MiSTer-devel/Hardware_MiSTer/images/header_2.54mm_Pitch-2x20_Pin-Female-Double_Row-Right_Angle_Pin.jpg

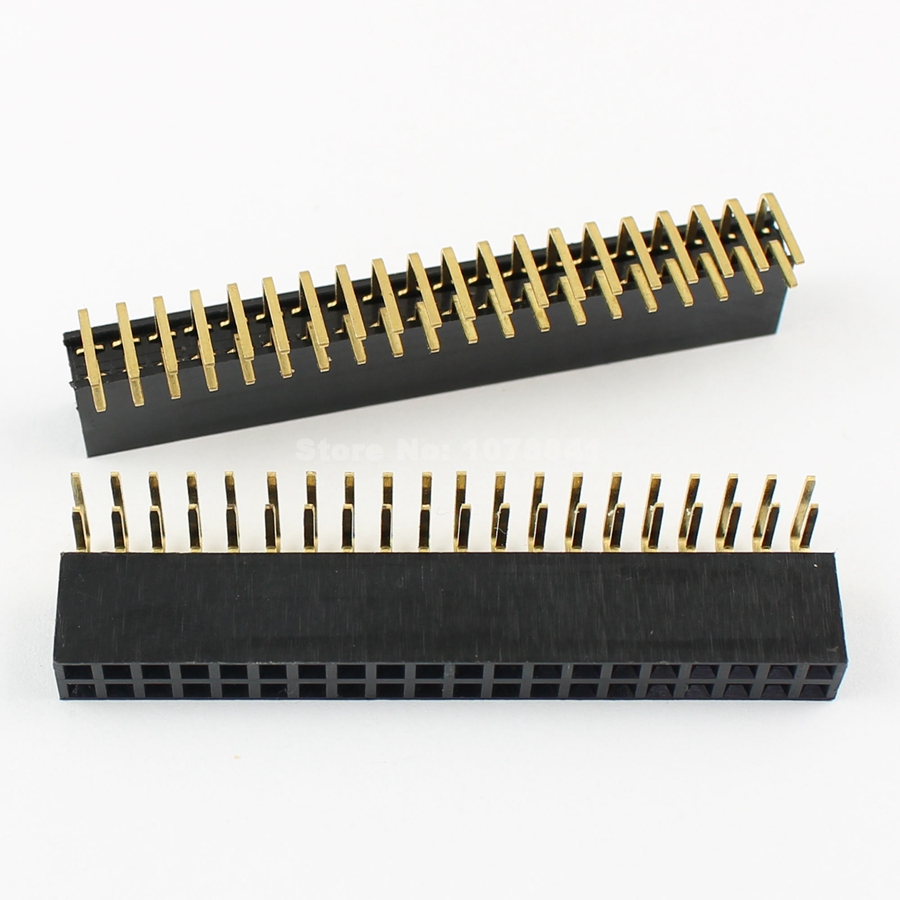
images/header_2.54mm_Pitch-2x20_Pin-Female-Double_Row-Right_Angle_Pin.jpg
