MiSTer-devel/Hardware_MiSTer/images/MiSTer_1.jpg

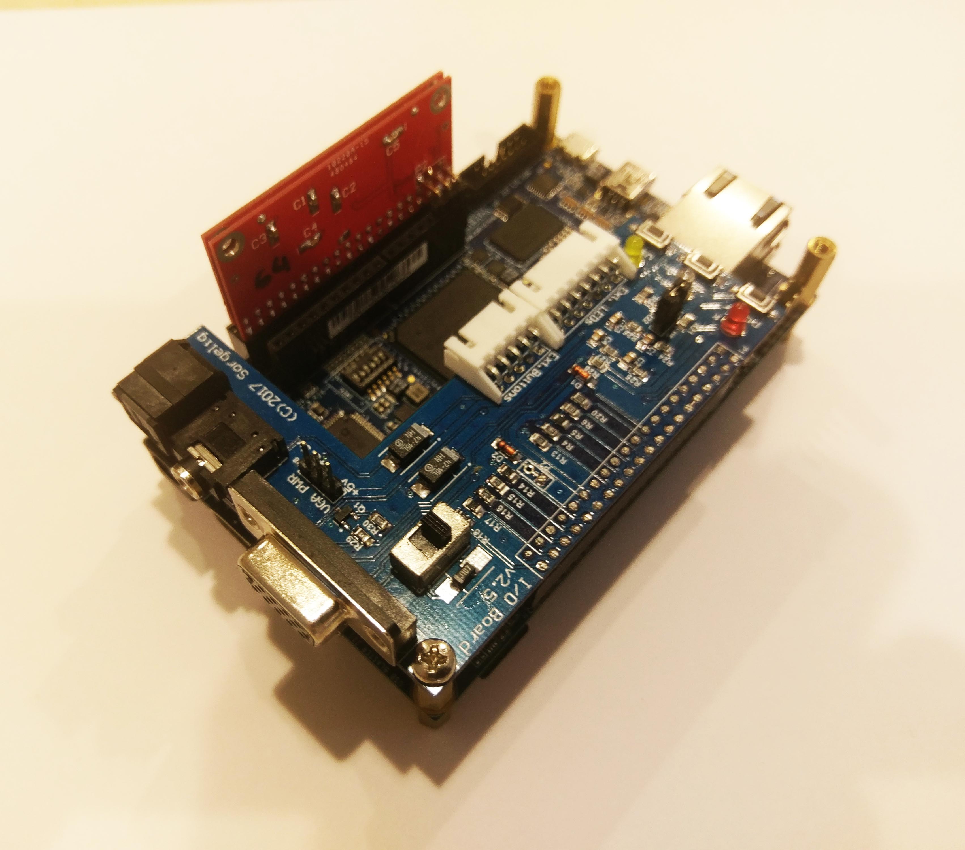
images/MiSTer_1.jpg
