MiSTer-devel/Hardware_MiSTer/images/MiSTer_AIO_SDRAM_rev.jpg

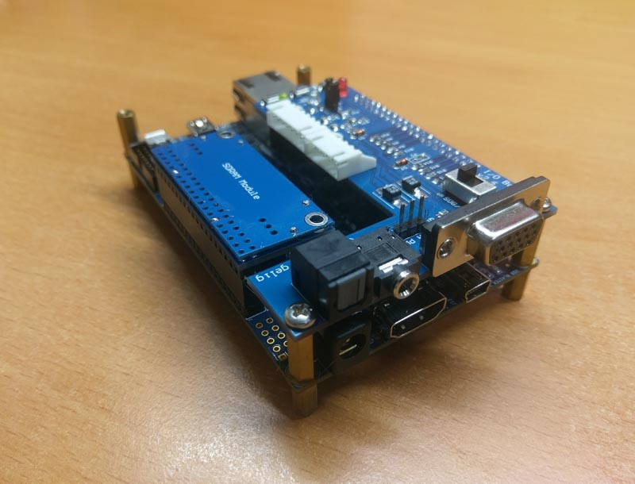
images/MiSTer_AIO_SDRAM_rev.jpg
