MiSTer-devel/Hardware_MiSTer/releases/sdram_xs_2.2.pdf

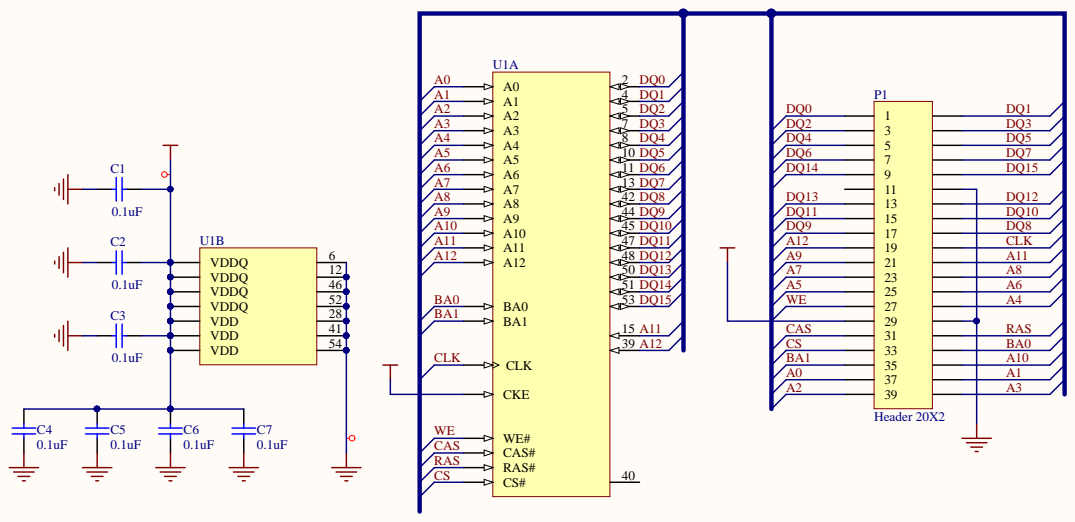
[picture p41: page 1]

SDRAM board for MiSTer (extra slim)

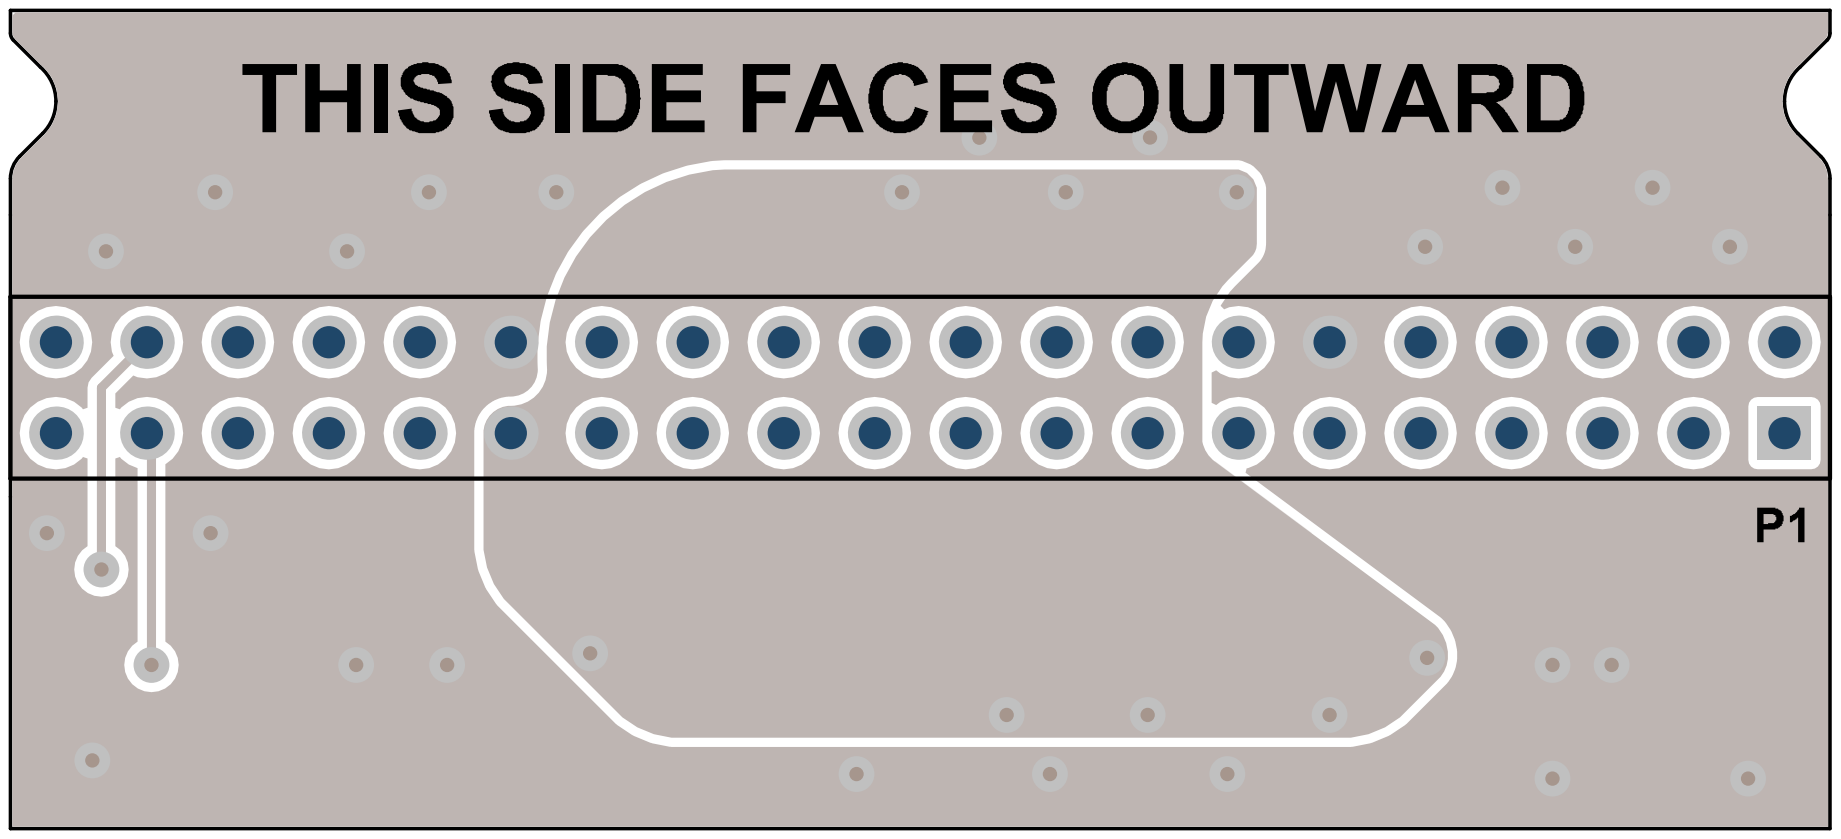
[picture p42: page 2]

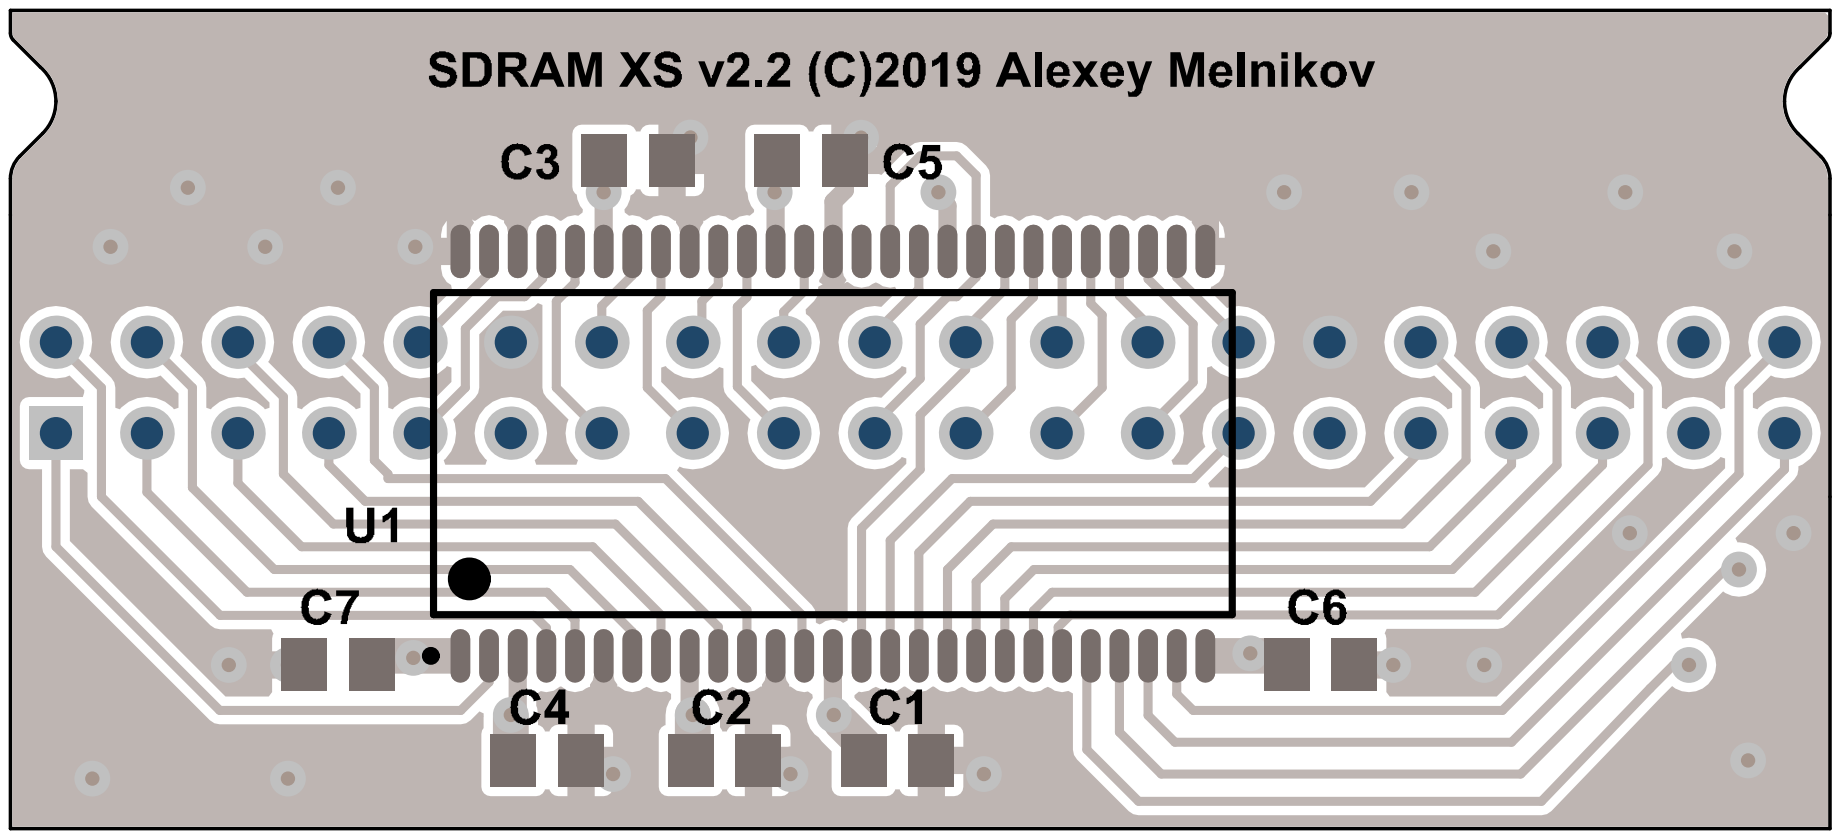
[picture p43: page 3]
