MiSTer-devel/Hardware_MiSTer/releases/iobrd_6.0.pdf

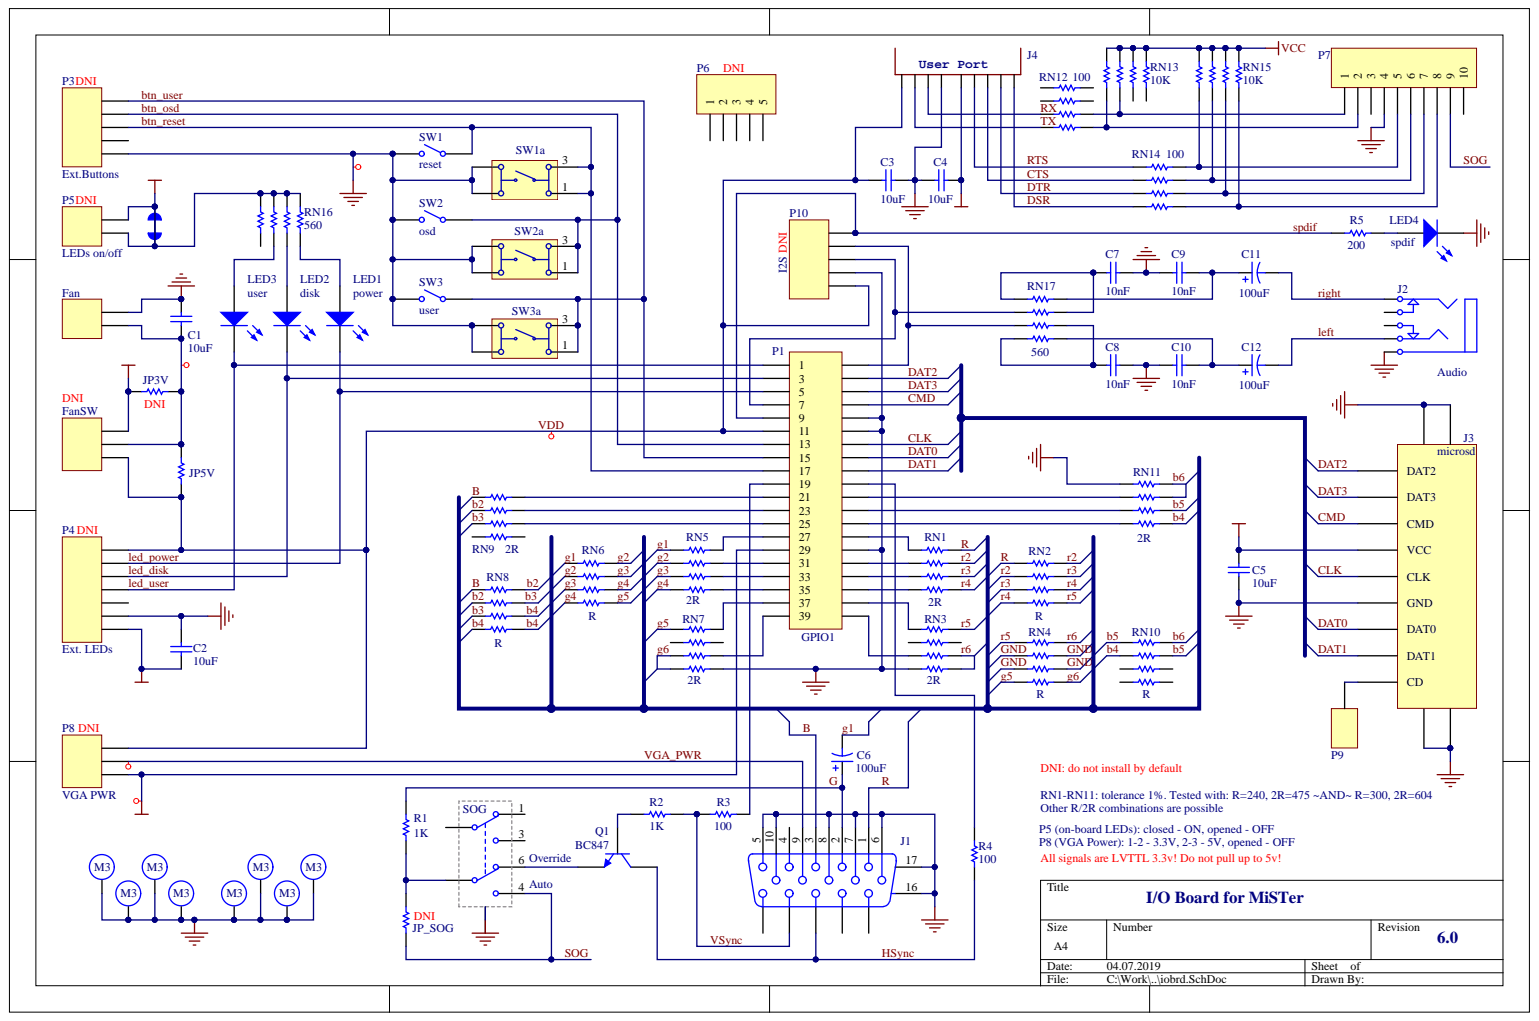
[picture p44: page 1]

C4 | | RTS

CTS
DTR

JP3V | | DAT3

VDD | CMD

CLK

DNI: do not install by default

RN1-RN11: tolerance 1%. Tested with: R=240, 2R=475 ~AND~ R=300, 2R=604
Other R/2R combinations are possible

Override 6 | J1 17

P5 (on-board LEDs): closed - ON, opened - OFF
P8 (VGA Power): 1-2 - 3.3V, 2-3 - 5V, opened - OFF
All signals are LVTTL 3.3v! Do not pull up to 5v!

VSync | 16

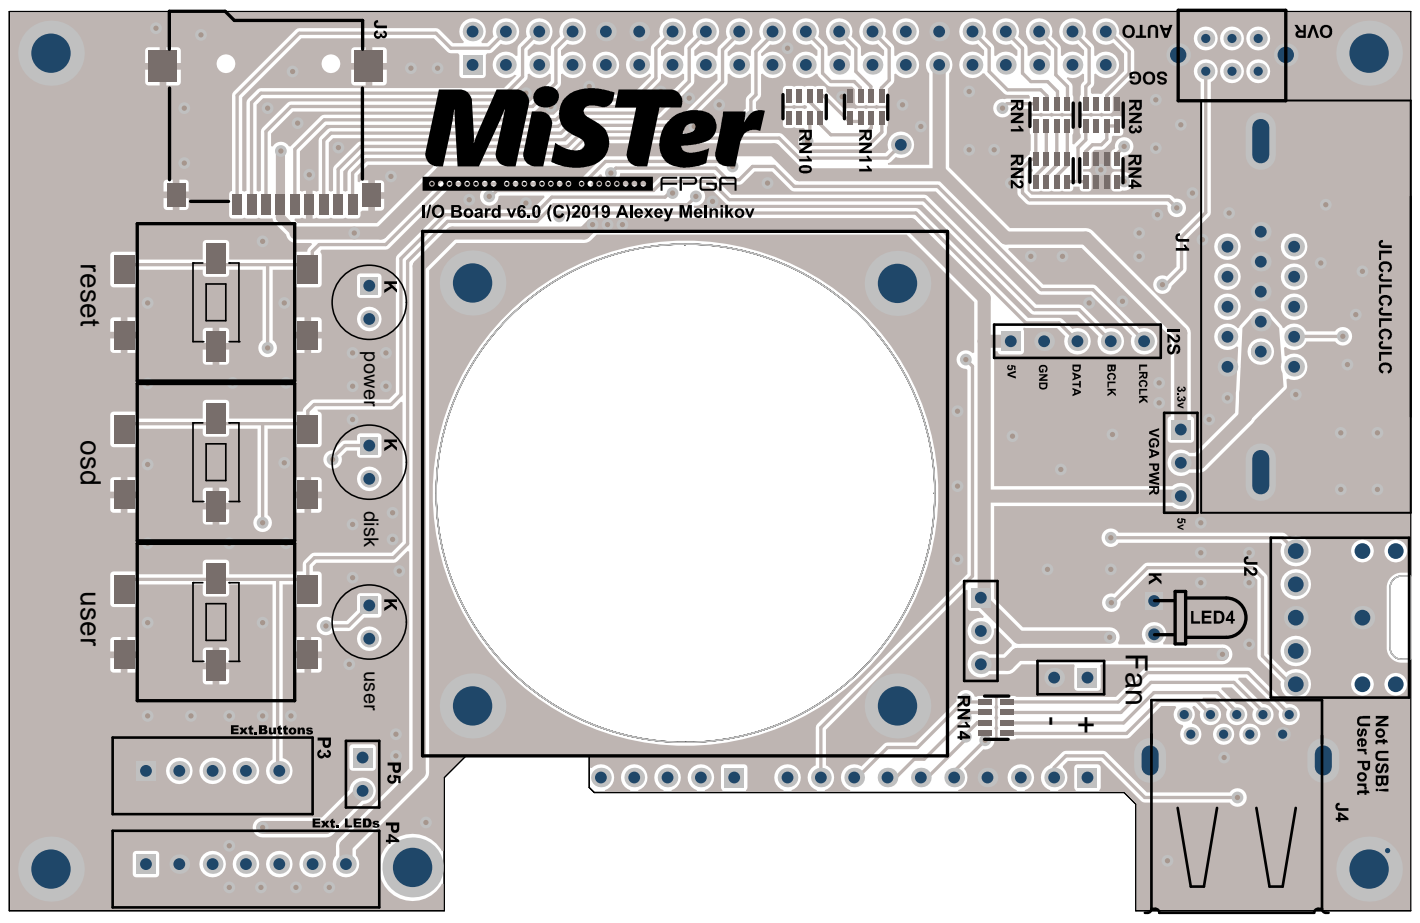
[picture p45: page 2]

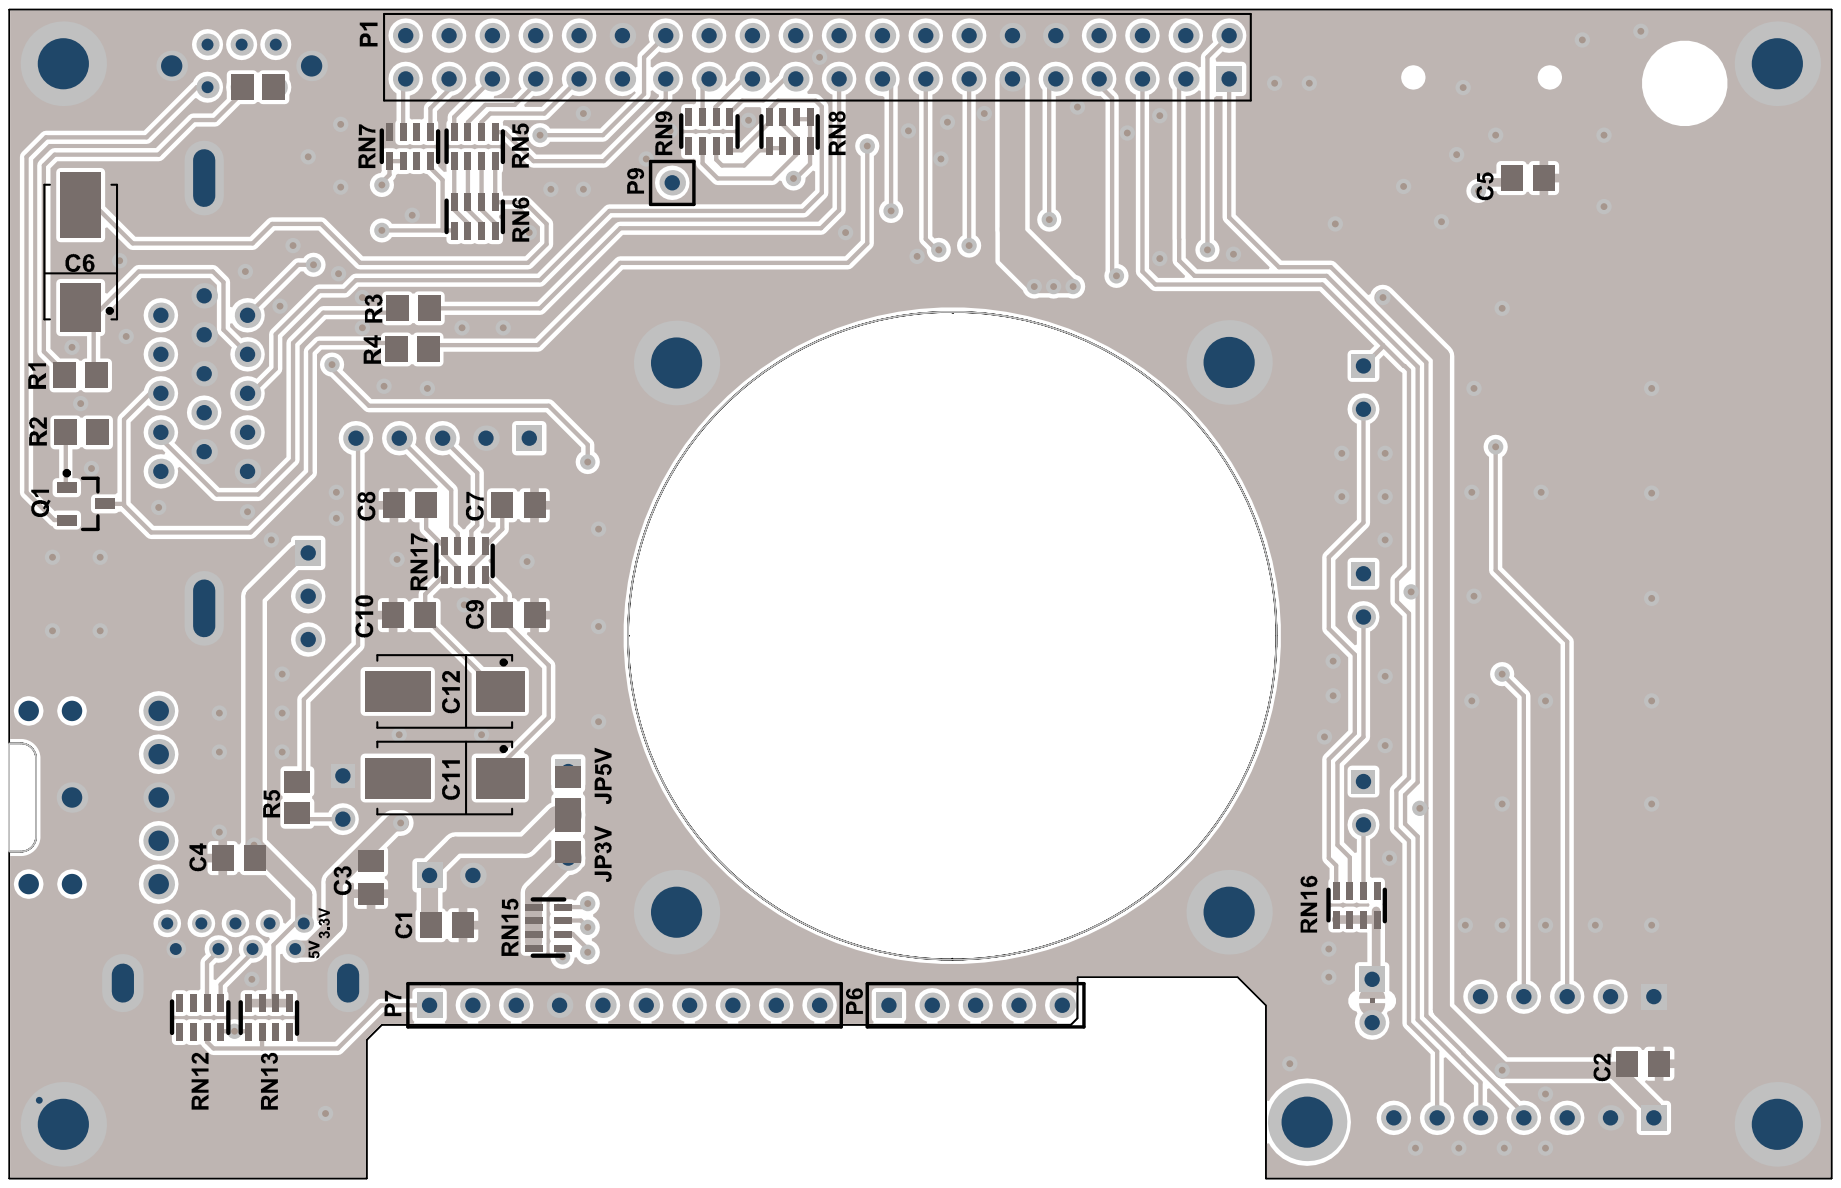
[picture p46: page 3]
