MiSTer-devel/Hardware_MiSTer/releases/USBHub_2.1.pdf

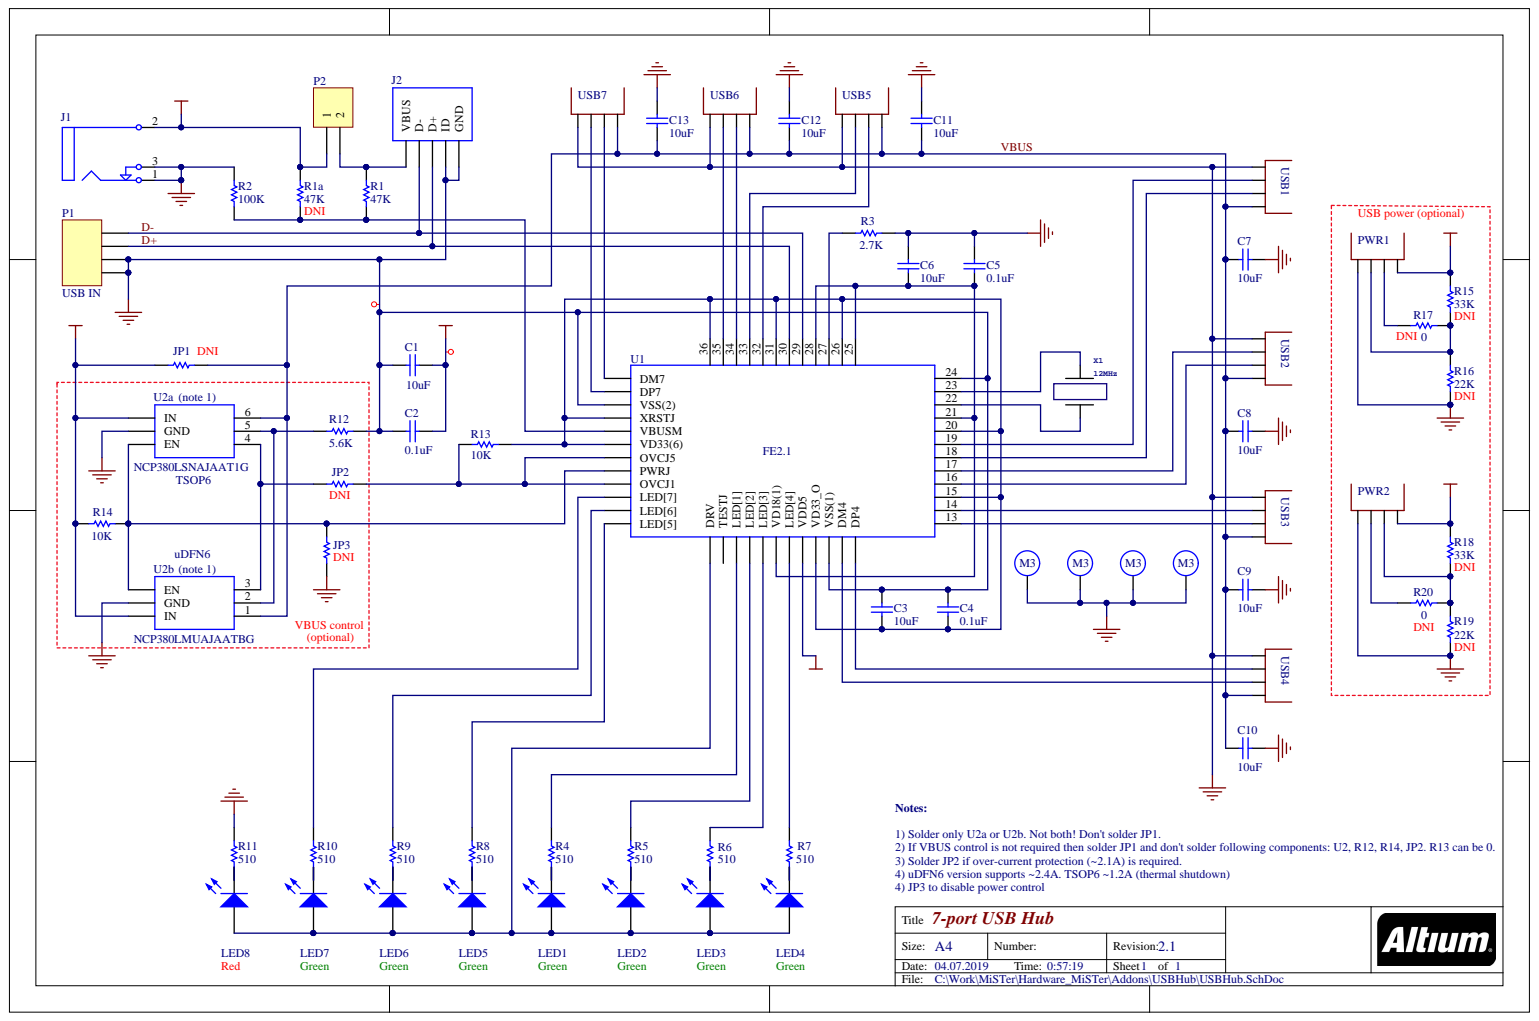
[picture p47: page 1]

DNI 0

1) Solder only U2a or U2b. Not both! Don't solder JP1.
2) If VBUS control is not required then solder JP1 and don't solder following components: U2, R12, R14, JP2. R13 can be 0.
3) Solder JP2 if over-current protection (~2.1A) is required.
4) uDFN6 version supports ~2.4A. TSOP6 ~1.2A (thermal shutdown)
4) JP3 to disable power control

7-port USB Hub Title

Size: A4 | Number: | Revision: 2.1
Date: 04.07.2019 Time: 0:57:19 | | Sheet 1 of 1

C:\Work\MiSTer\Hardware_MiSTer\Addons\USBHub\USBHub.SchDoc

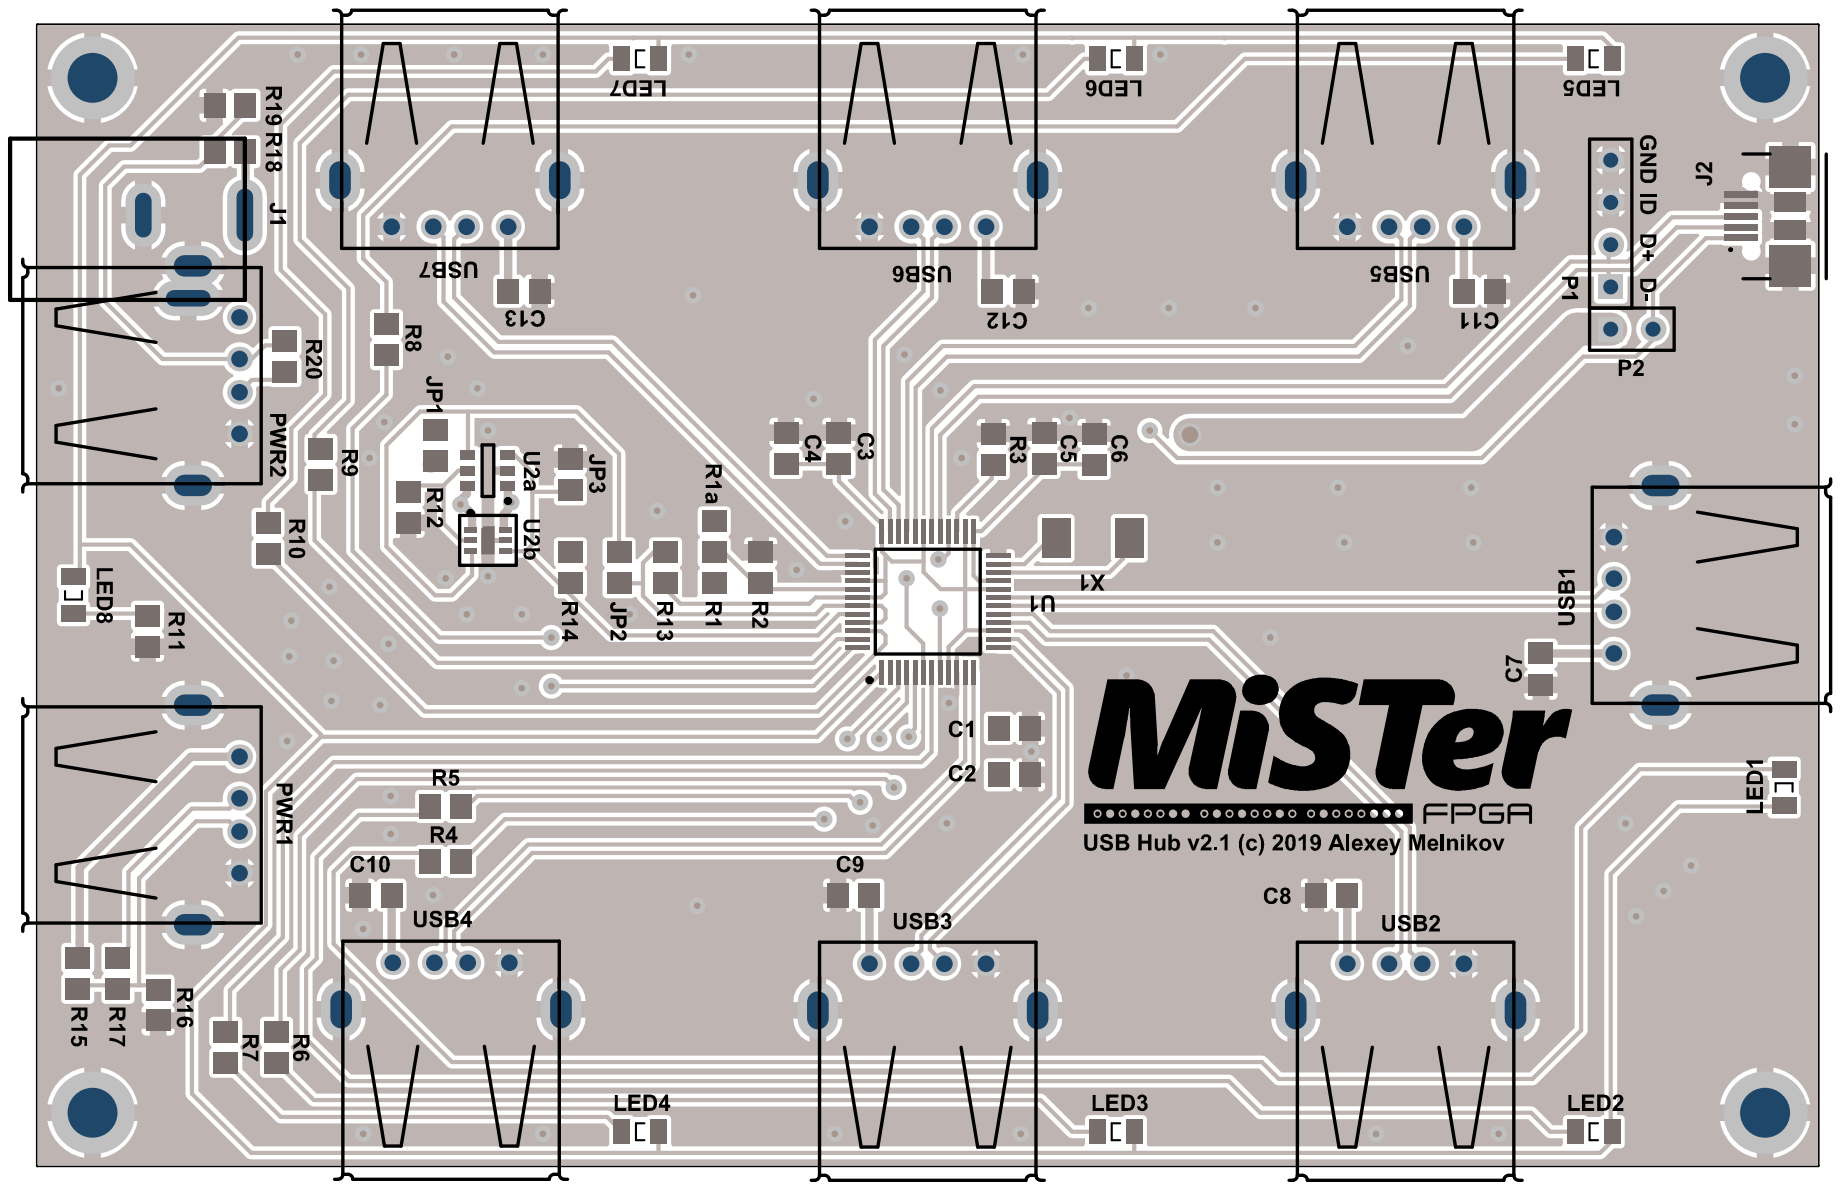
[picture p48: page 2]

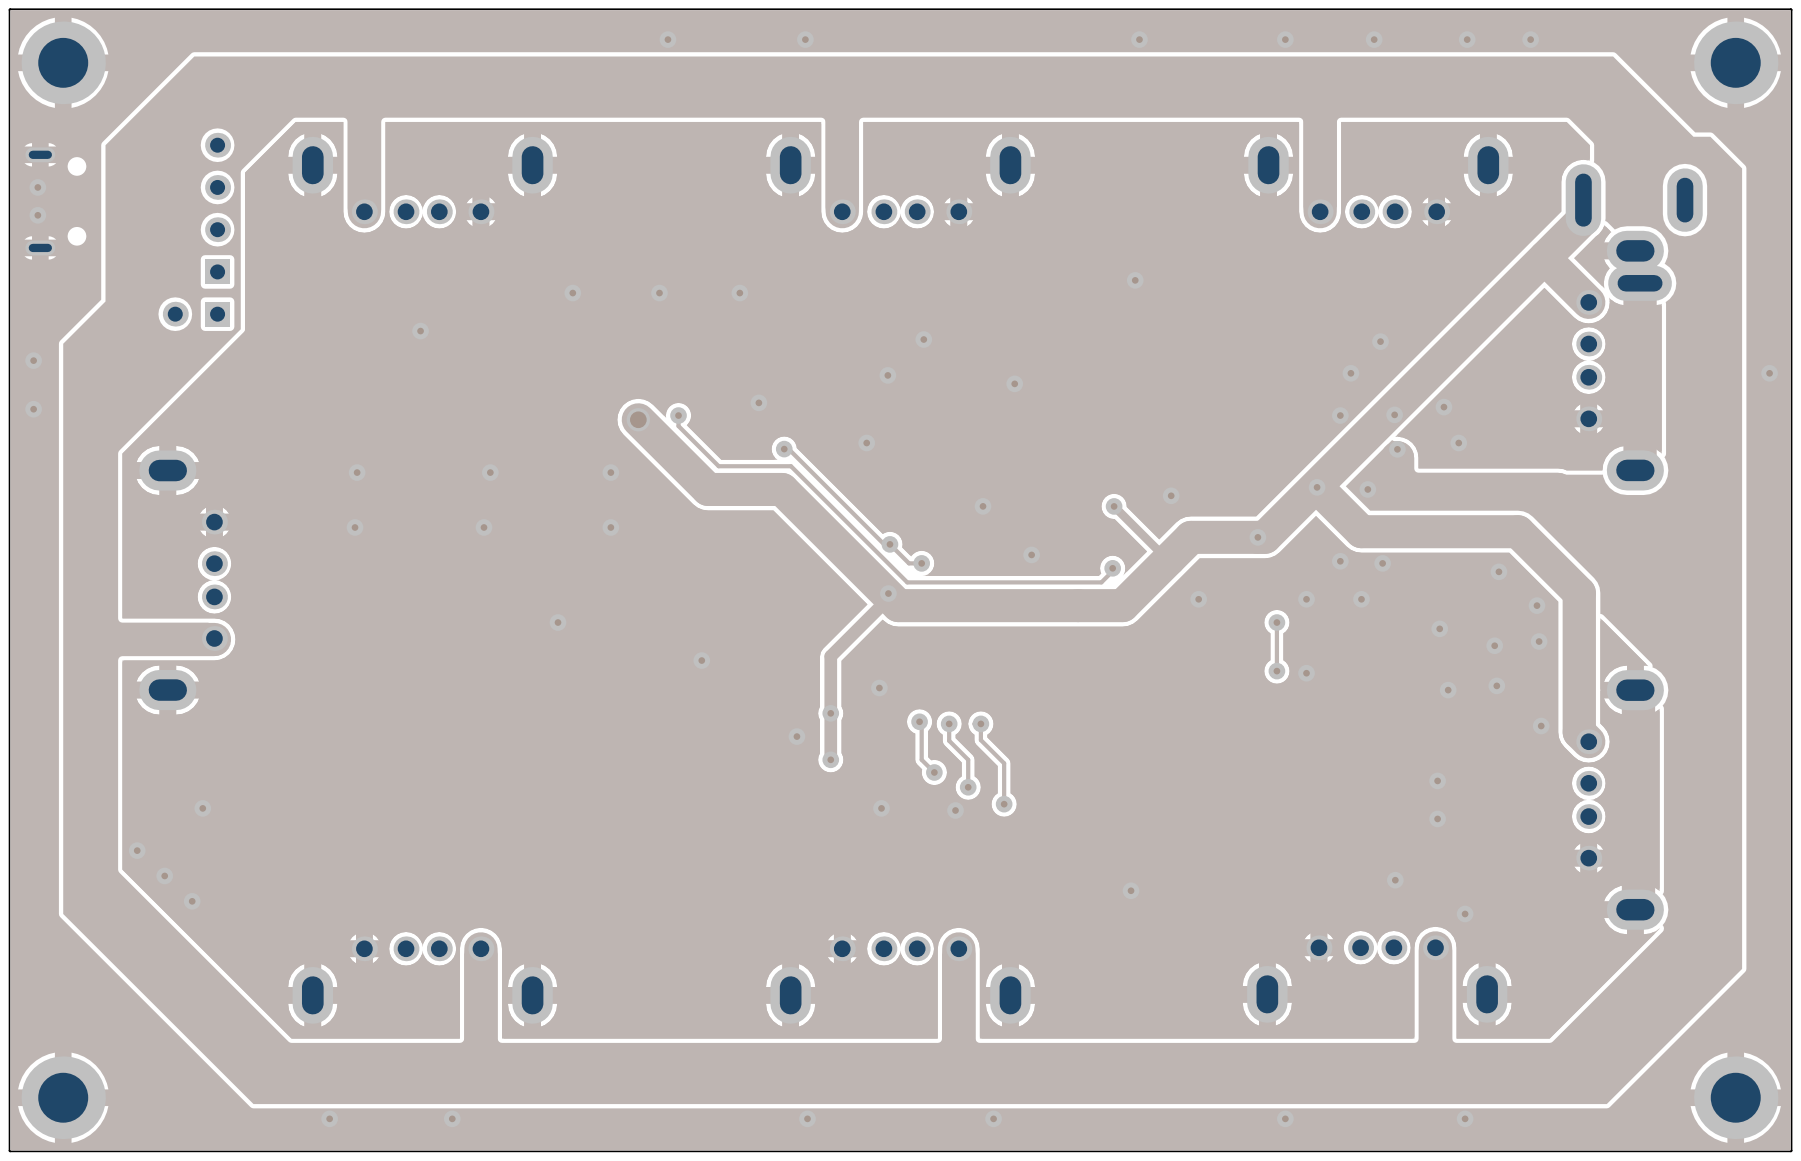
[picture p49: page 3]
