MiSTer-devel/Hardware_MiSTer/releases/ADCin_1.1.pdf

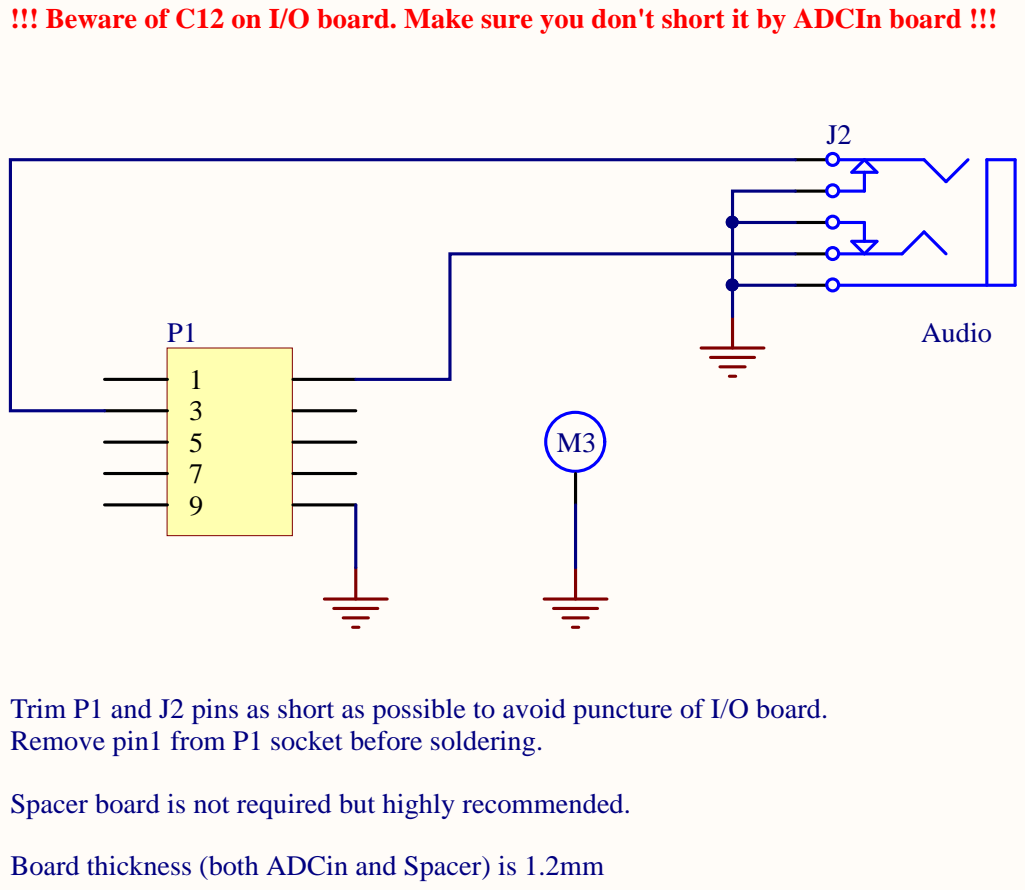
[picture p50: page 1]

!!! Beware of C12 on I/O board. Make sure you don't short it by ADCIn board !!!

Board thickness (both ADCin and Spacer) is 1.2mm Trim P1 and J2 pins as short as possible to avoid puncture of I/O board.
Remove pin1 from P1 socket before soldering.

Spacer board is not required but highly recommended.

ADC input board for MiSTer

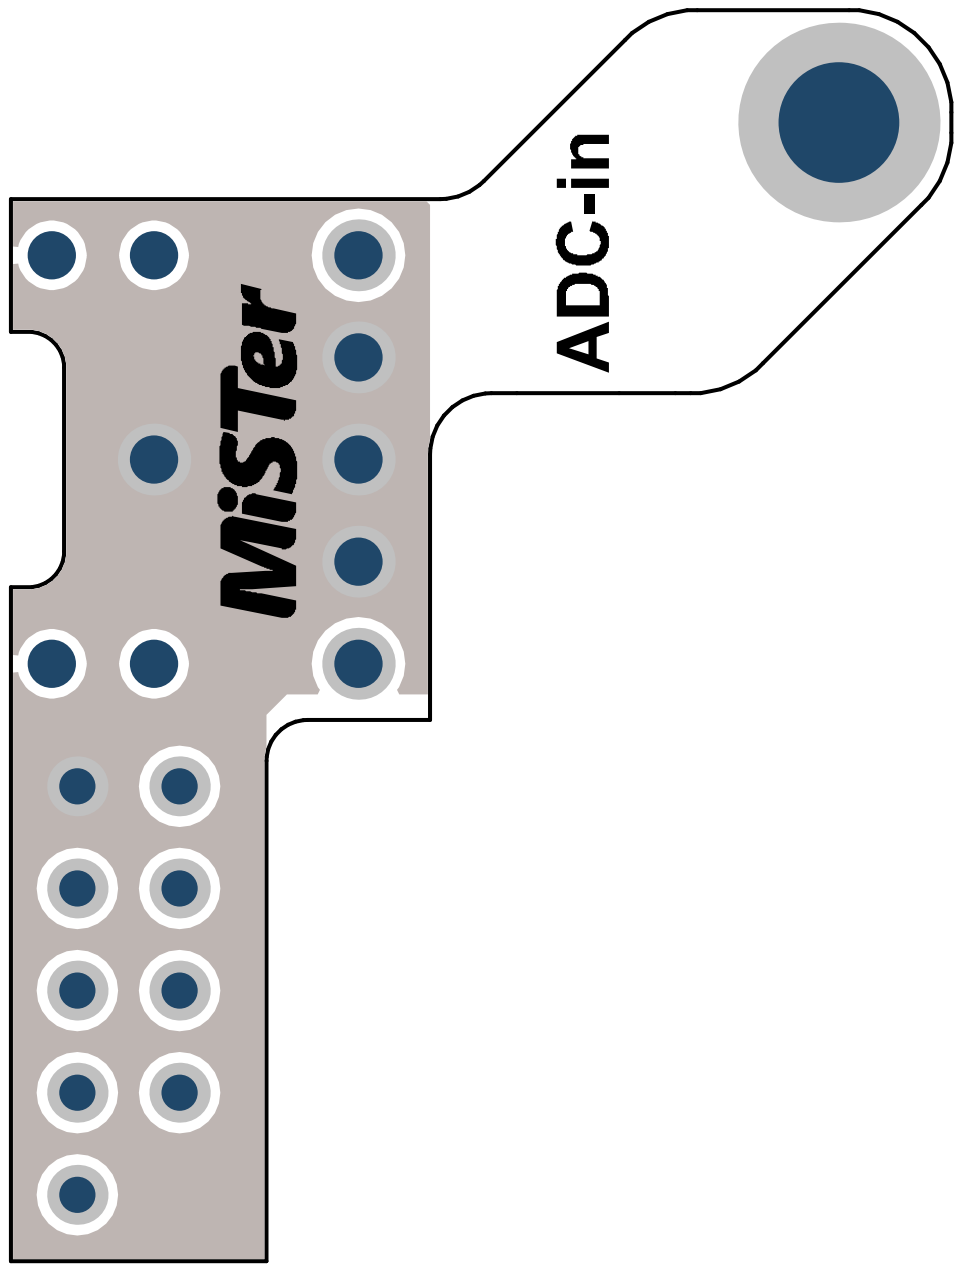
[picture p51: page 2]

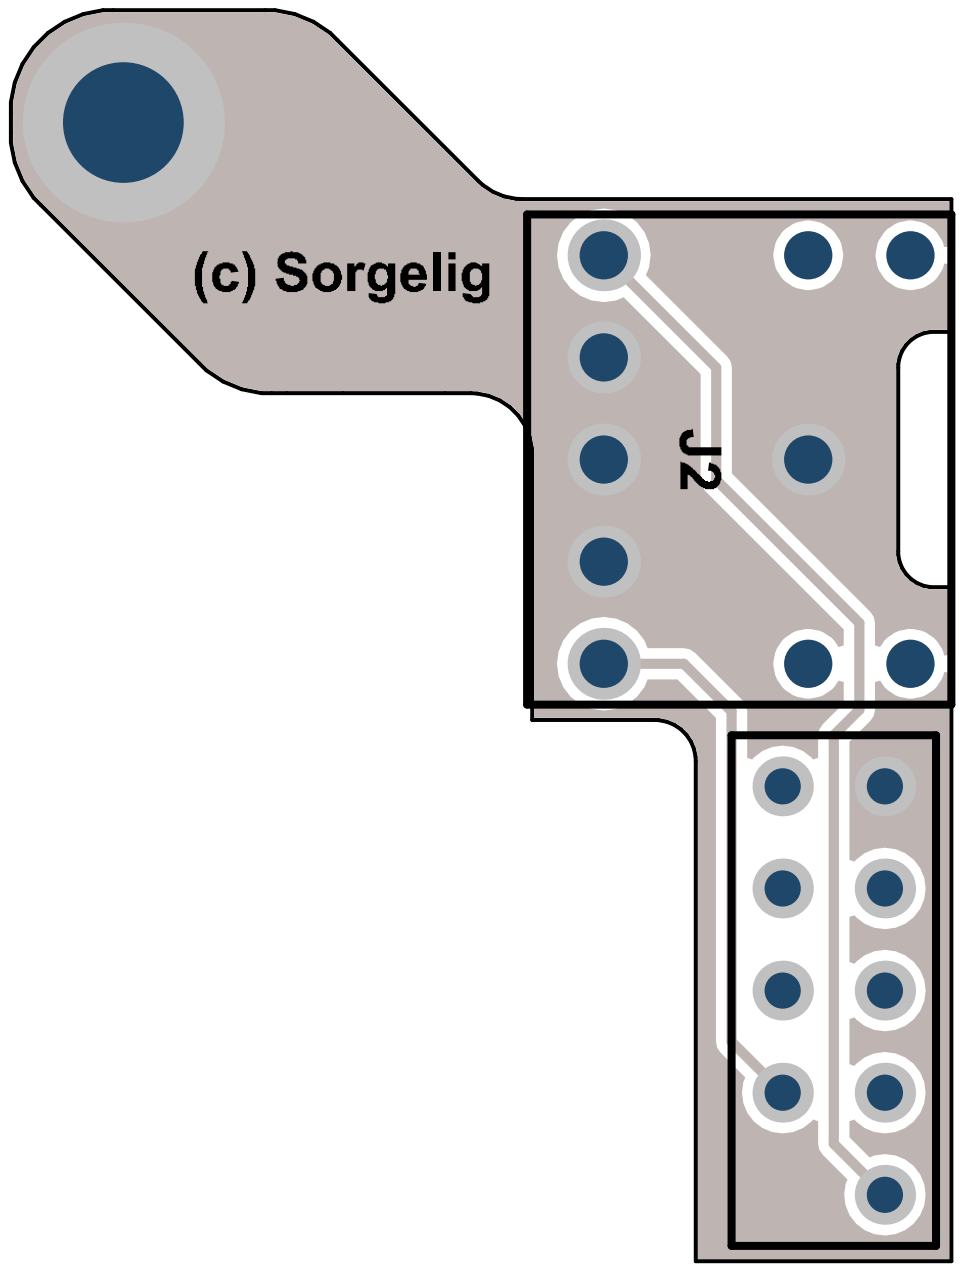
[picture p52: page 3]
