MiSTer-devel/Hardware_MiSTer/releases/iobrd_5.6.pdf

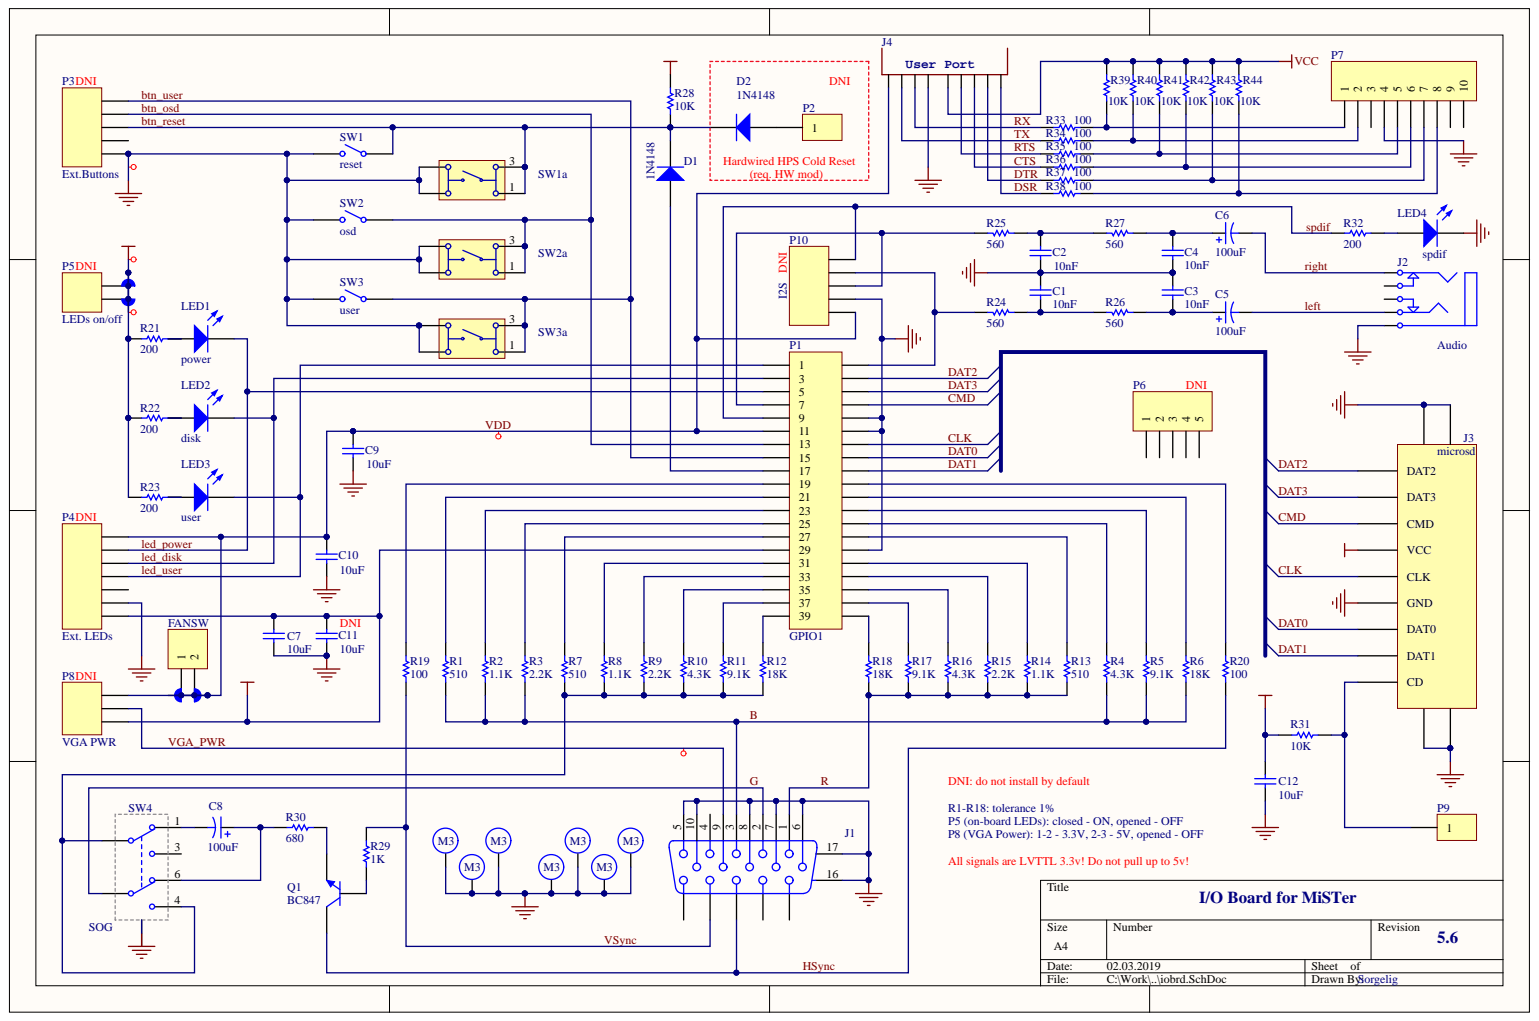
[picture p53: page 1]

btn_osd 10K

Hardwired HPS Cold Reset
(req. HW mod)

DAT2

LED2 | | | | DAT3

VDD | | | CMD

CLK

led_power
led_disk
led_user | 10uF

DNI: do not install by default

R1-R18: tolerance 1%
P5 (on-board LEDs): closed - ON, opened - OFF
P8 (VGA Power): 1-2 - 3.3V, 2-3 - 5V, opened - OFF

All signals are LVTTL 3.3v! Do not pull up to 5v!

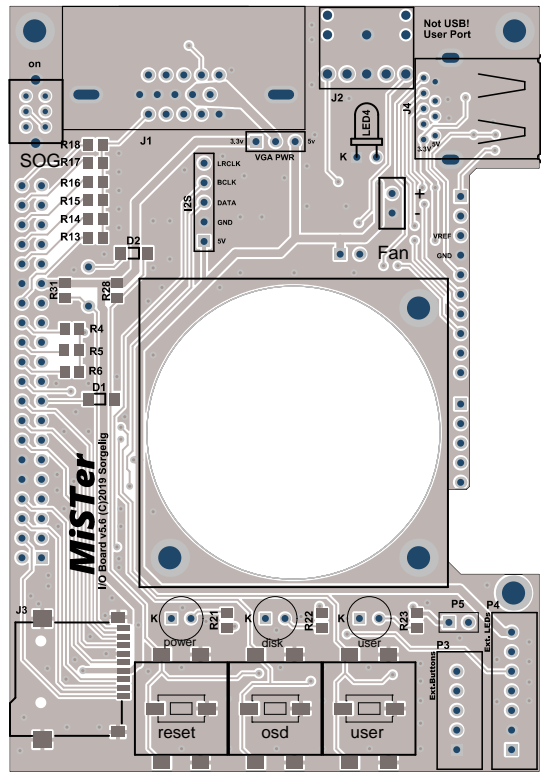
[picture p54: page 2]

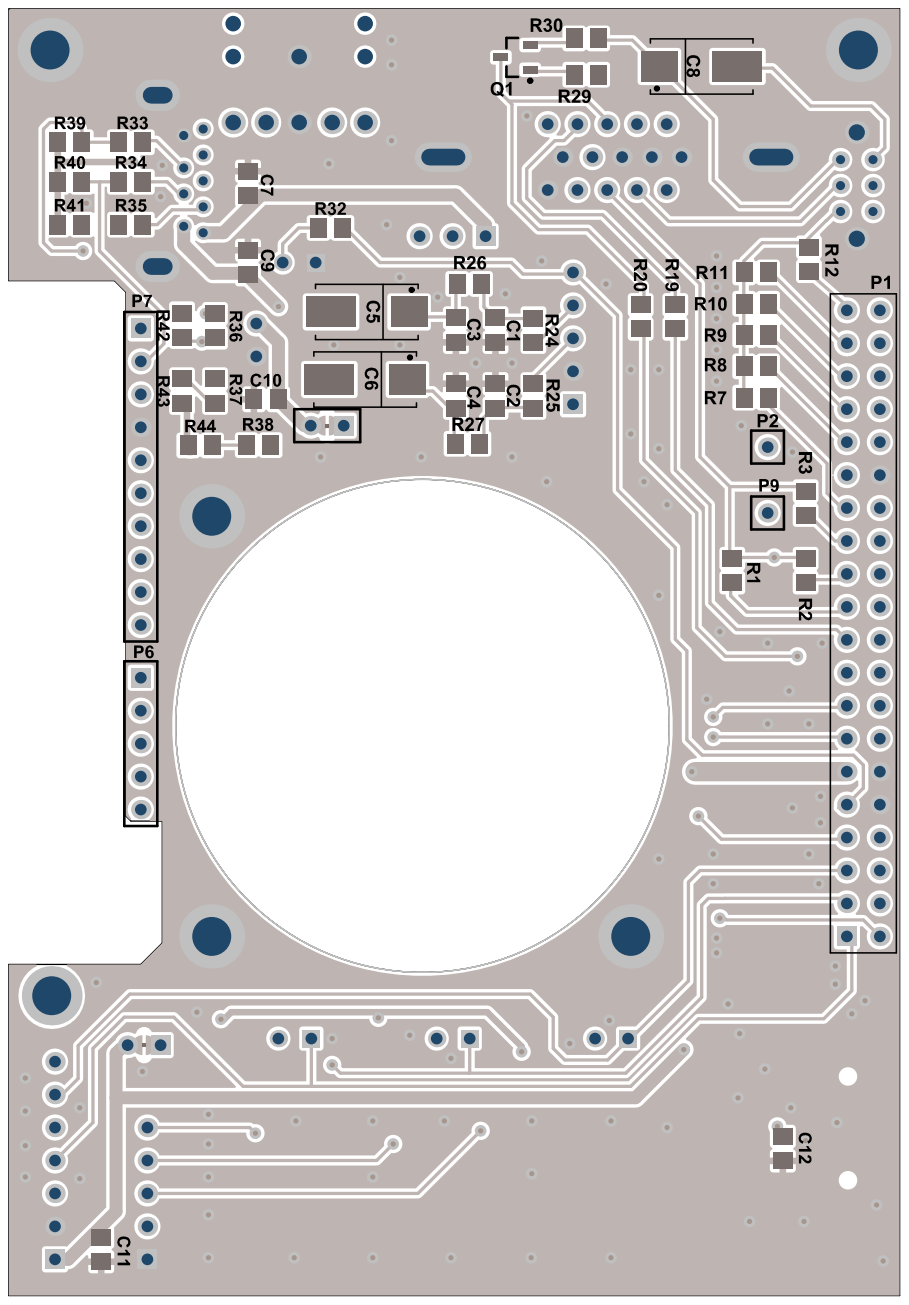
[picture p55: page 3]
