MiSTer-devel/Hardware_MiSTer/releases/iobrd_5.5.pdf

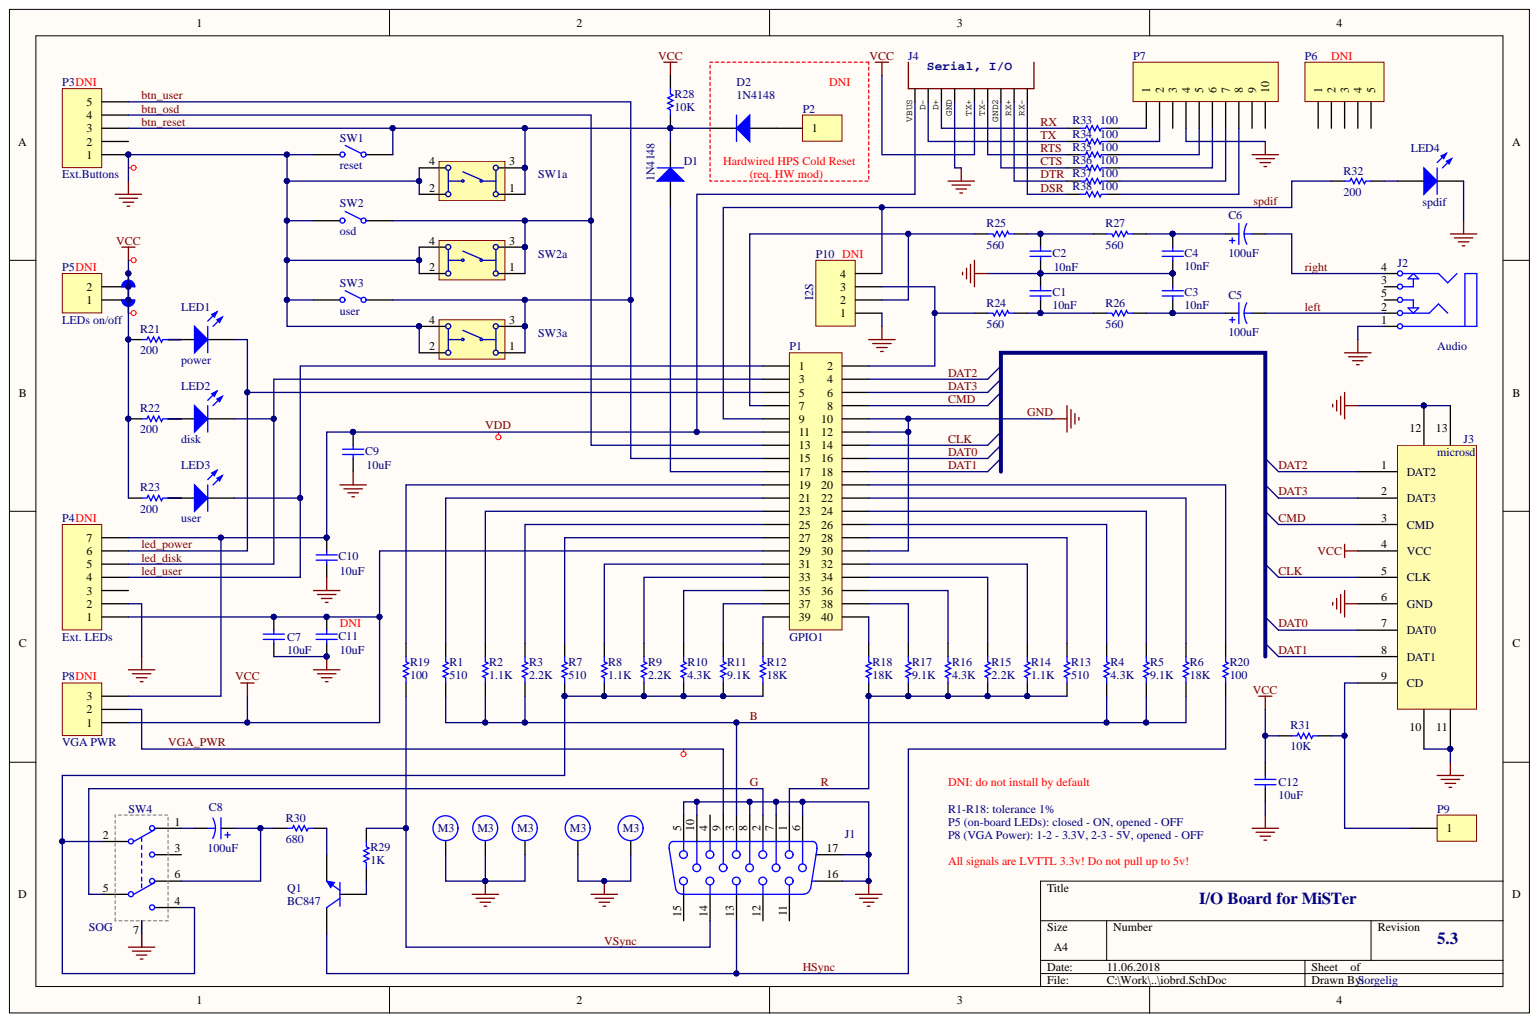
[picture p56: page 1]

Hardwired HPS Cold Reset
(req. HW mod)

DAT2

LED2 | | | DAT3

VDD | | CMD

DNI: do not install by default

R1-R18: tolerance 1%
P5 (on-board LEDs): closed - ON, opened - OFF
P8 (VGA Power): 1-2 - 3.3V, 2-3 - 5V, opened - OFF

All signals are LVTTL 3.3v! Do not pull up to 5v!

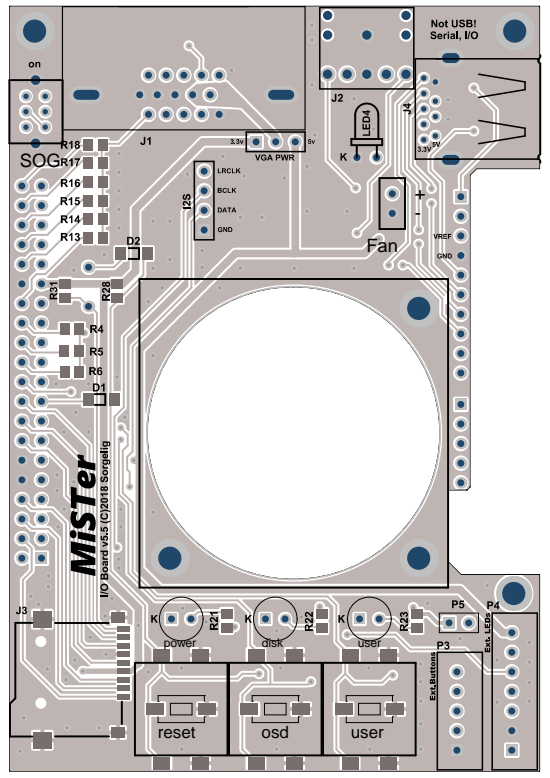
[picture p57: page 2]

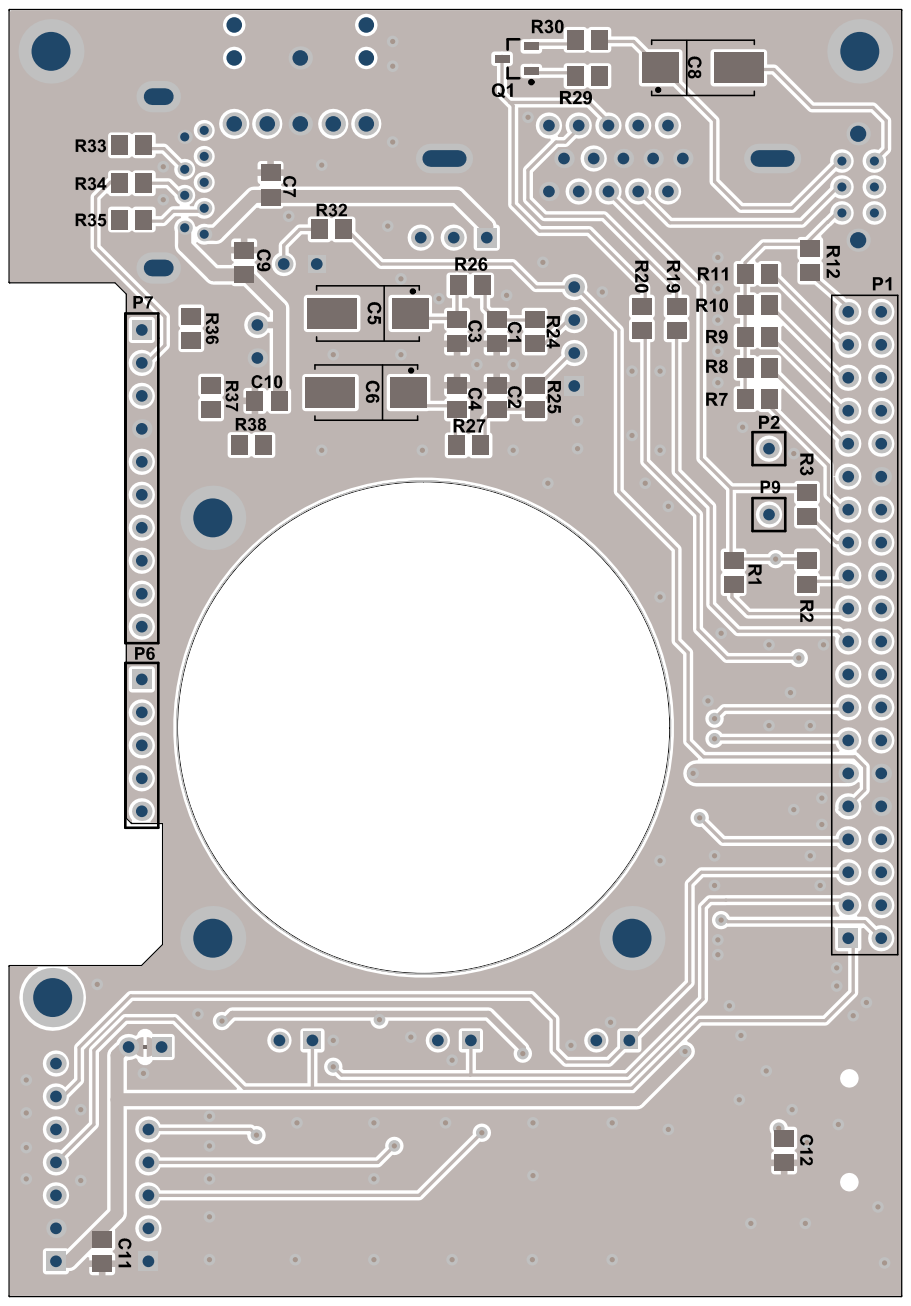
[picture p58: page 3]
