MiSTer-devel/Hardware_MiSTer/releases/USBHub_1.0.pdf

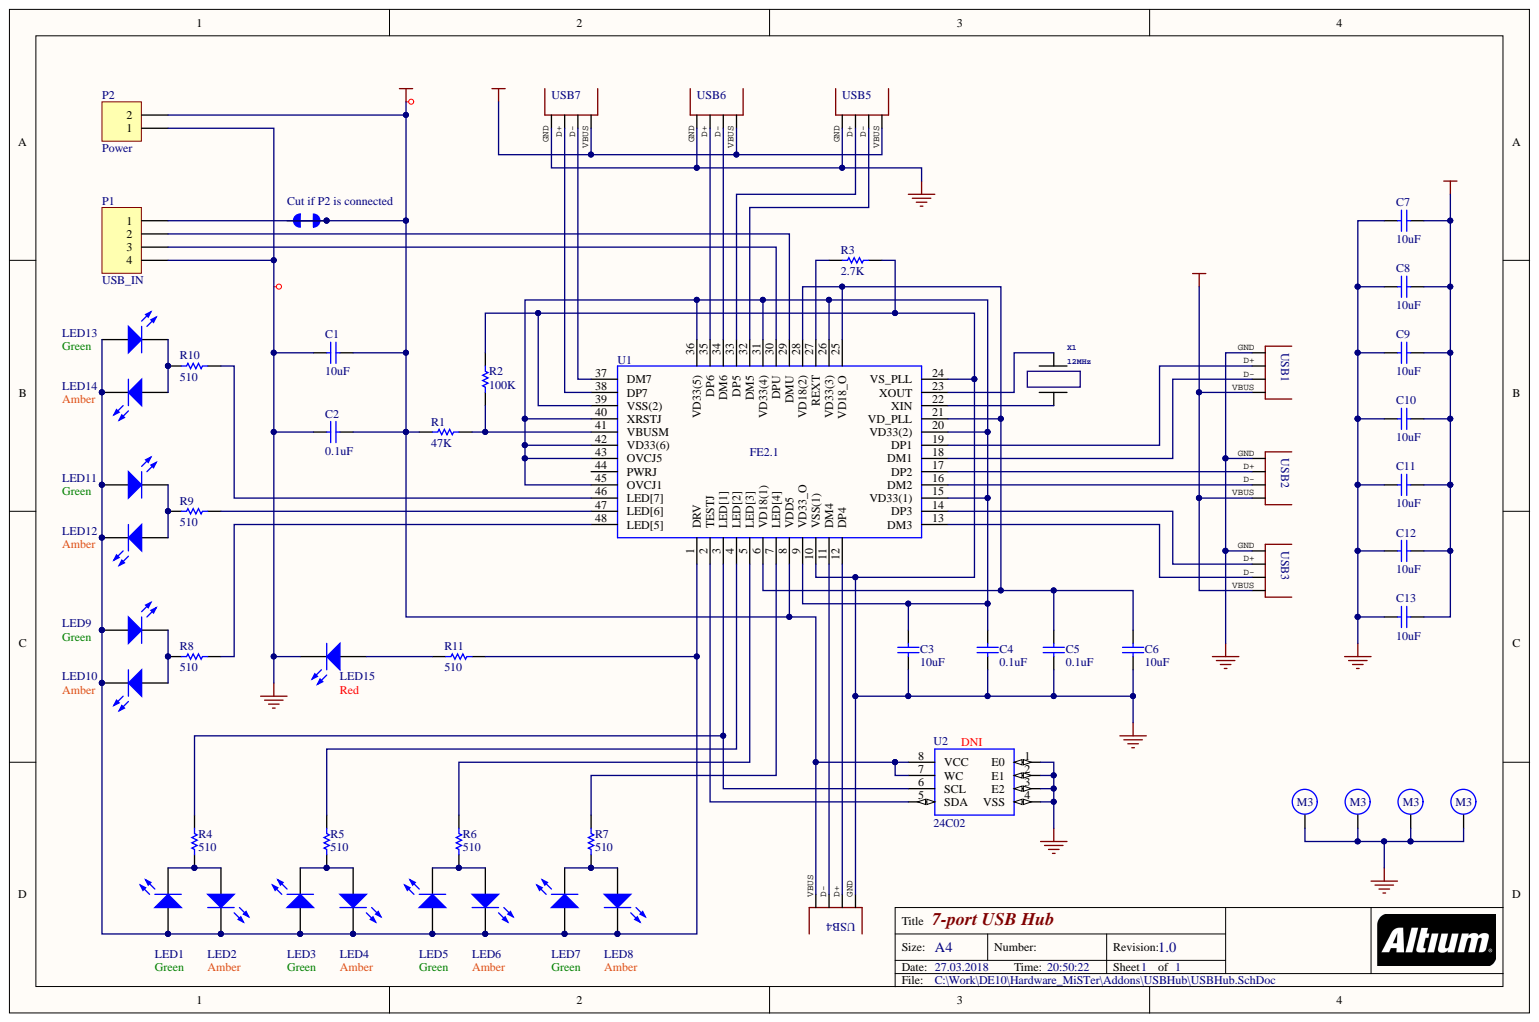
[picture p59: page 1]

Cut if P2 is connected

D-
VBUS

D+

Red | | D-

U2 DNI
VCC 8 | E1 E2
WC 7 | 2
SCL 6 | 3
SDA 5

7-port USB Hub Title

A4 Size: | Number: | 1.0 Revision:
Date: 27.03.2018 Time: 20:50:22 | | Sheet 1 of 1

C:\Work\DE10\Hardware_MiSTer\Addons\USBHub\USBHub.SchDoc

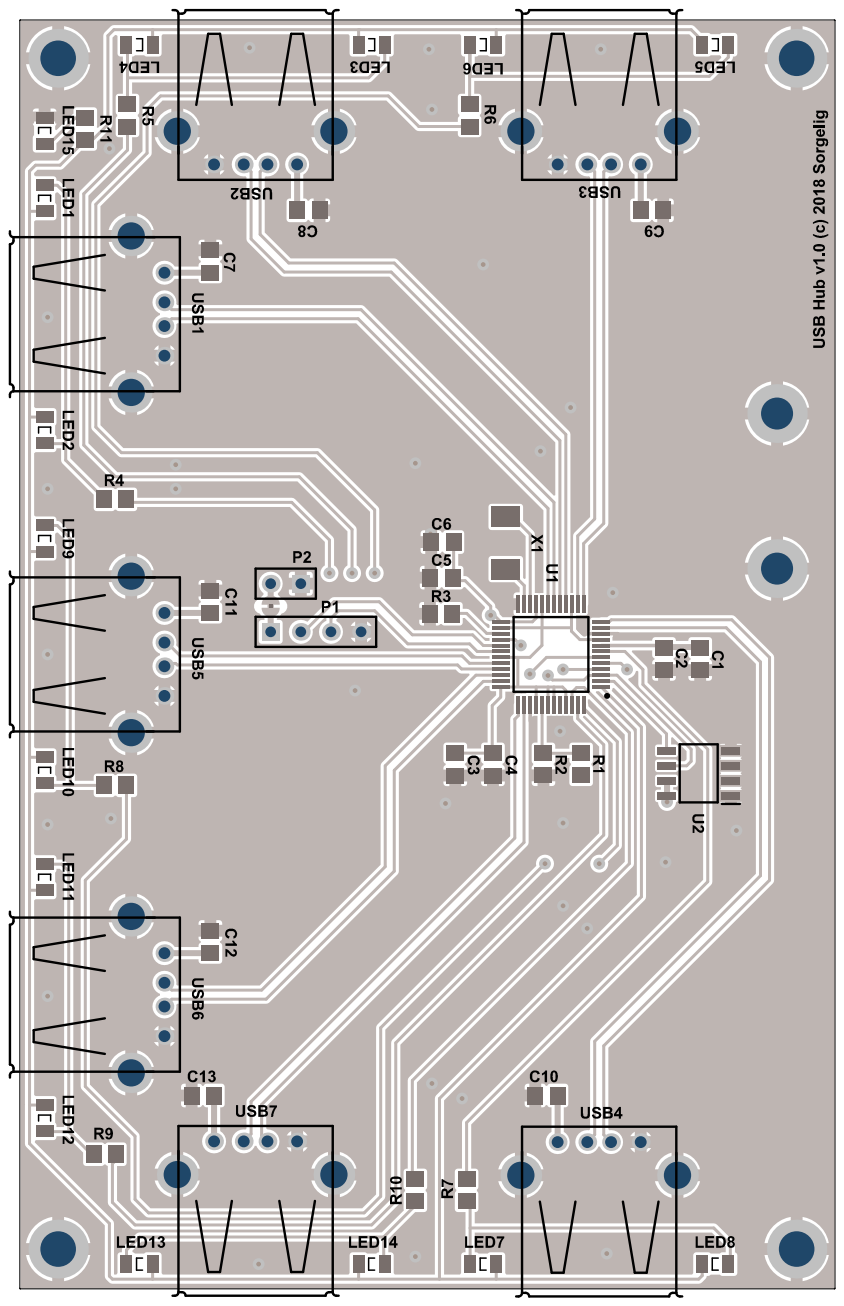
[picture p60: page 2]

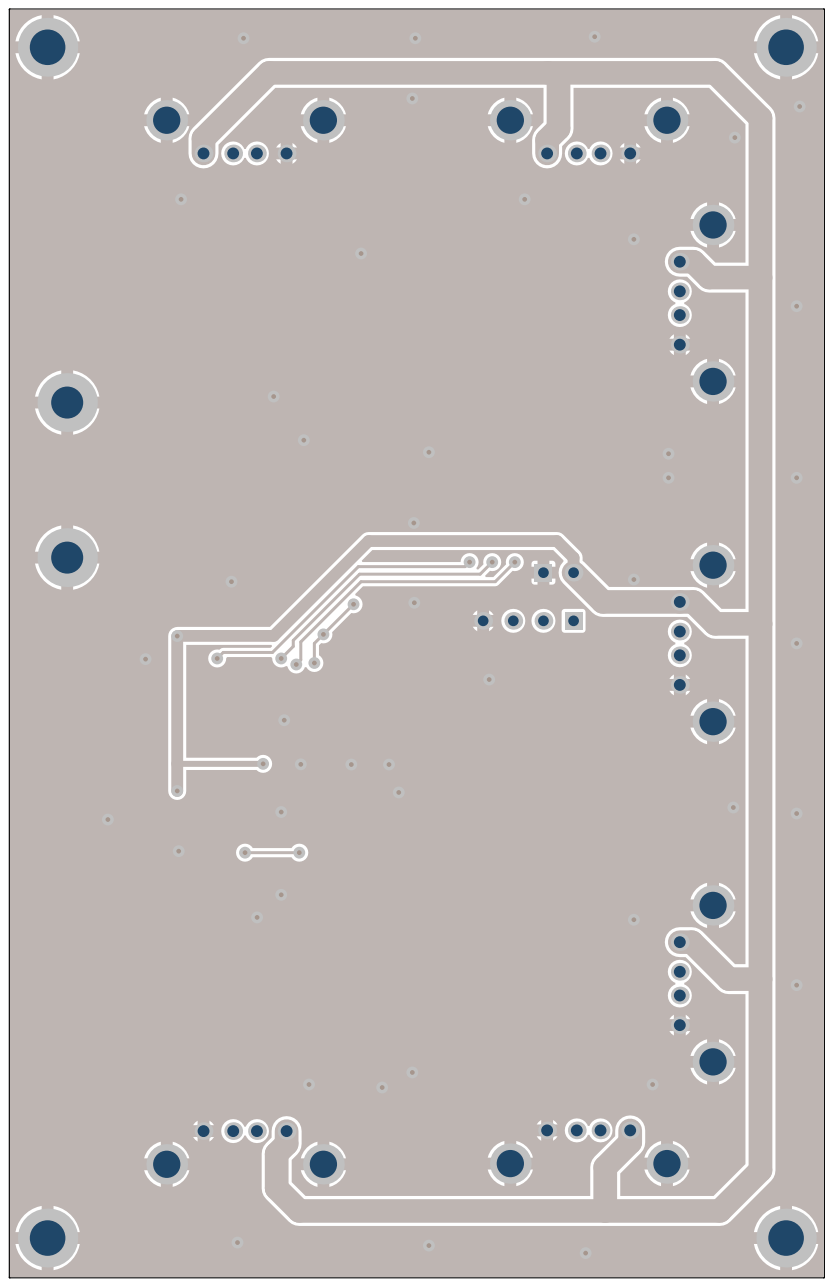
[picture p61: page 3]
