MiSTer-devel/Hardware_MiSTer/releases/rtc_1.3.pdf

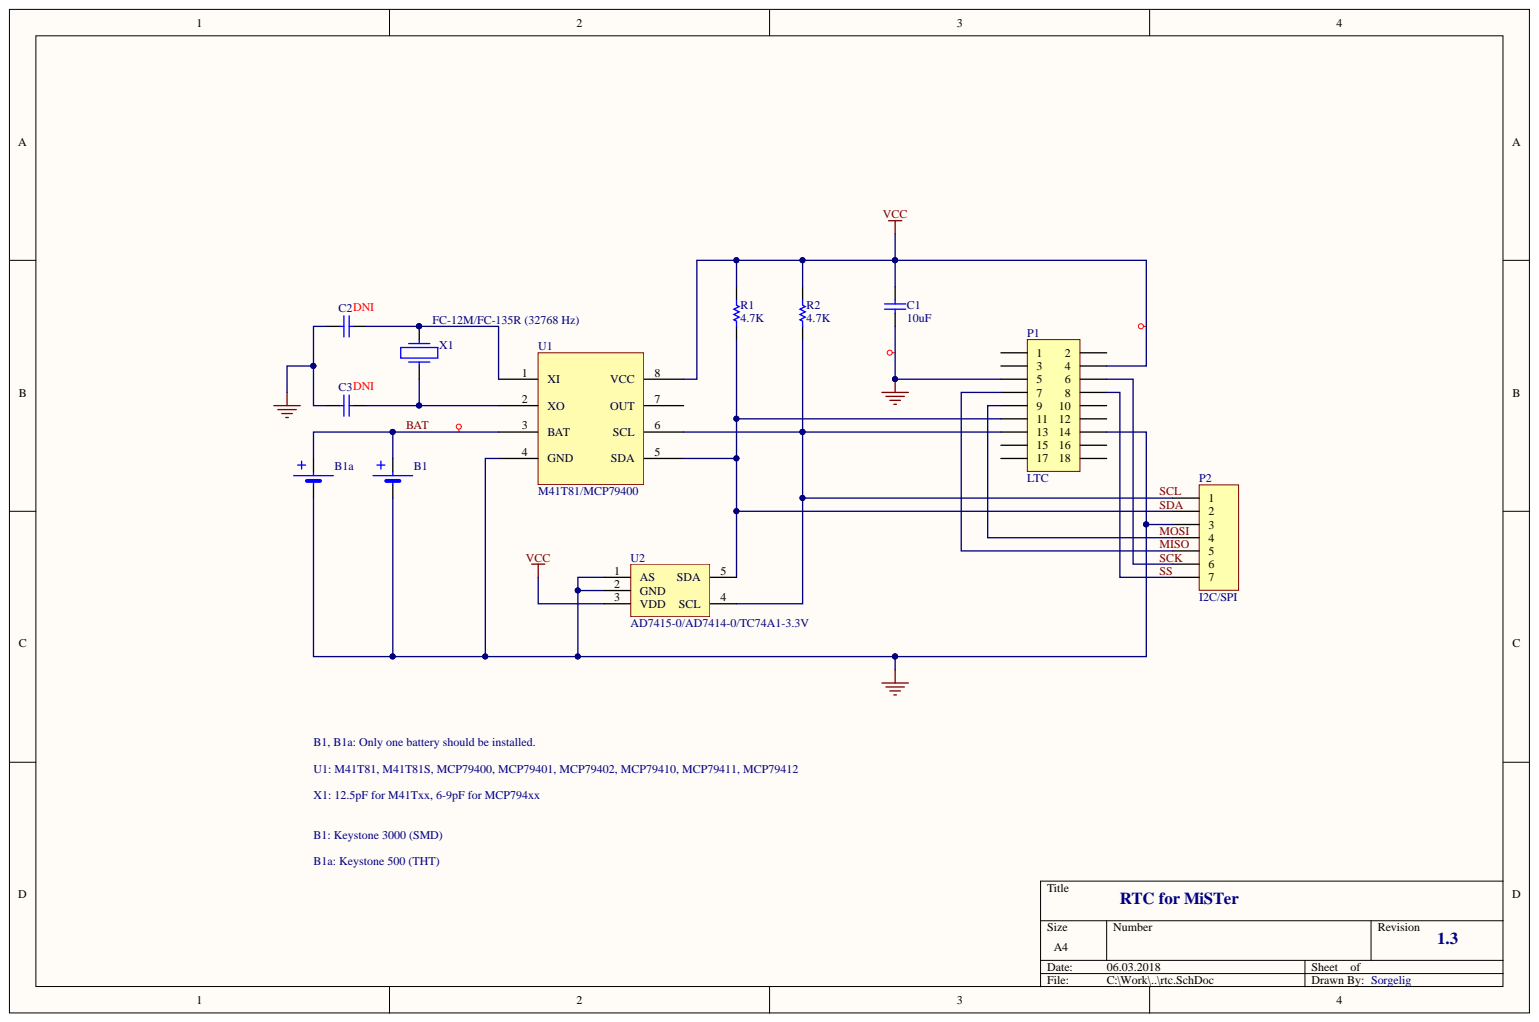
[picture p62: page 1]

MOSI
MISO
SCK

B1, B1a: Only one battery should be installed.

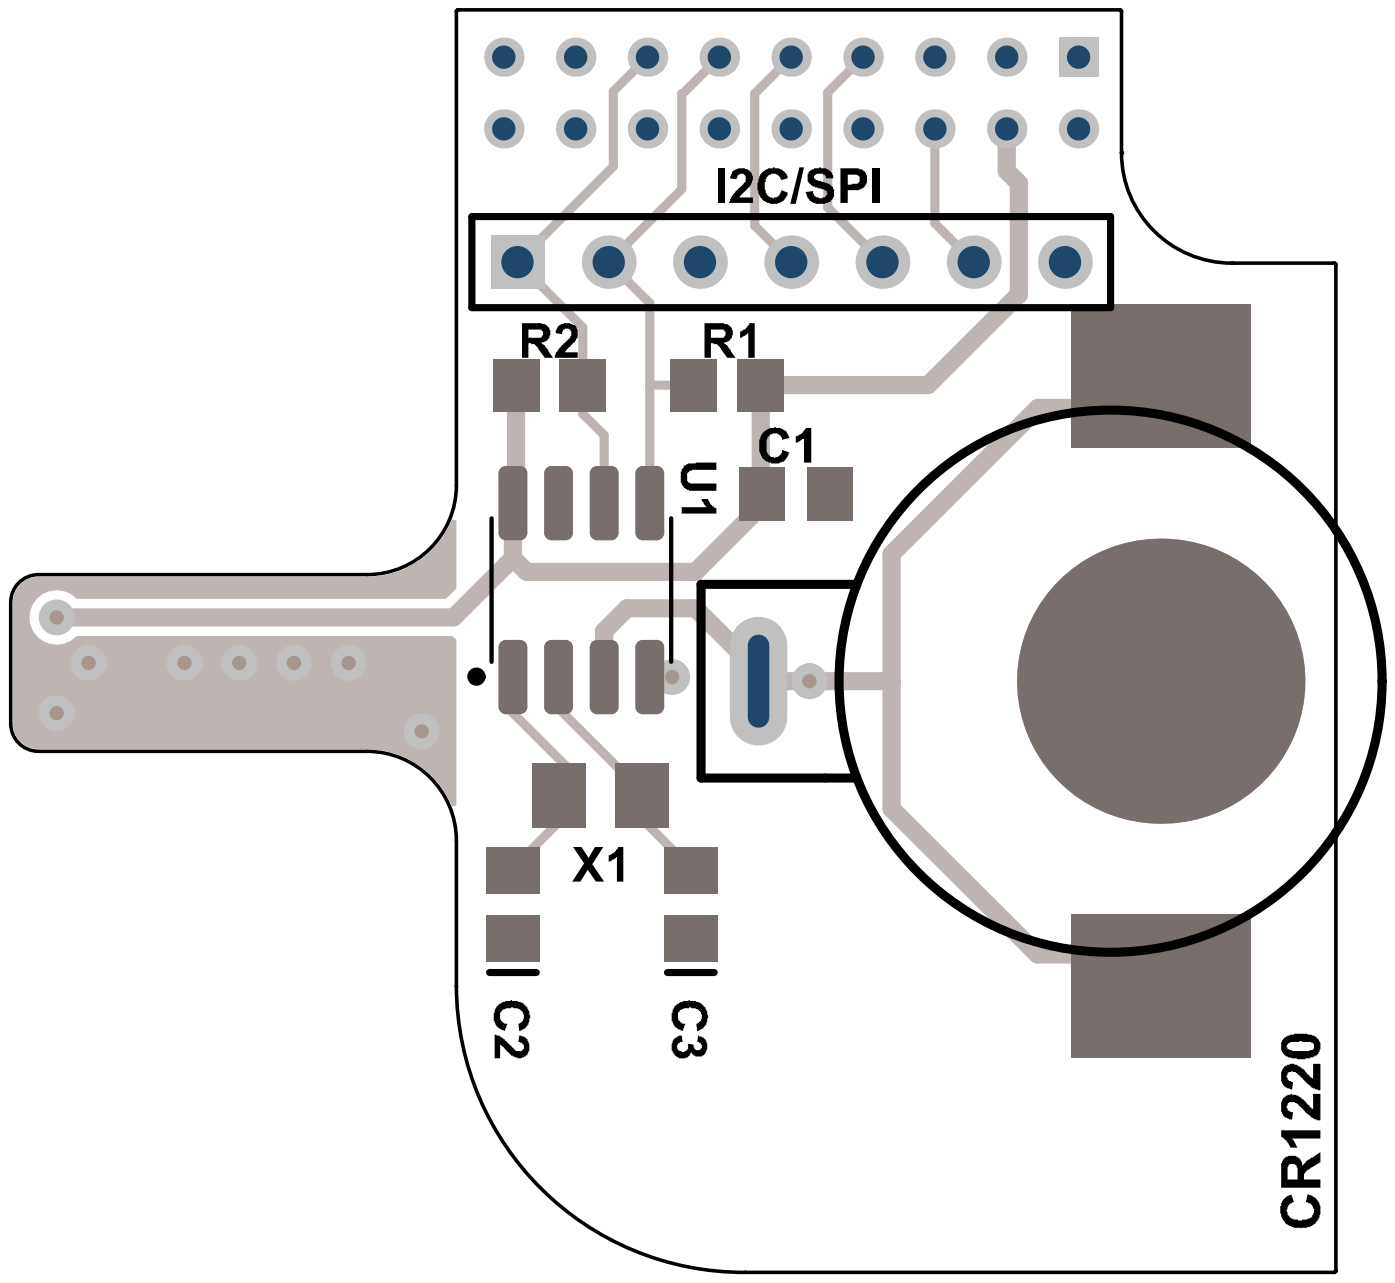
[picture p63: page 2]

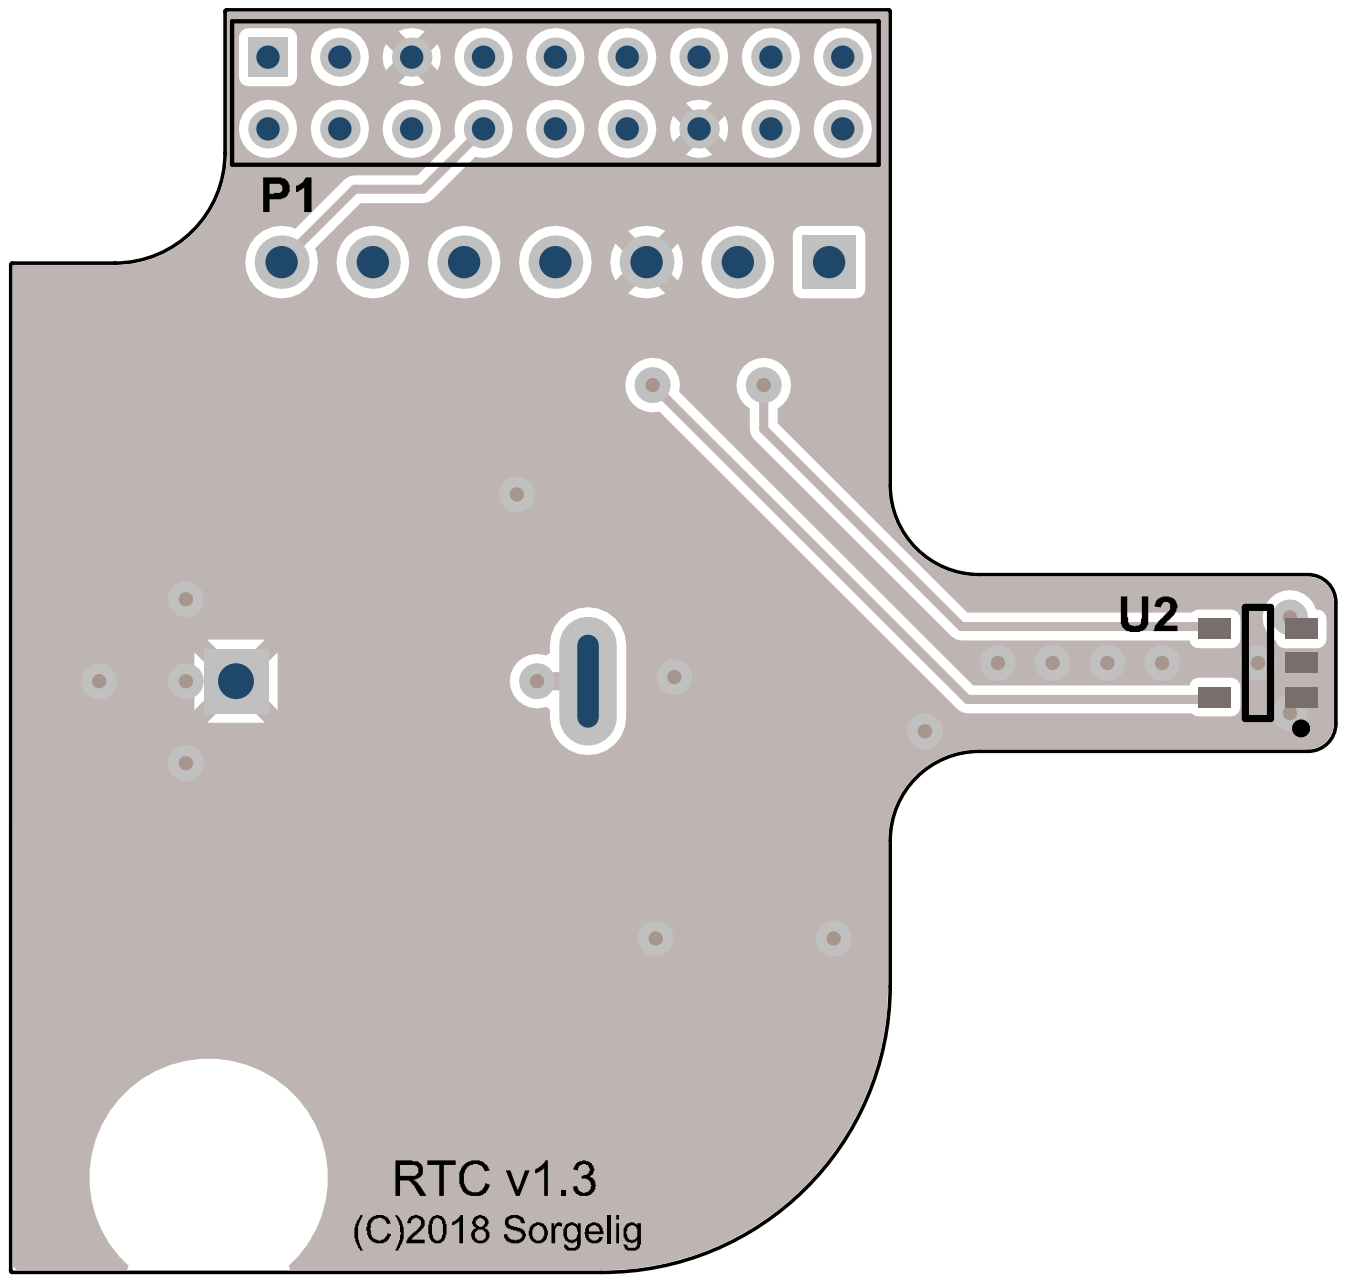
[picture p64: page 3]
