MiSTer-devel/Hardware_MiSTer/releases/PiTopAIO_1.1.pdf

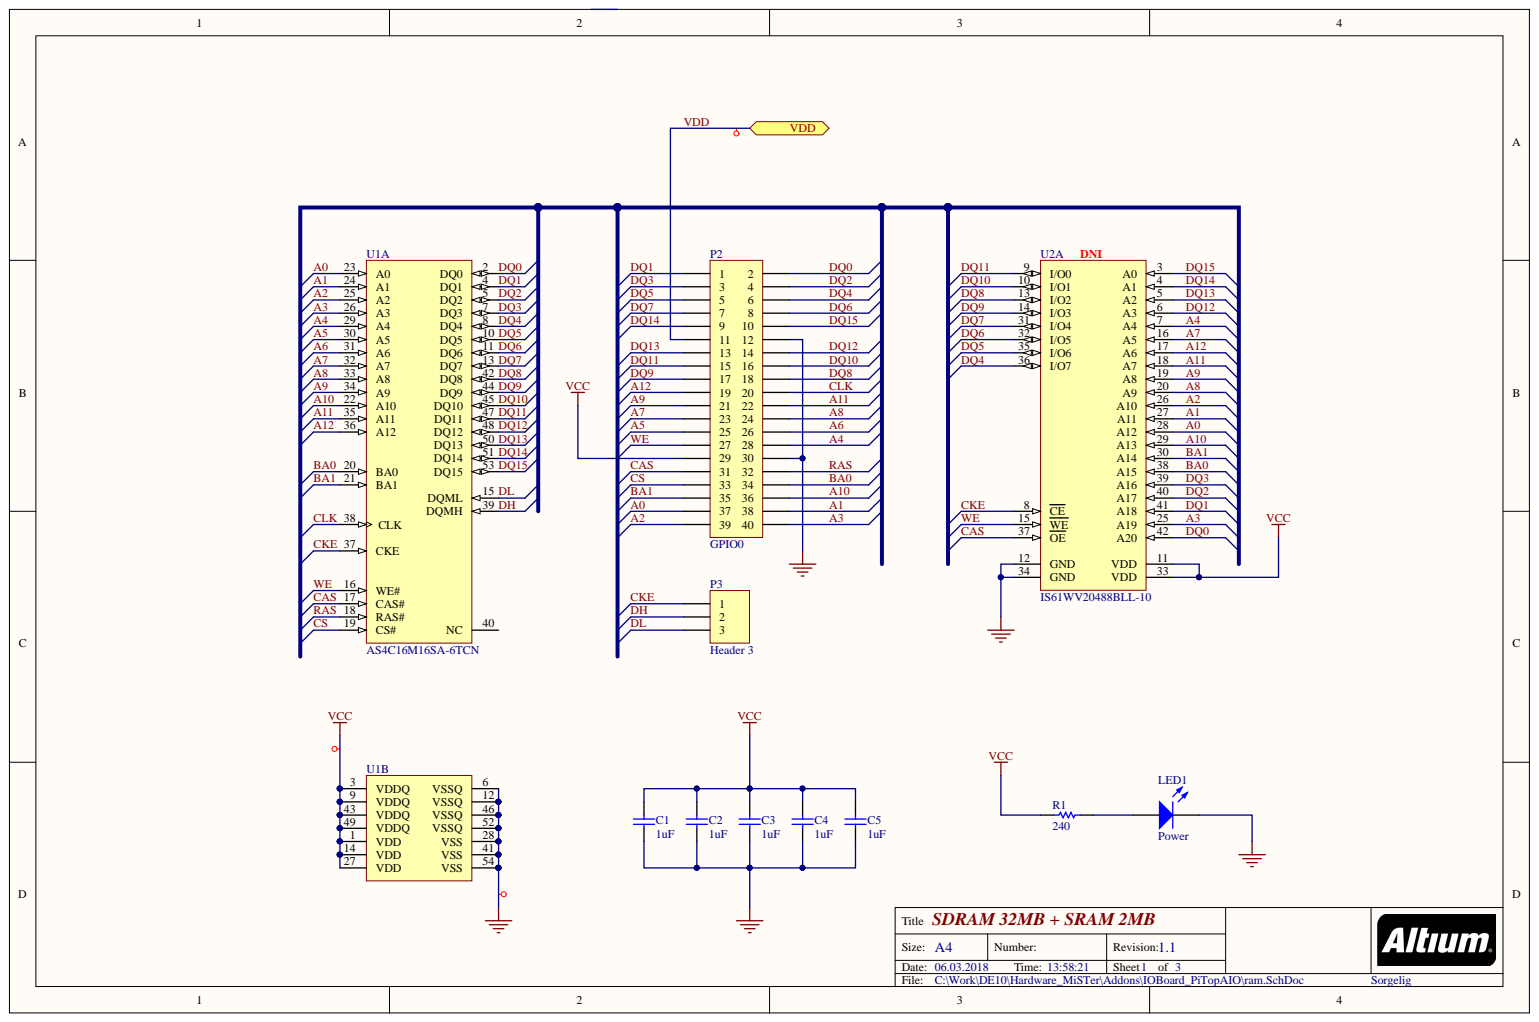
[picture p65: page 1]

SDRAM 32MB + SRAM 2MB Title

A4 Size: | Number: | 1.1 Revision:
Date: 06.03.2018 Time: 13:58:21 | | Sheet 1 of 3

C:\Work\DE10\Hardware_MiSTer\Addons\IOBoard_PiTopAIO\ram.SchDoc

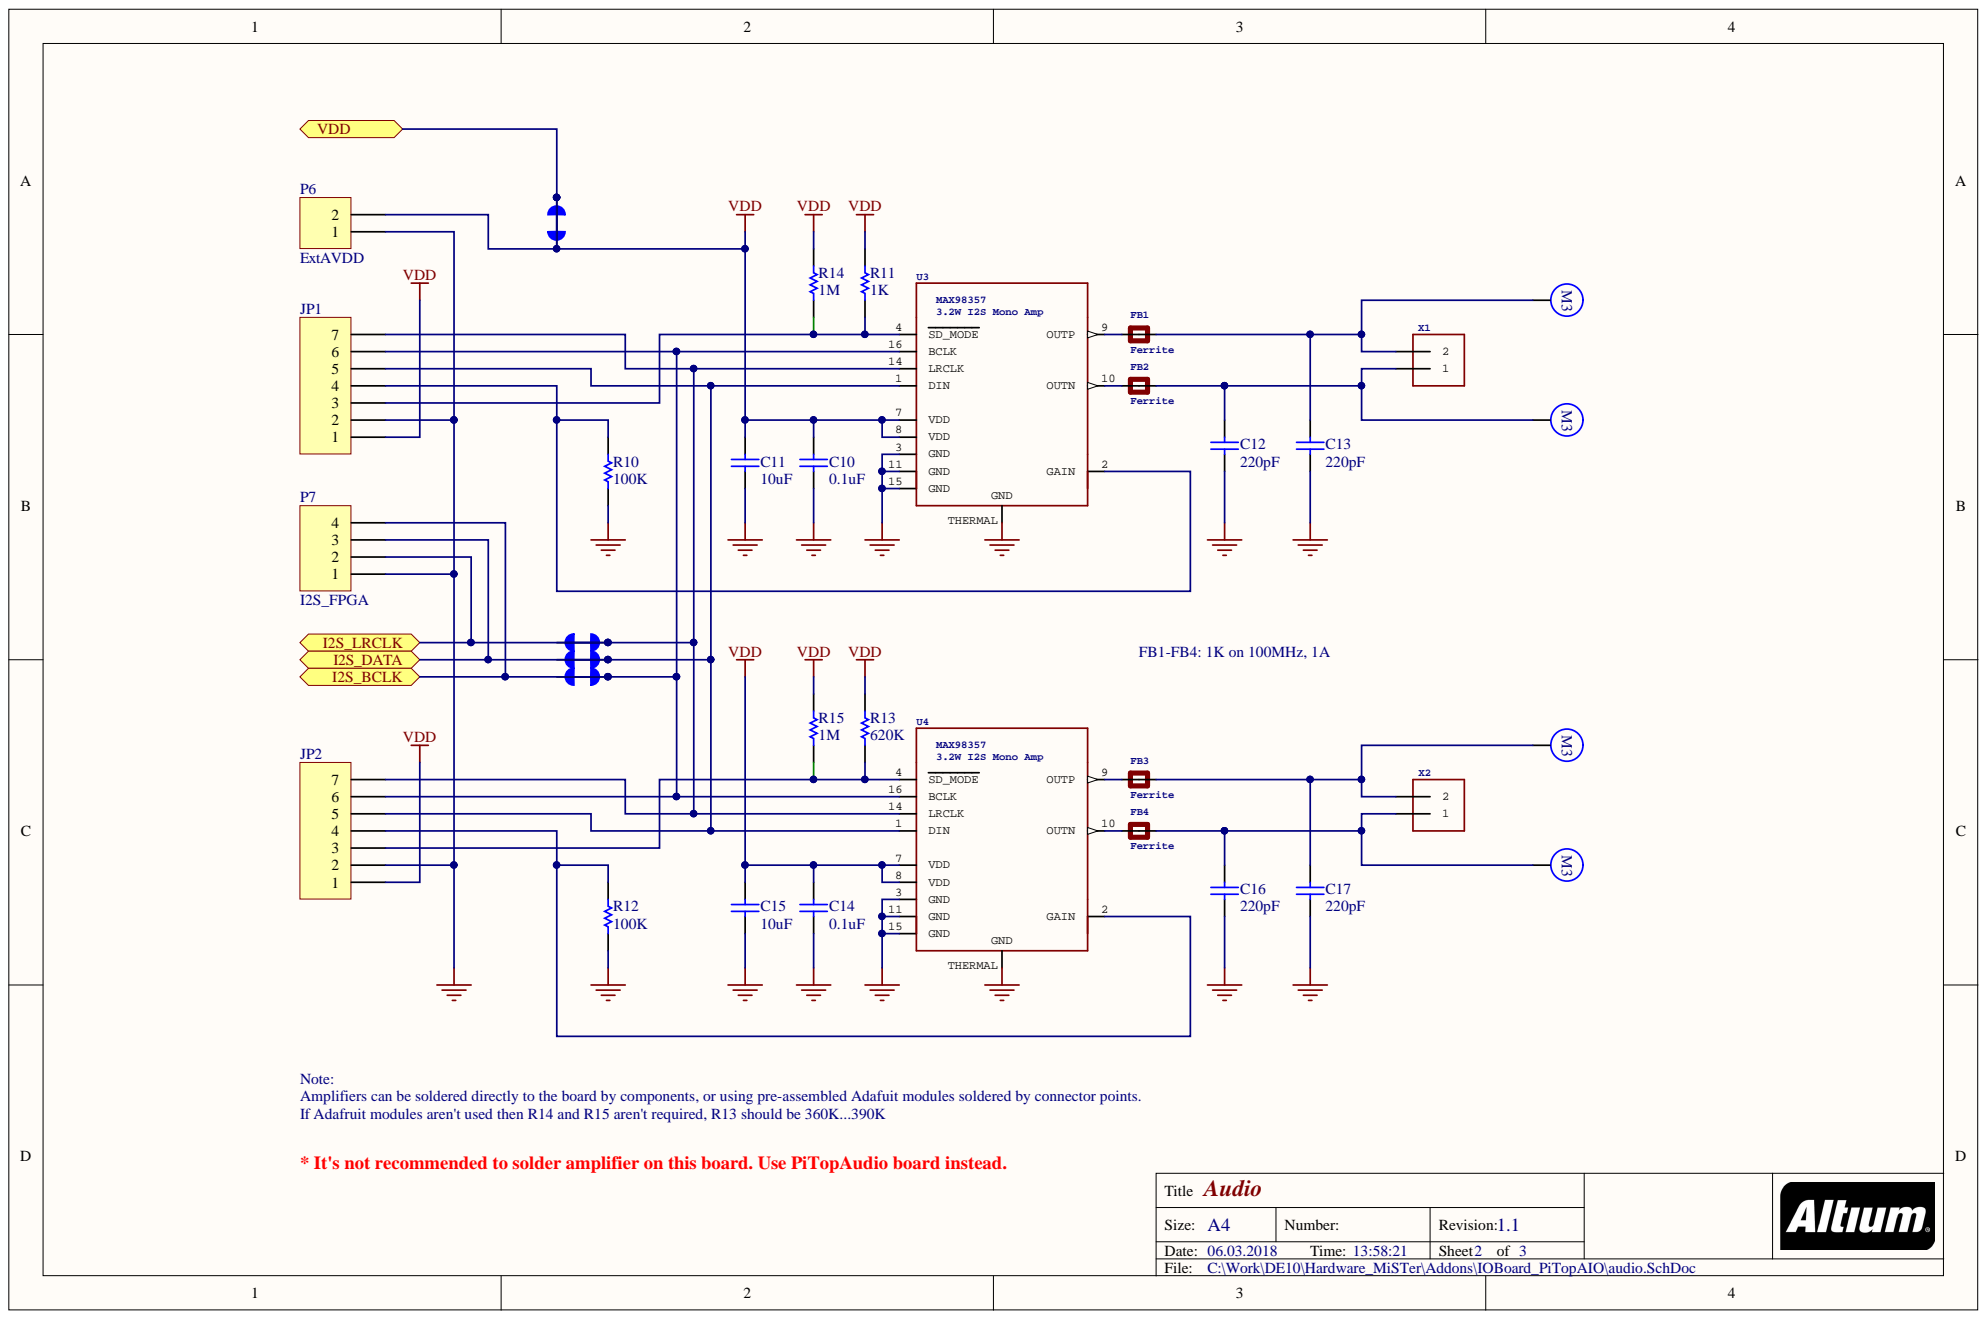
[picture p66: page 2]

BCLK 16 | Ferrite | 12
LRCLK 14

GND 11
GND 15

Note:
Amplifiers can be soldered directly to the board by components, or using pre-assembled Adafuit modules soldered by connector points.
If Adafruit modules aren't used then R14 and R15 aren't required, R13 should be 360K...390K

* It's not recommended to solder amplifier on this board. Use PiTopAudio board instead.

Audio Title

A4 Size: | Number: | 1.1 Revision:

C:\Work\DE10\Hardware_MiSTer\Addons\IOBoard_PiTopAIO\audio.SchDoc

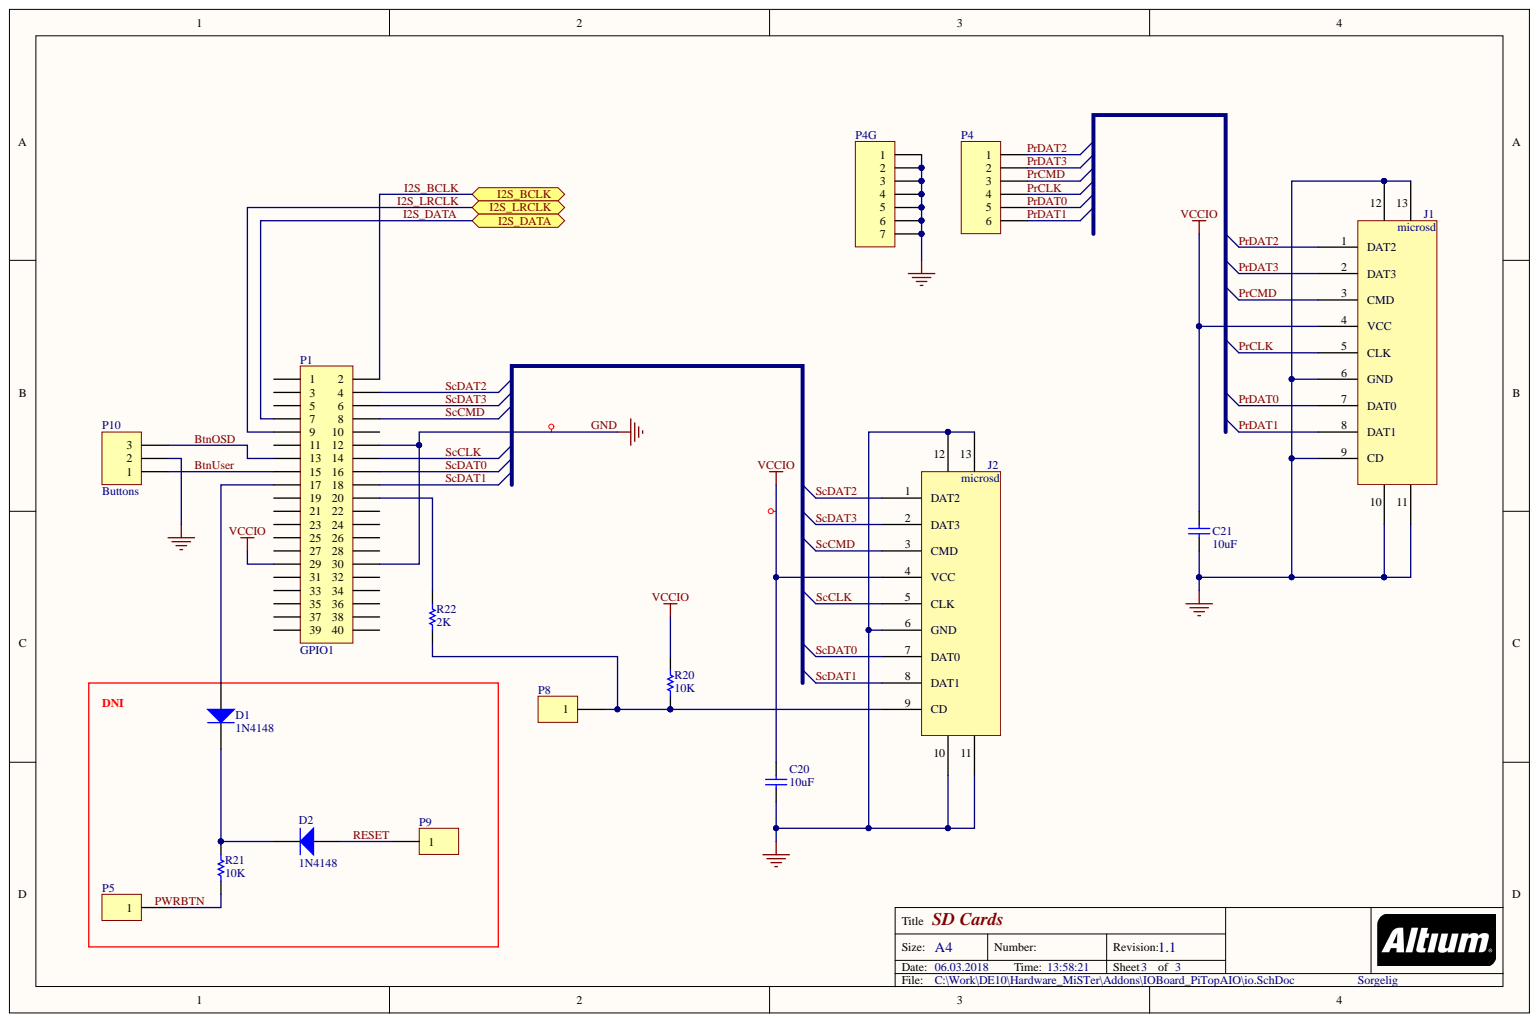
[picture p67: page 3]

VCCIO

7 8 9 | DAT0 DAT1 CD

SD Cards Title

A4 Size: | Number: | 1.1 Revision:

C:\Work\DE10\Hardware_MiSTer\Addons\IOBoard_PiTopAIO\io.SchDoc

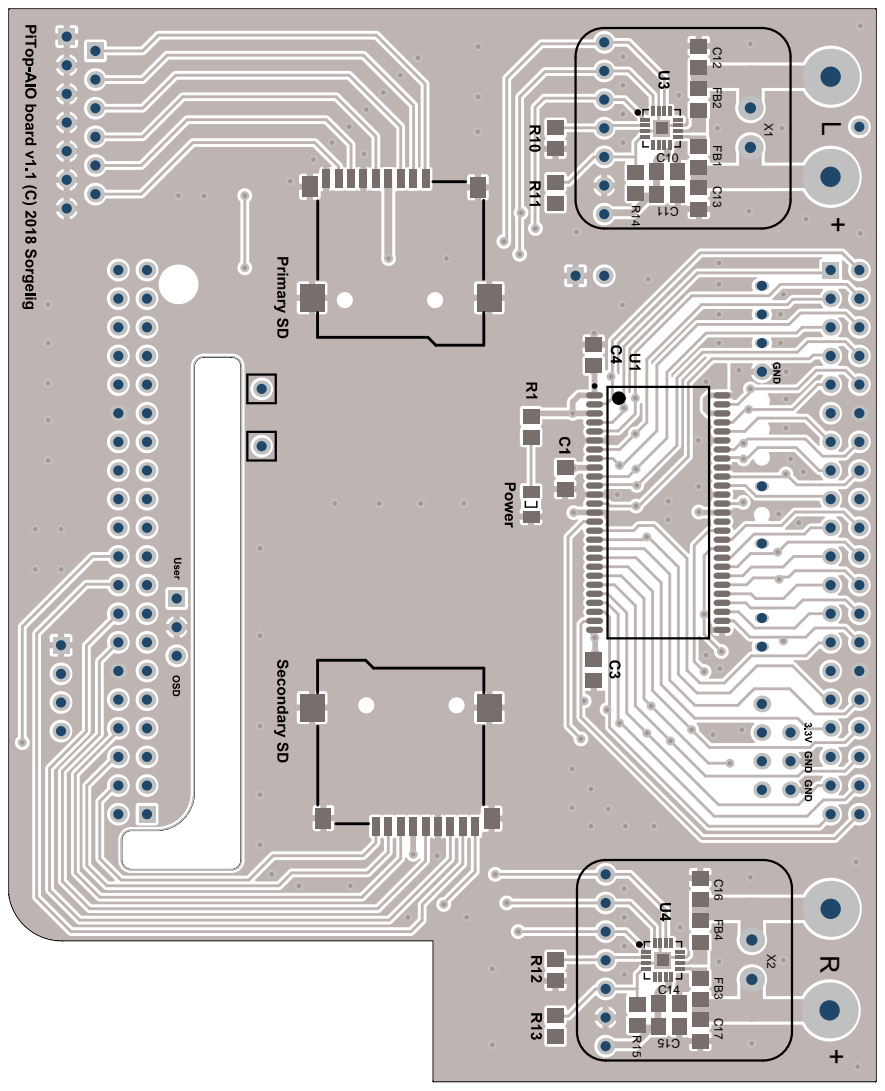
[picture p68: page 4]

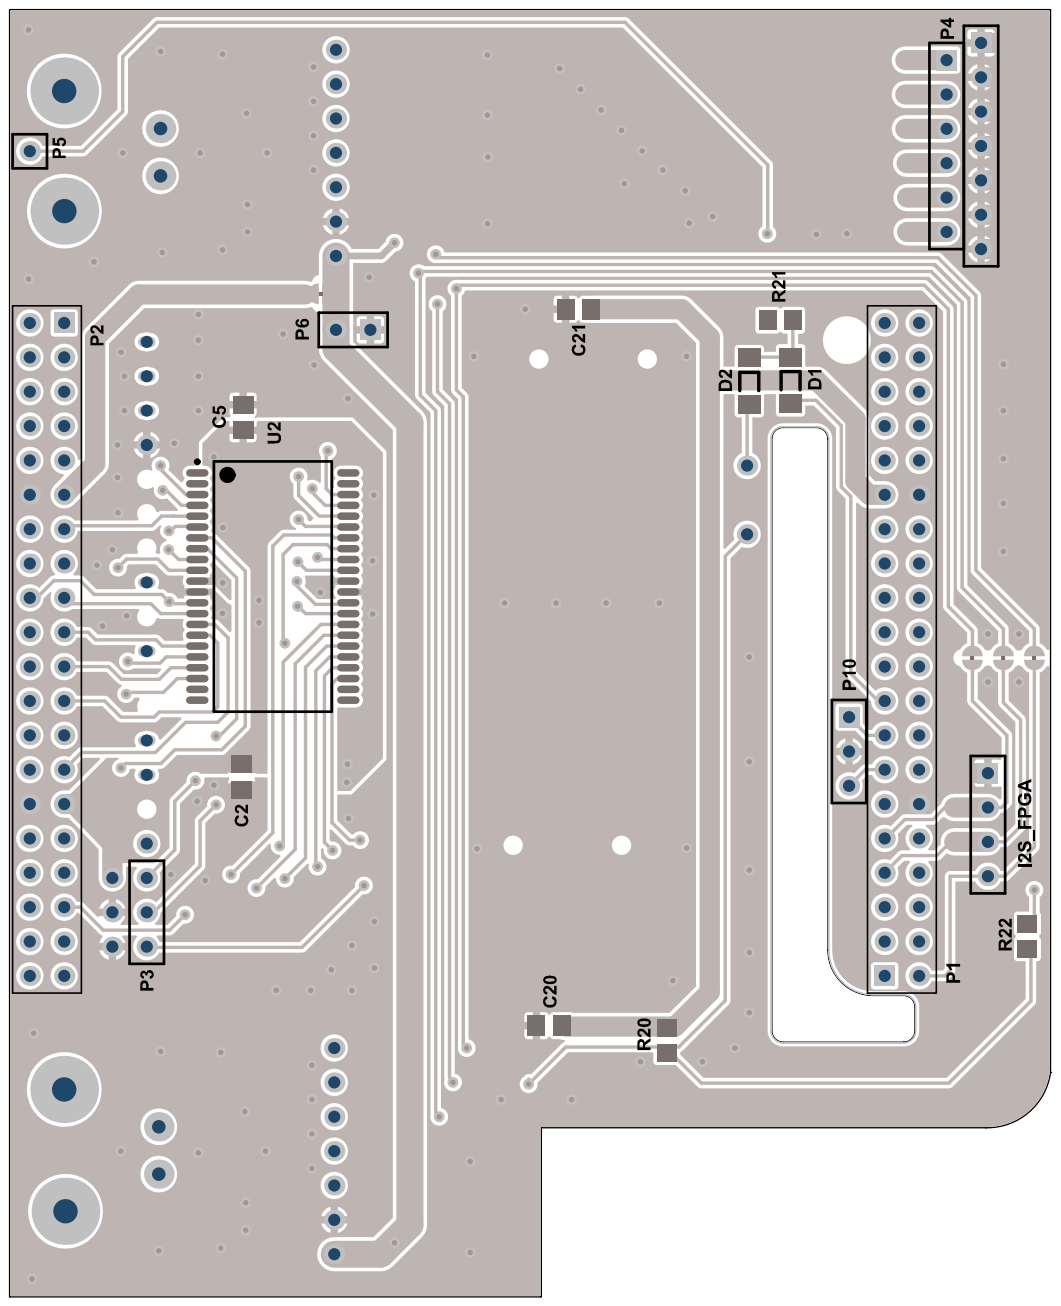
[picture p69: page 5]
