MiSTer-devel/Hardware_MiSTer/releases/PiTopAudio_1.1.pdf

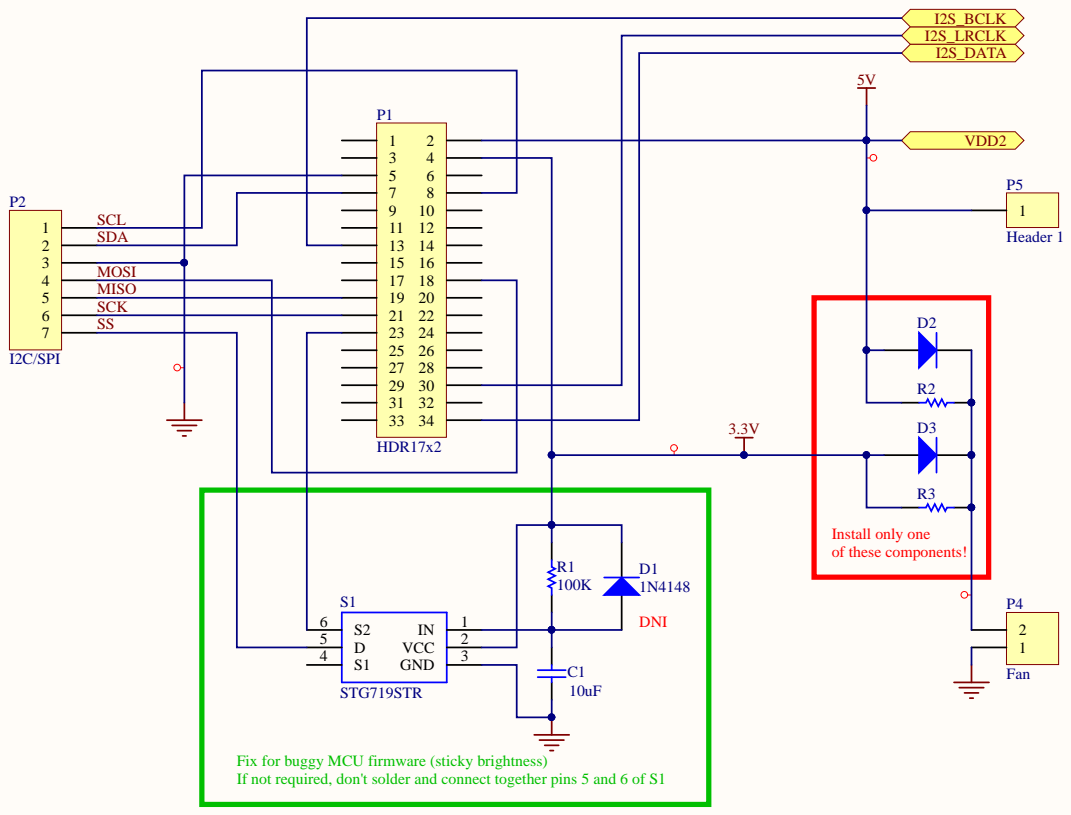
[picture p70: page 1]

SDA

MISO
SCK
SS

Fix for buggy MCU firmware (sticky brightness)
If not required, don't solder and connect together pins 5 and 6 of S1

I2C/SPI connections Title

A4 Size: | Number: | 1.1 Revision:
Date: 06.03.2018 Time: 13:57:42 | | Sheet 1 of 2

C:\Work\DE10\Hardware_MiSTer\Addons\PiTopAudio\serial.SchDoc

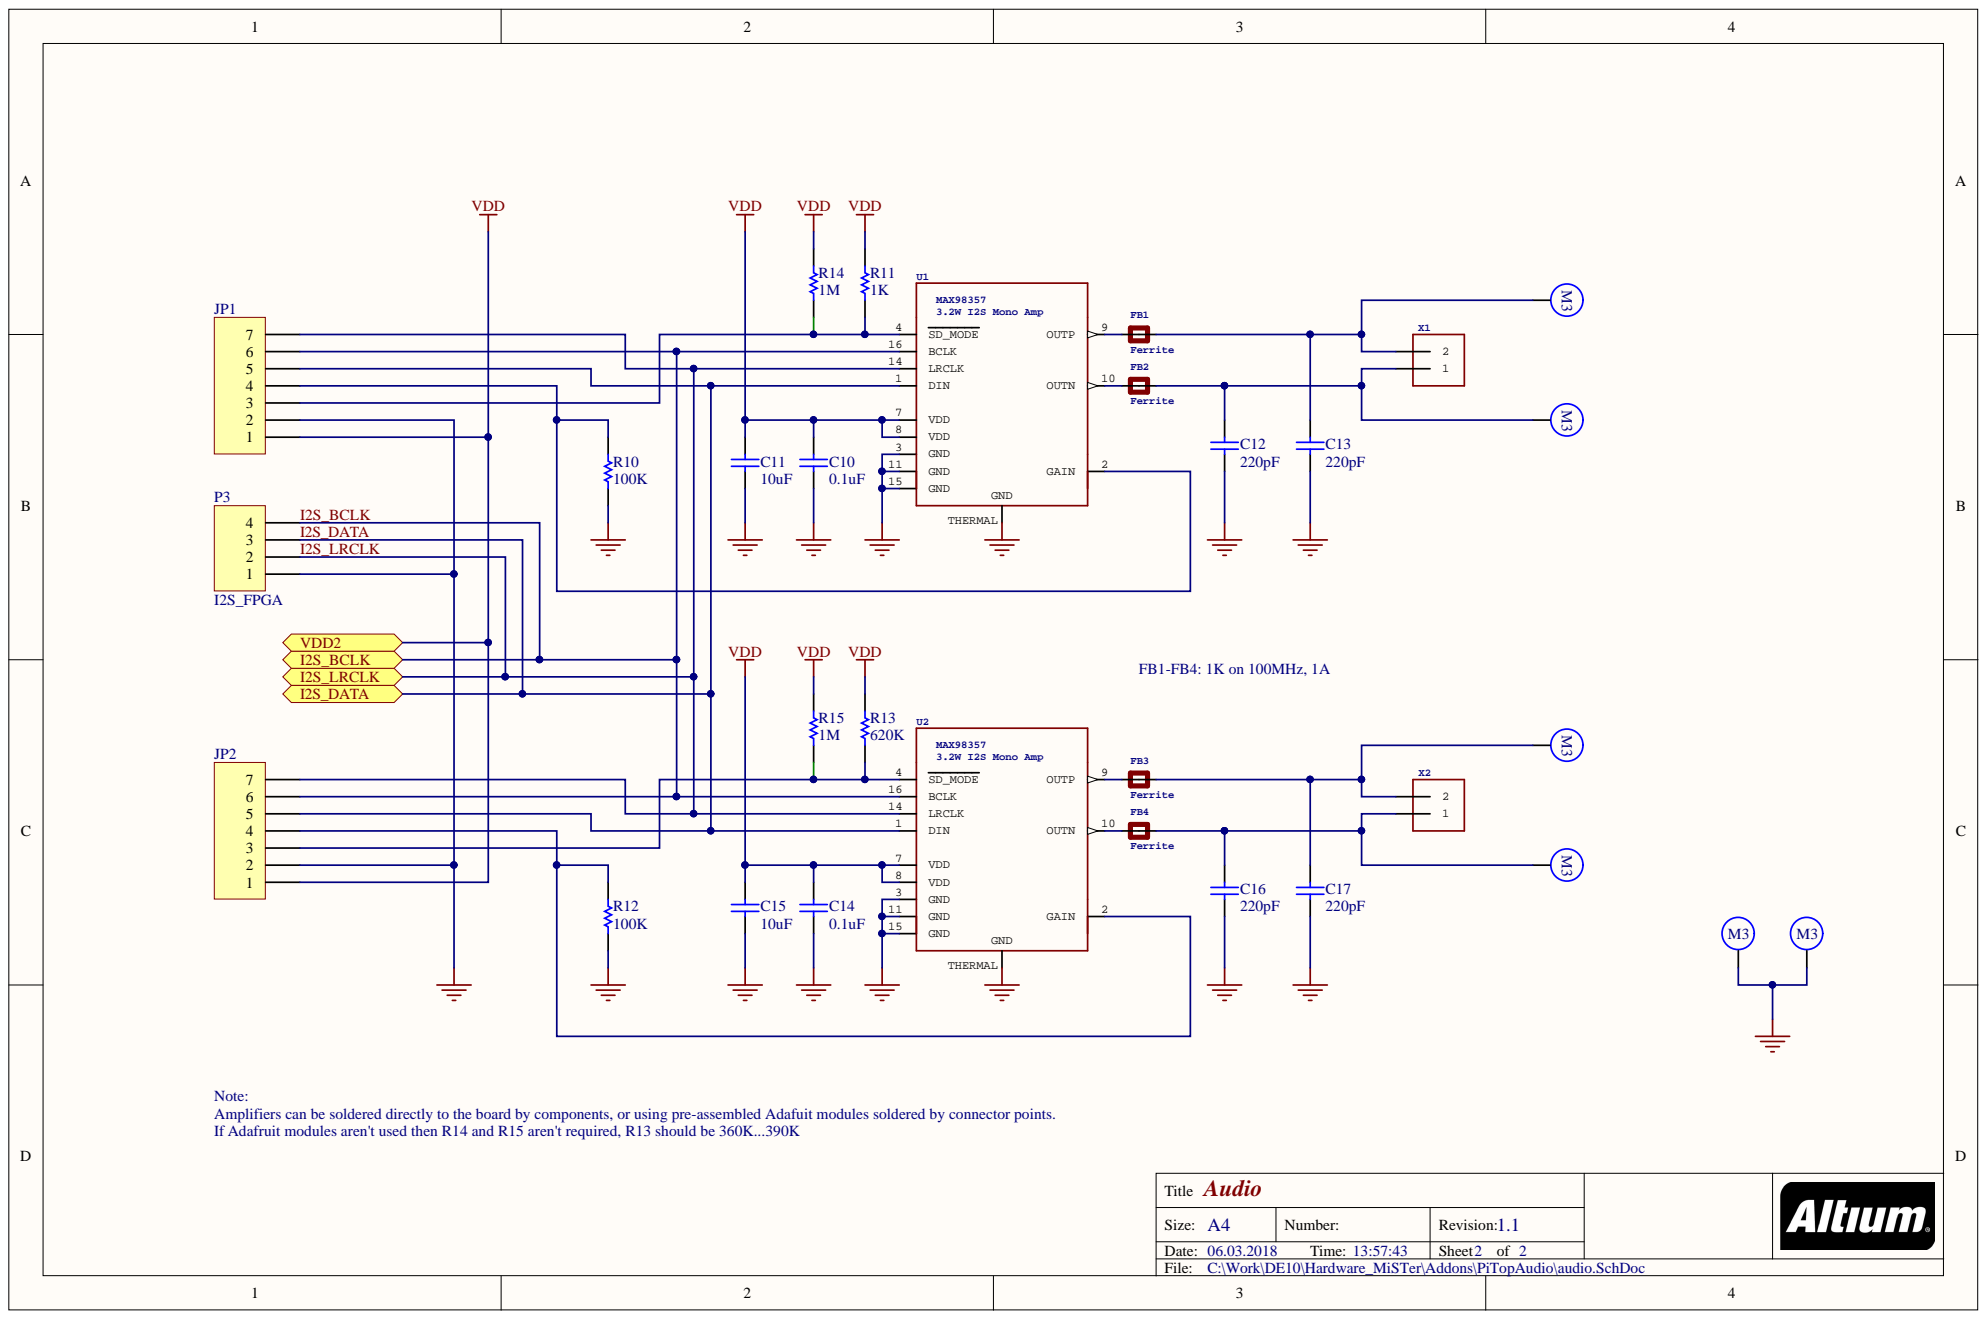
[picture p71: page 2]

BCLK 16 | Ferrite | 12
LRCLK 14

I2S_DA TA
I2S_LRCLK

GND 11
GND 15

Note:
Amplifiers can be soldered directly to the board by components, or using pre-assembled Adafuit modules soldered by connector points.
If Adafruit modules aren't used then R14 and R15 aren't required, R13 should be 360K...390K

Audio Title

A4 Size: | Number: | 1.1 Revision:
Date: 06.03.2018 Time: 13:57:43 | | Sheet 2 of 2

C:\Work\DE10\Hardware_MiSTer\Addons\PiTopAudio\audio.SchDoc

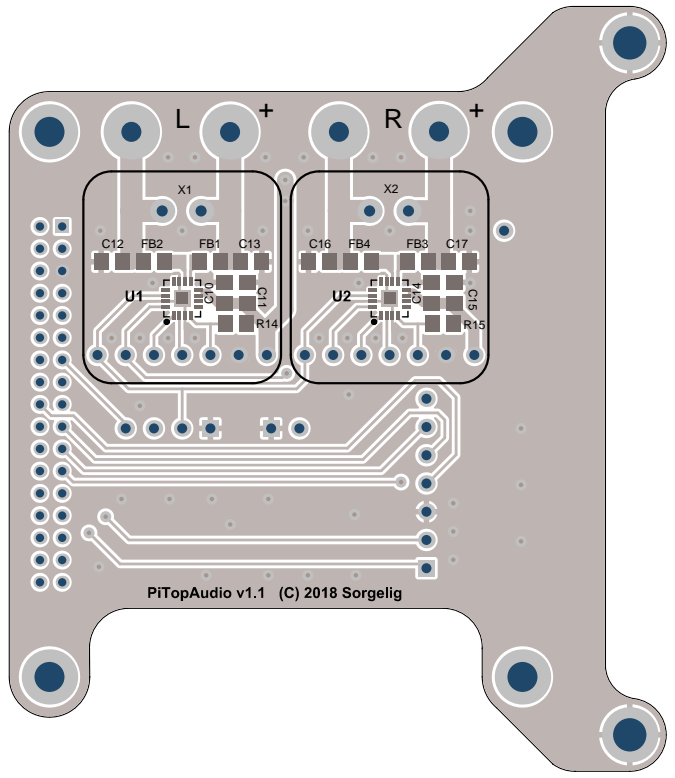
[picture p72: page 3]

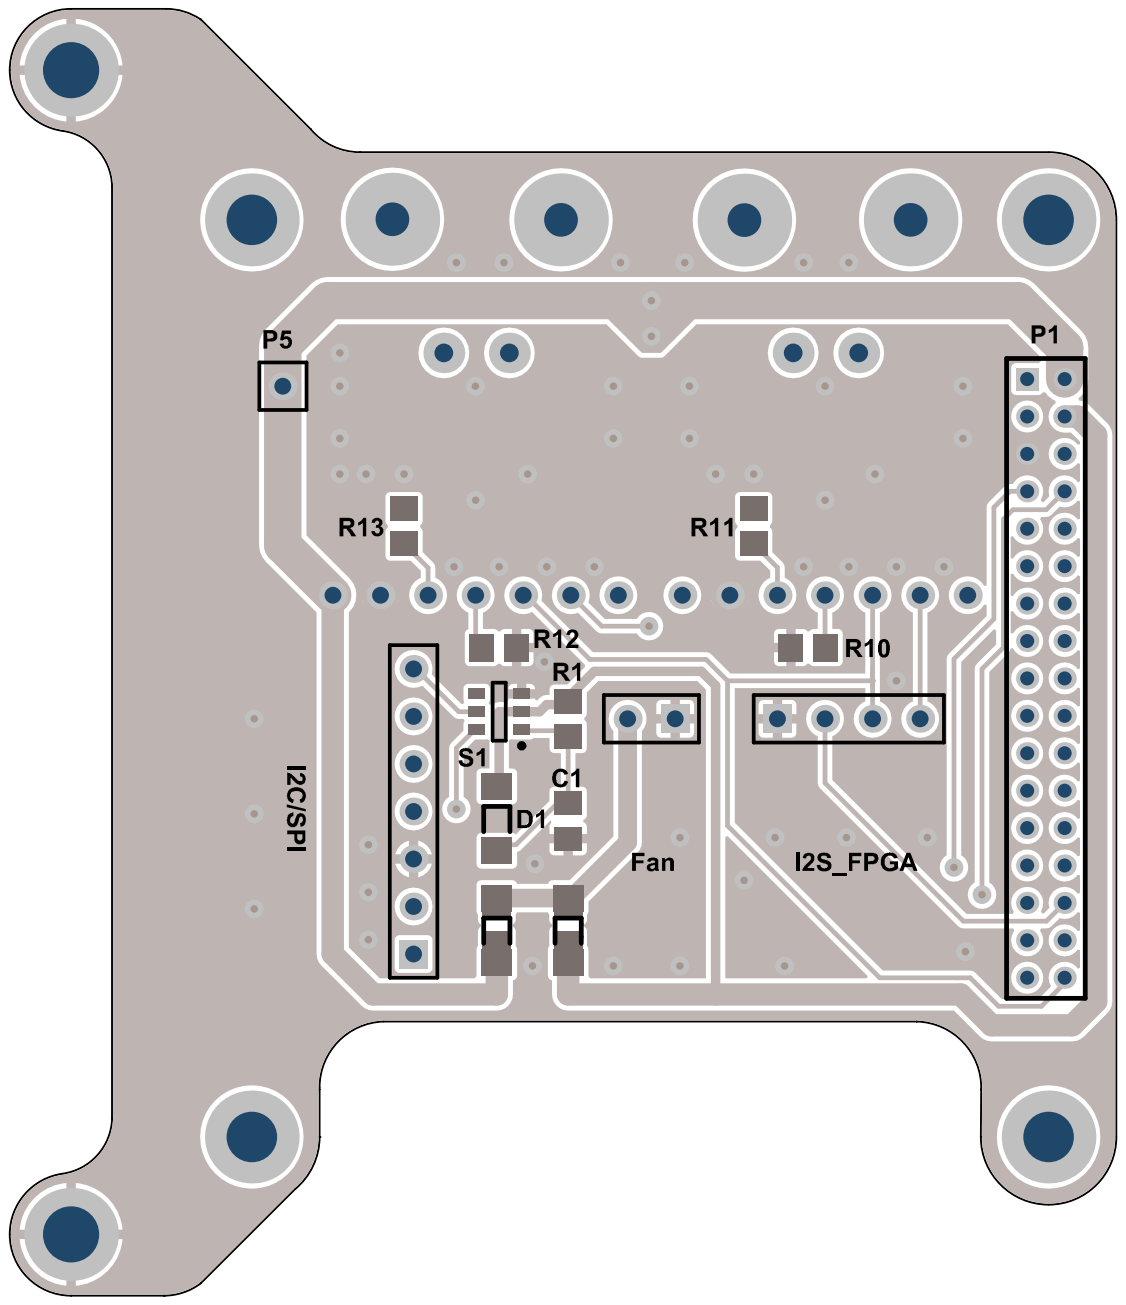
[picture p73: page 4]
