MiSTer-devel/Hardware_MiSTer/releases/iobrd_5.2.pdf

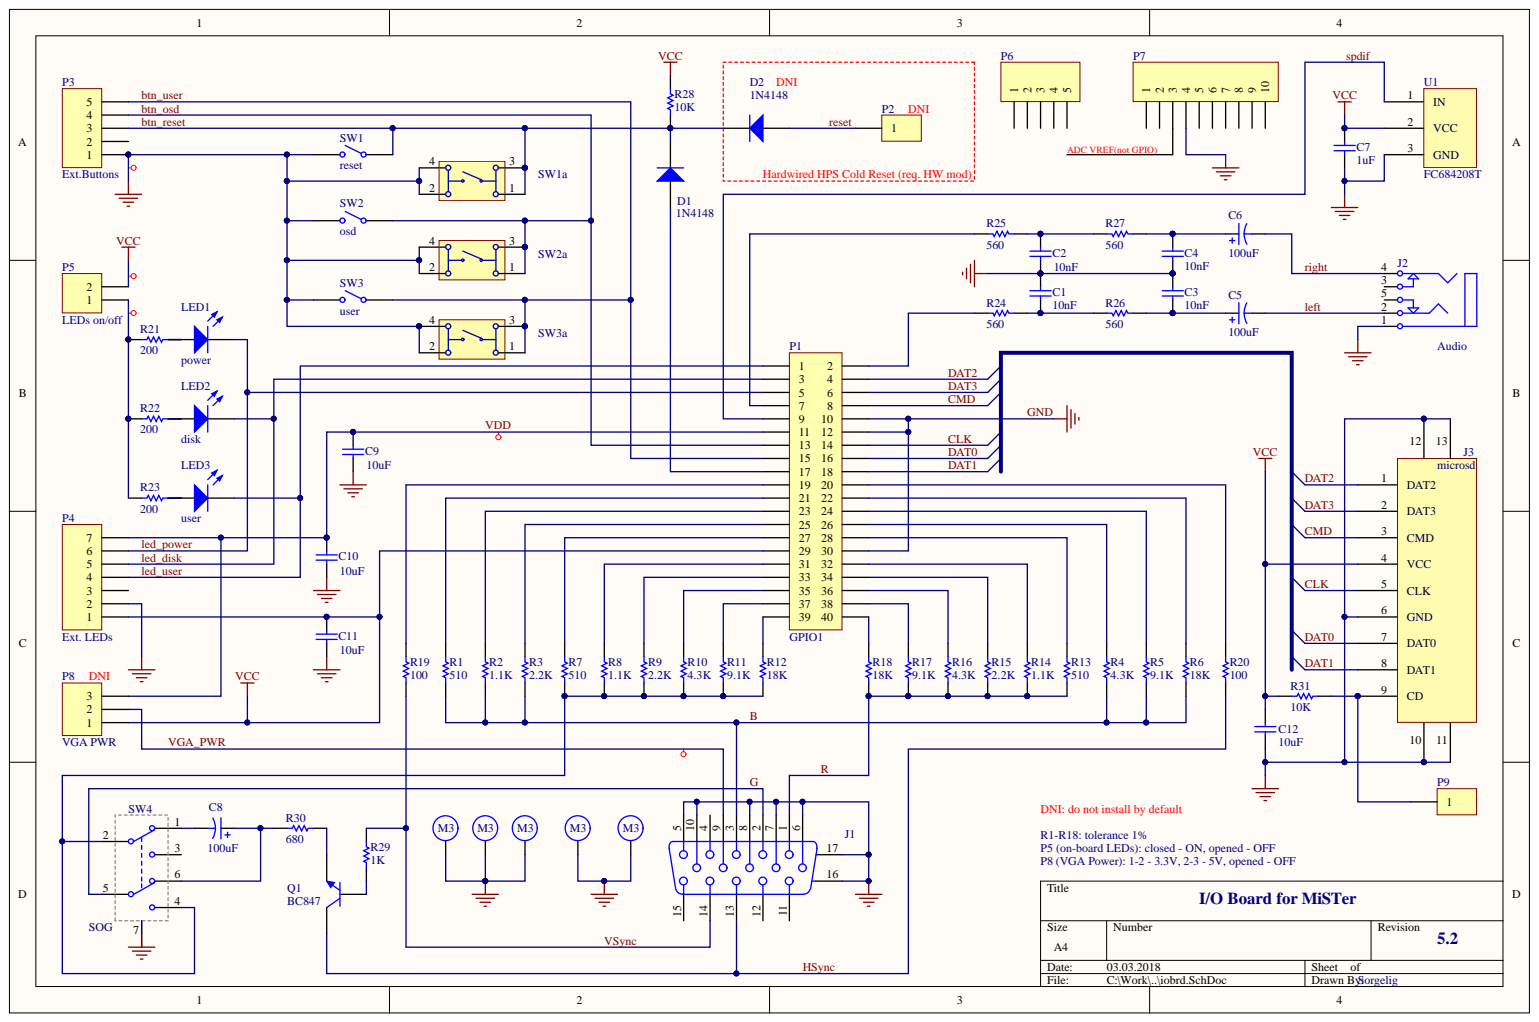
[picture p74: page 1]

ADC VREF(not GPIO)

Hardwired HPS Cold Reset (req. HW mod)

LED2 | | DAT3

VDD | CMD

DNI: do not install by default

R1-R18: tolerance 1%
P5 (on-board LEDs): closed - ON, opened - OFF
P8 (VGA Power): 1-2 - 3.3V, 2-3 - 5V, opened - OFF

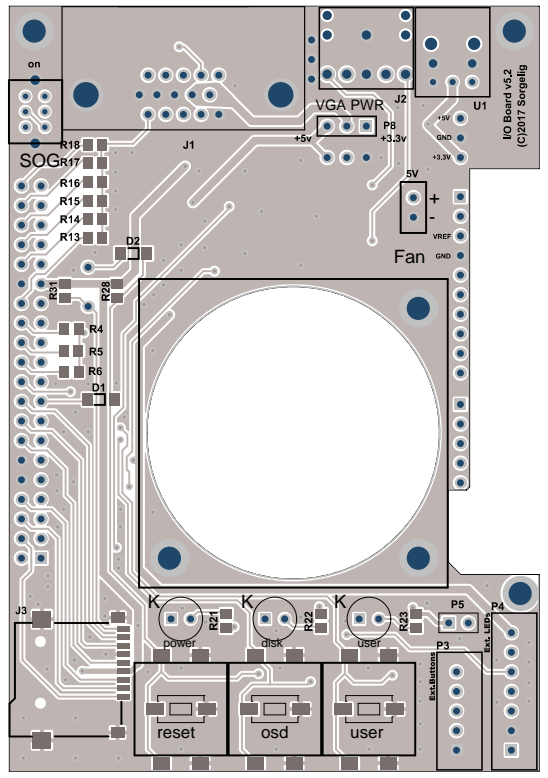
[picture p75: page 2]

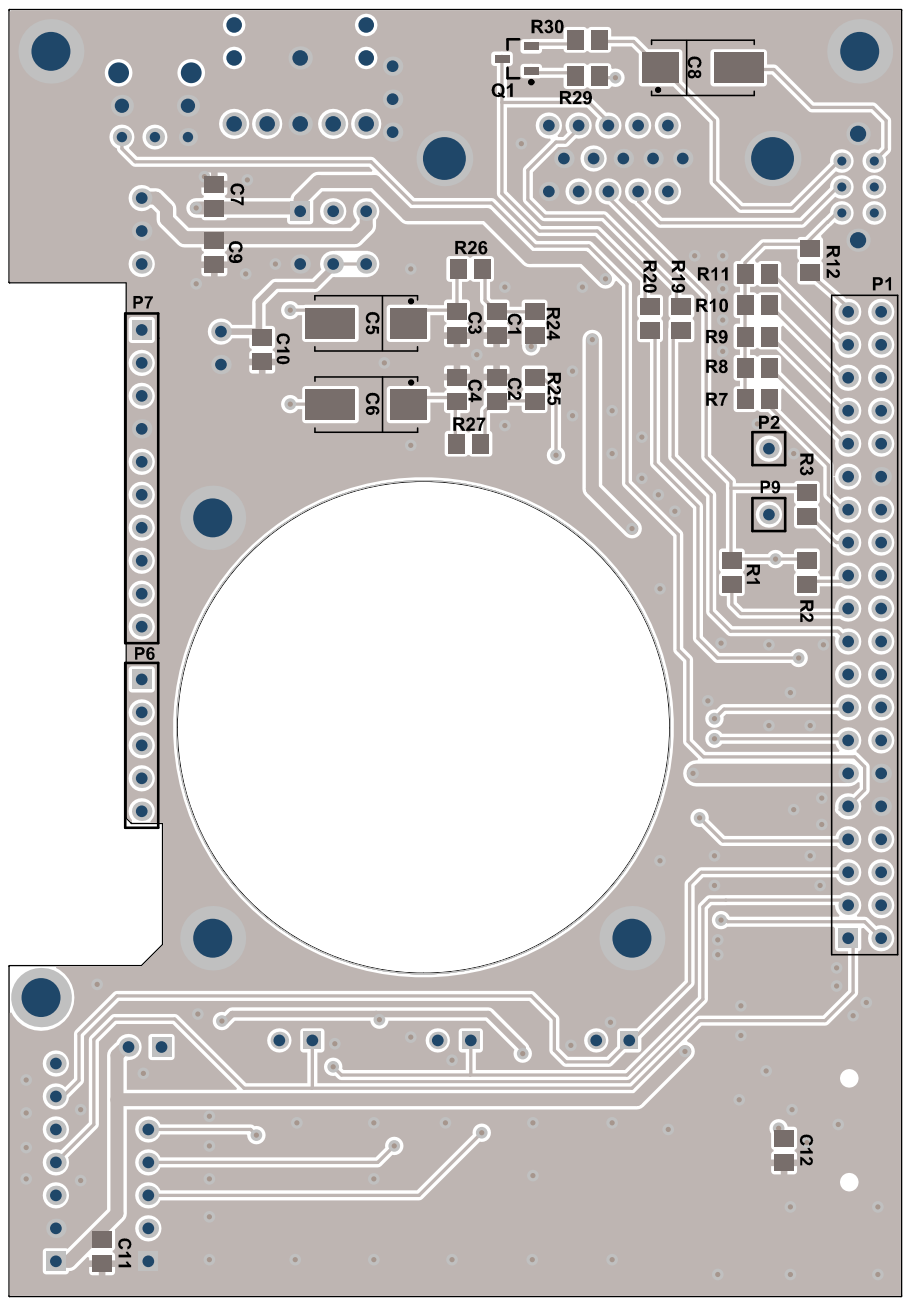
[picture p76: page 3]
