MiSTer-devel/Hardware_MiSTer/releases/PiTopConn_1.0.pdf

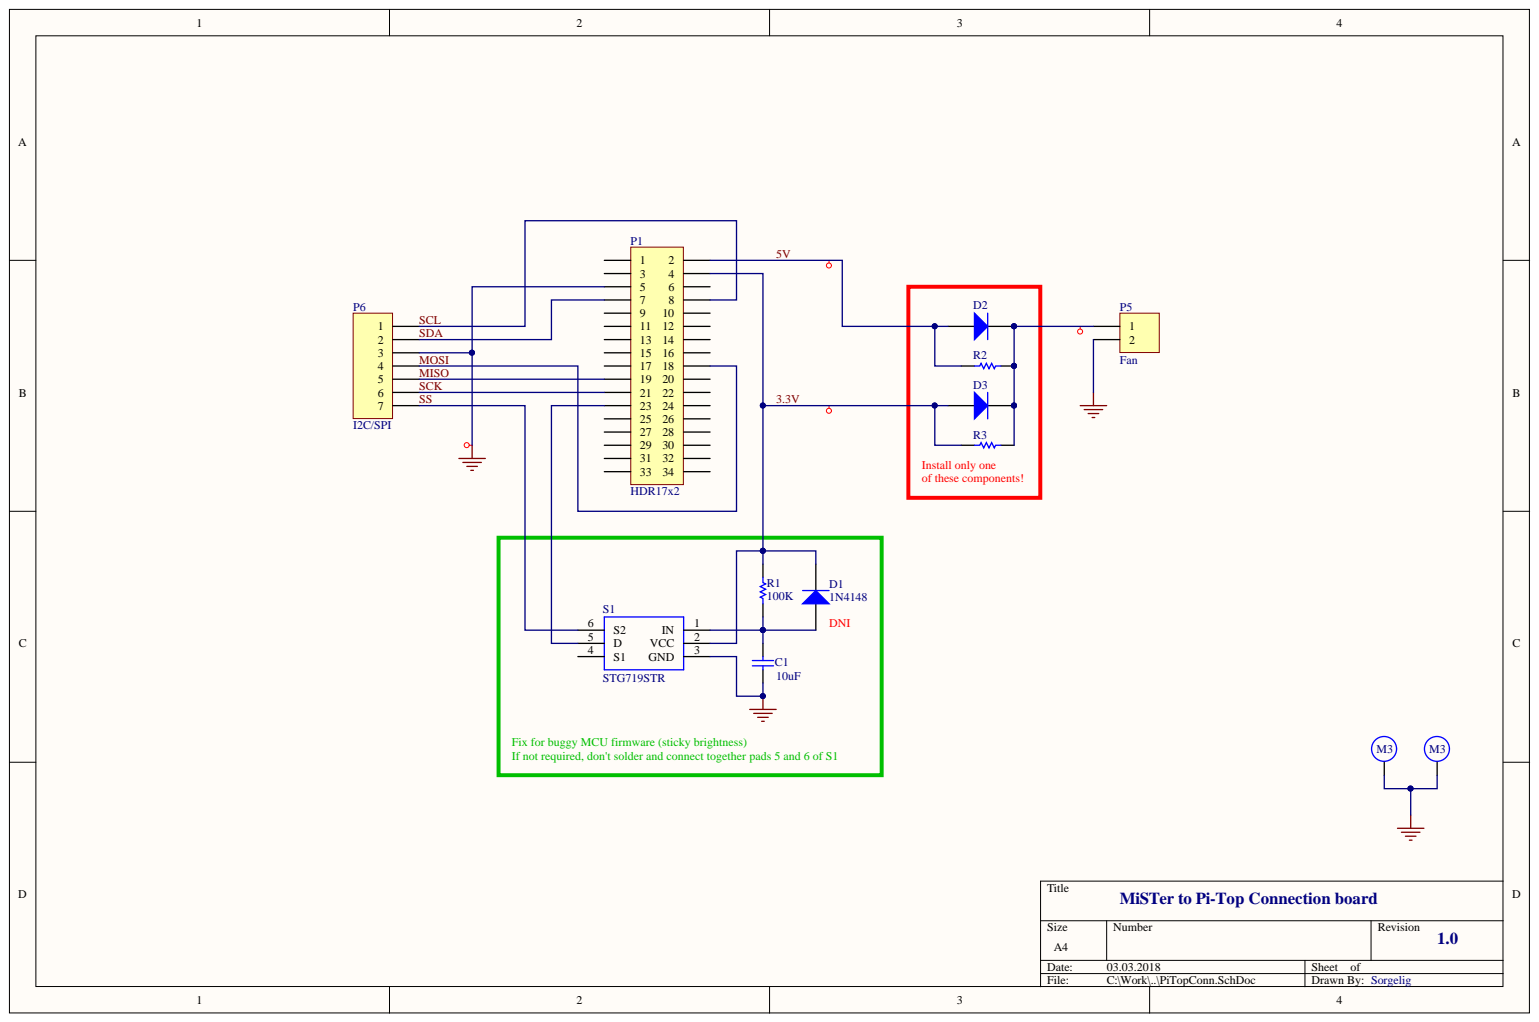
[picture p77: page 1]

SCL
SDA

MISO
SCK
SS

Fix for buggy MCU firmware (sticky brightness)

MiSTer to Pi-Top Connection board

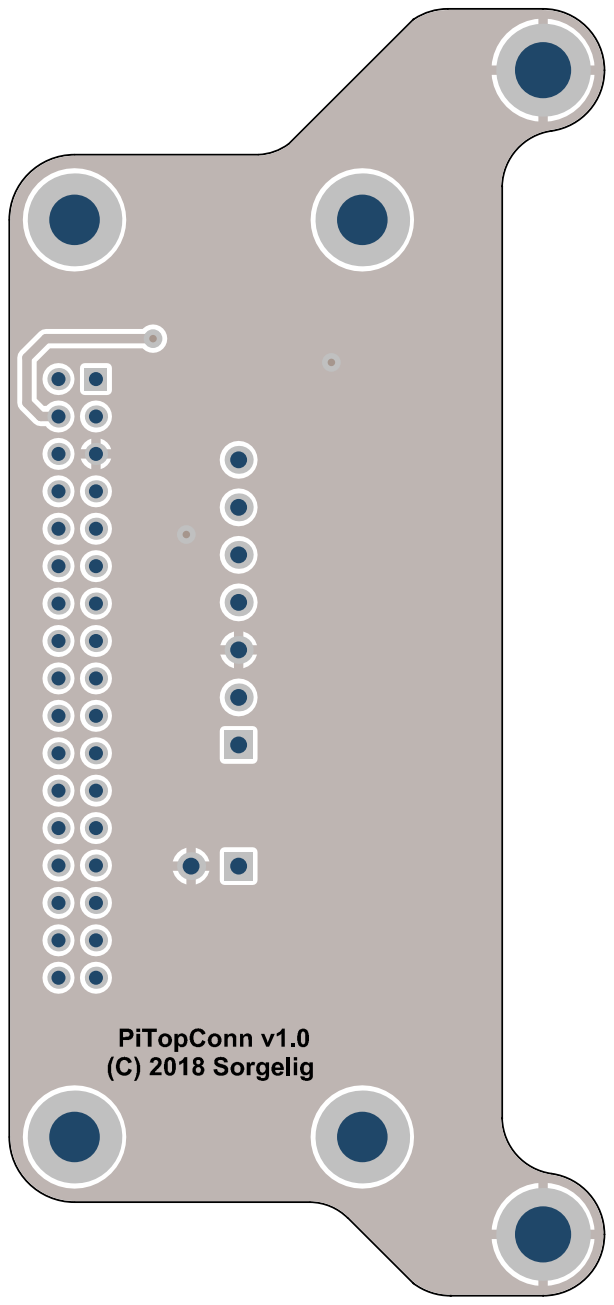
[picture p78: page 2]

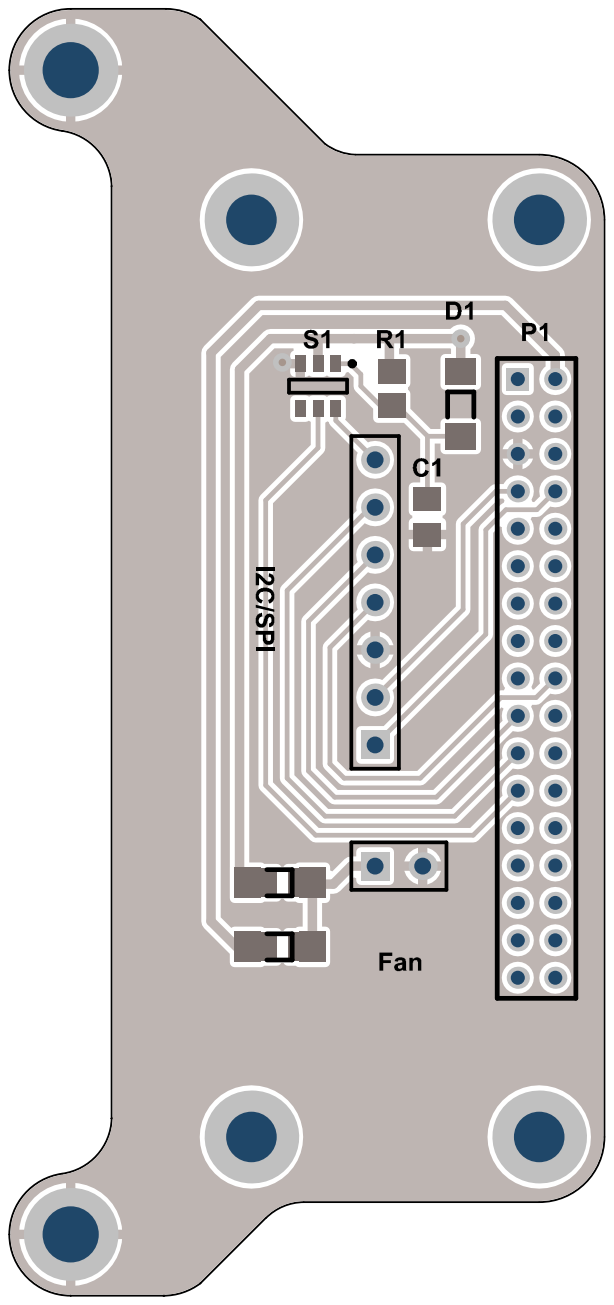
[picture p79: page 3]
