MiSTer-devel/Hardware_MiSTer/releases/iobrd_3.1.pdf

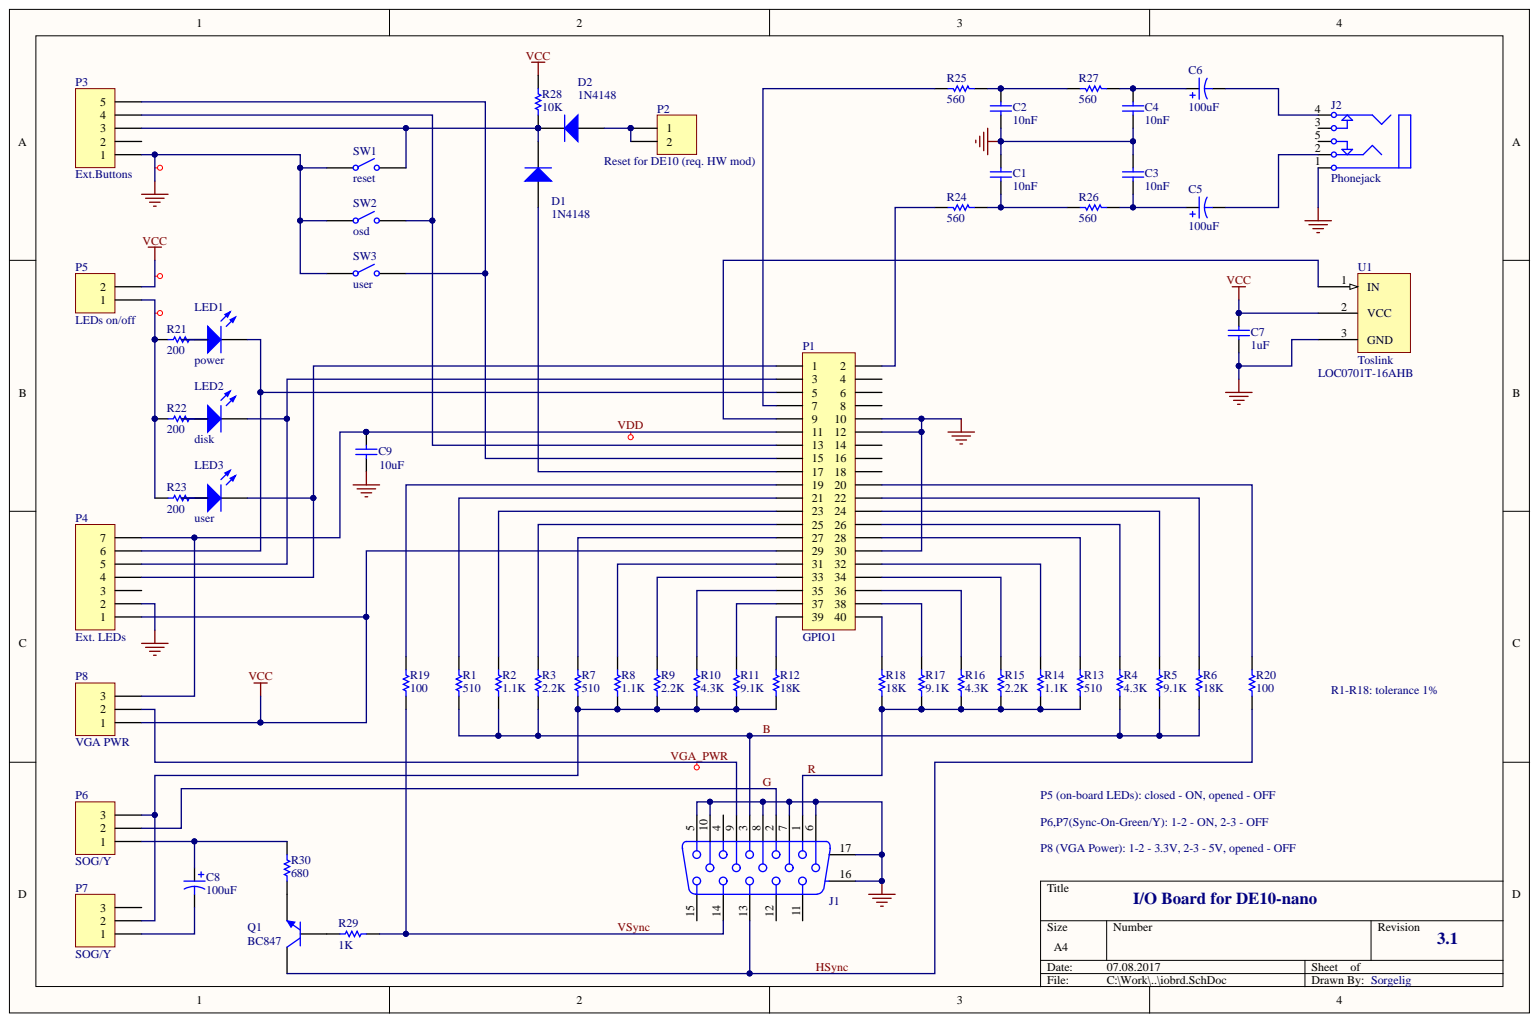
[picture p80: page 1]

LED2 disk

9 10
11 12 13 14 15 16 17 18 19 20 21 22 23 24 25 26 27 28 29 30 31 32 33 34 35 36 37 38 39 40

user

P5 (on-board LEDs): closed - ON, opened - OFF

P6,P7(Sync-On-Green/Y): 1-2 - ON, 2-3 - OFF

P8 (VGA Power): 1-2 - 3.3V, 2-3 - 5V, opened - OFF

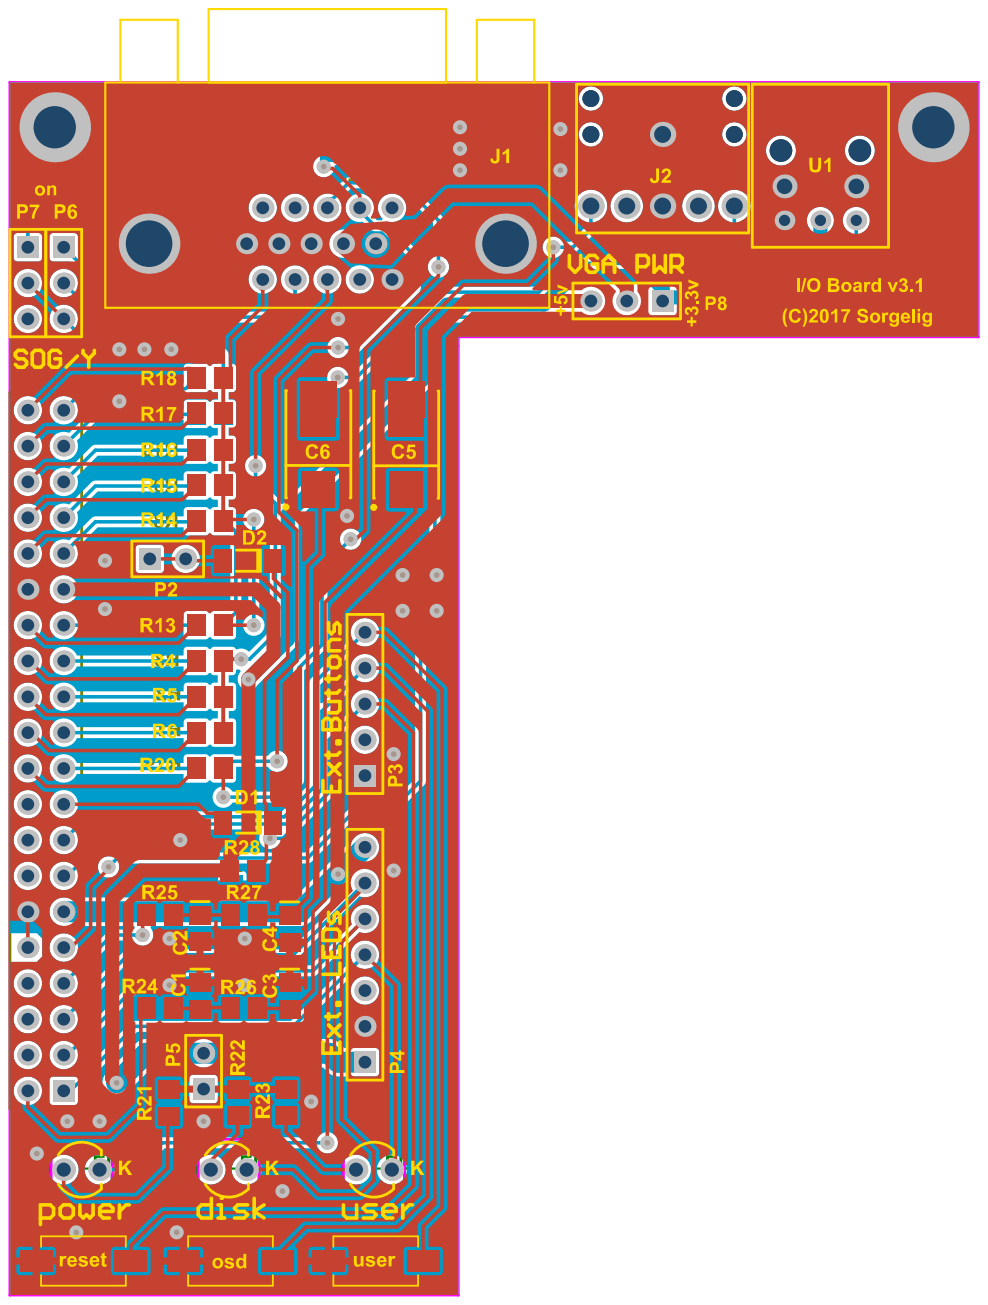
[picture p81: page 2]
