MiSTer-devel/Hardware_MiSTer/releases/USBHub_1.2.pdf

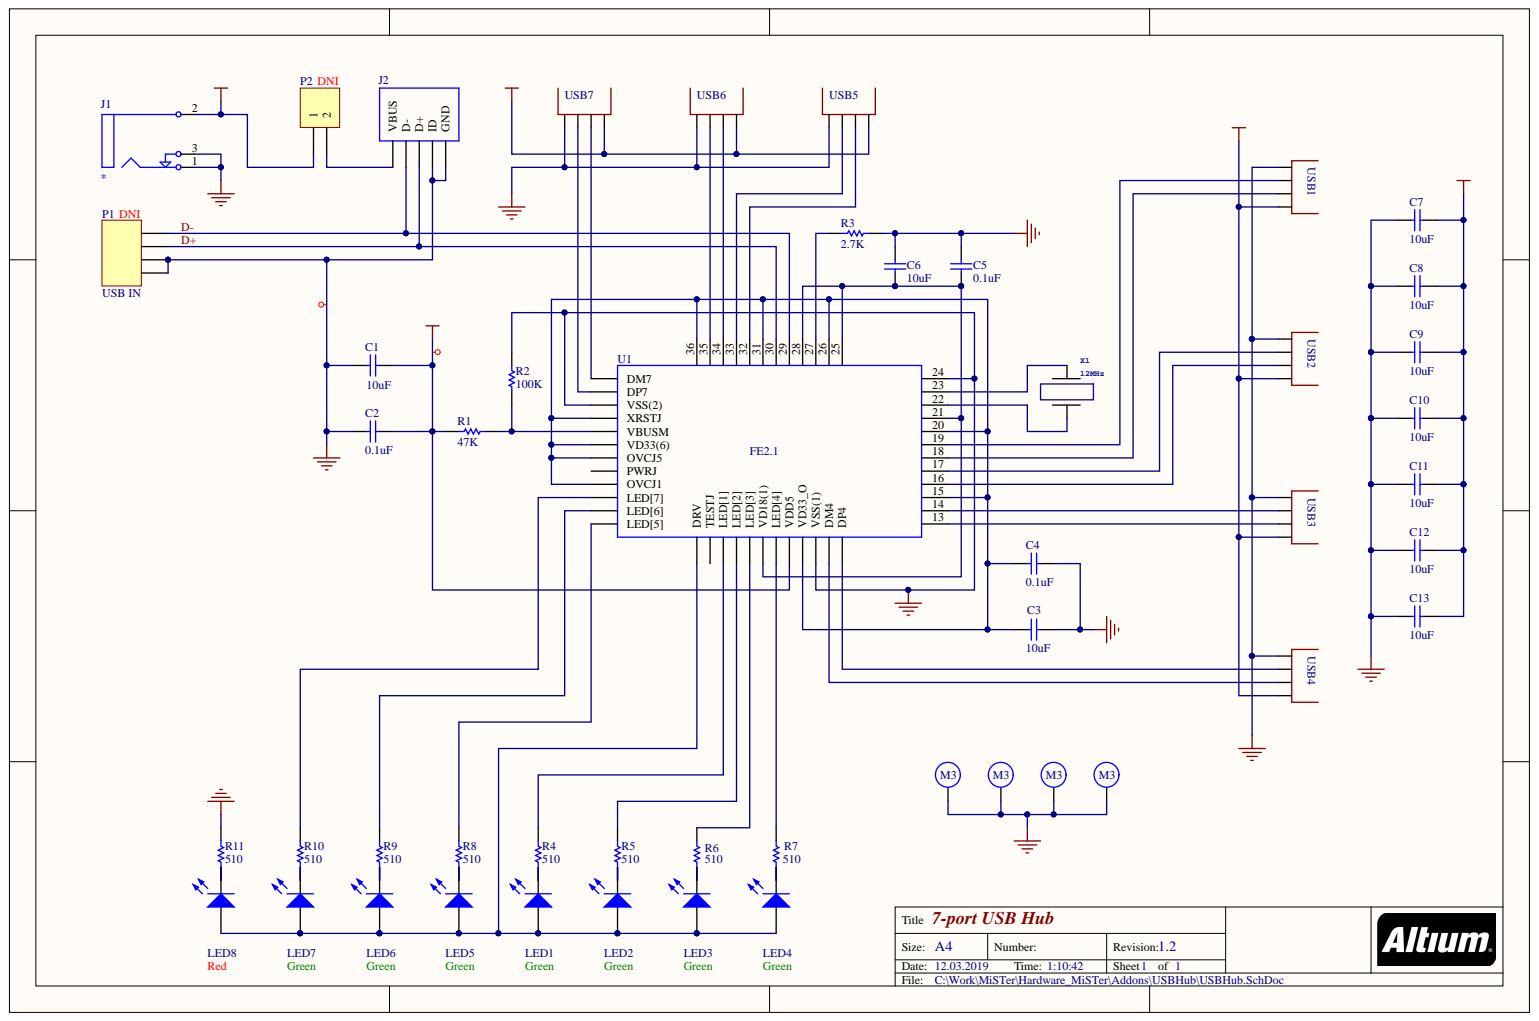
[picture p91: page 1]

7-port USB Hub Title

A4 Size: | Number: | 1.2 Revision:
Date: 12.03.2019 Time: 1:10:42 | | Sheet 1 of 1

C:\Work\MiSTer\Hardware_MiSTer\Addons\USBHub\USBHub.SchDoc

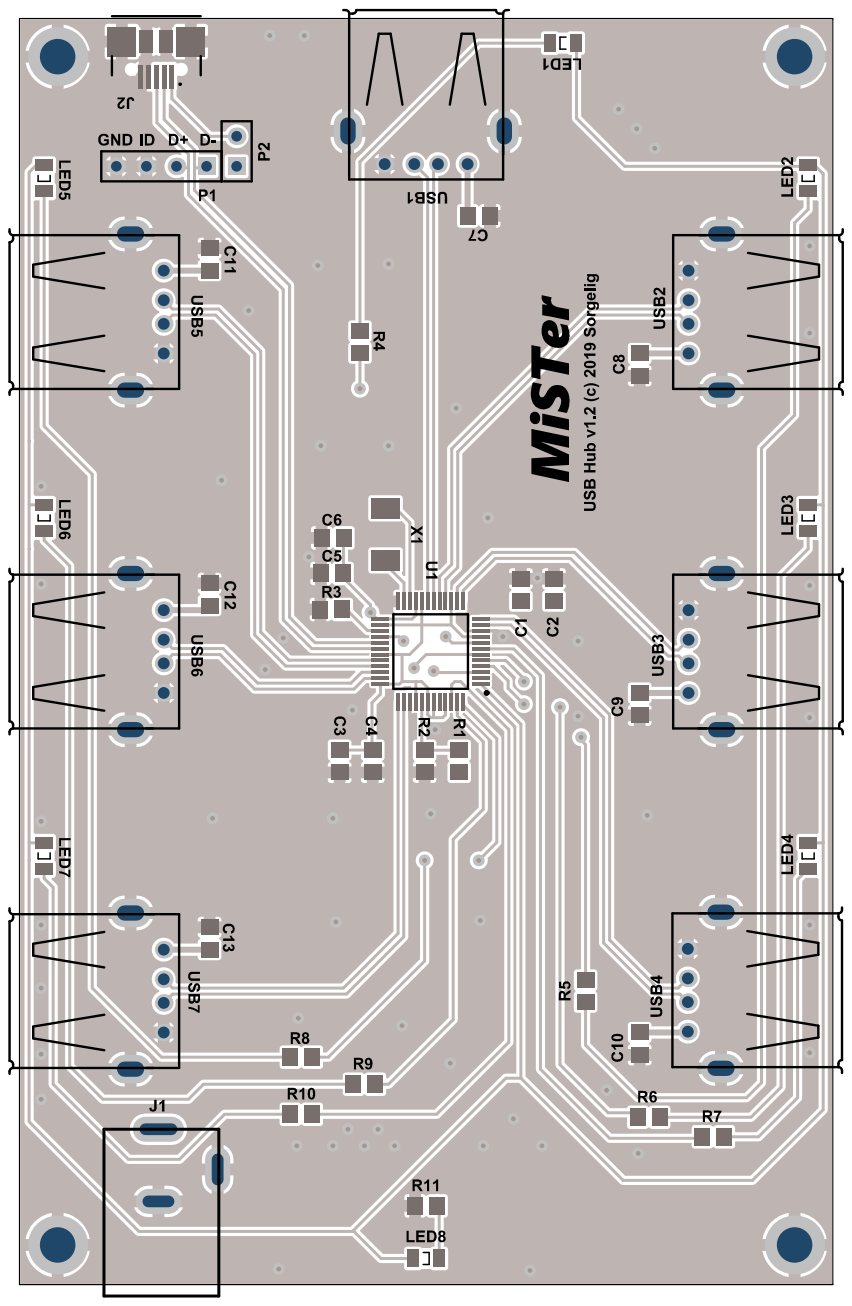
[picture p92: page 2]

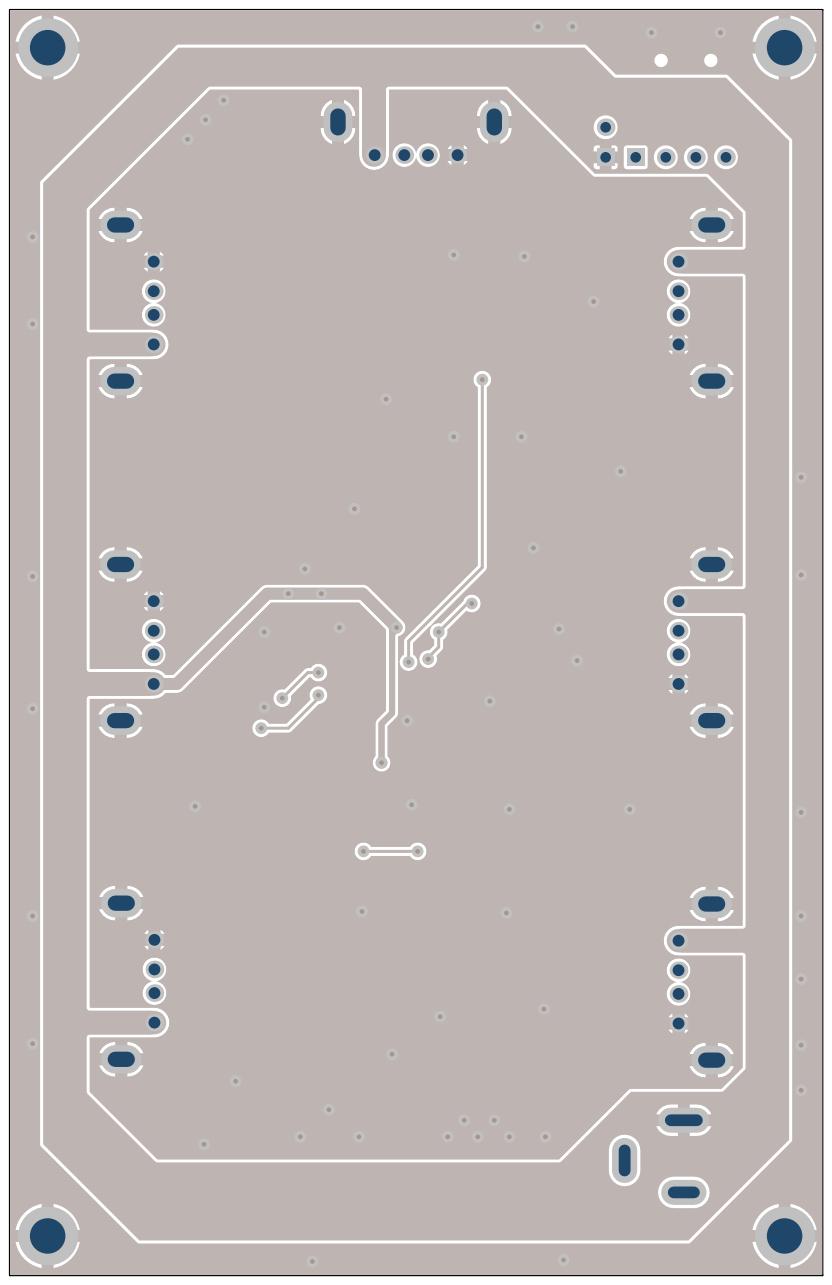
[picture p93: page 3]
