MiSTer-devel/Hardware_MiSTer/releases/USBHub_1.1.pdf

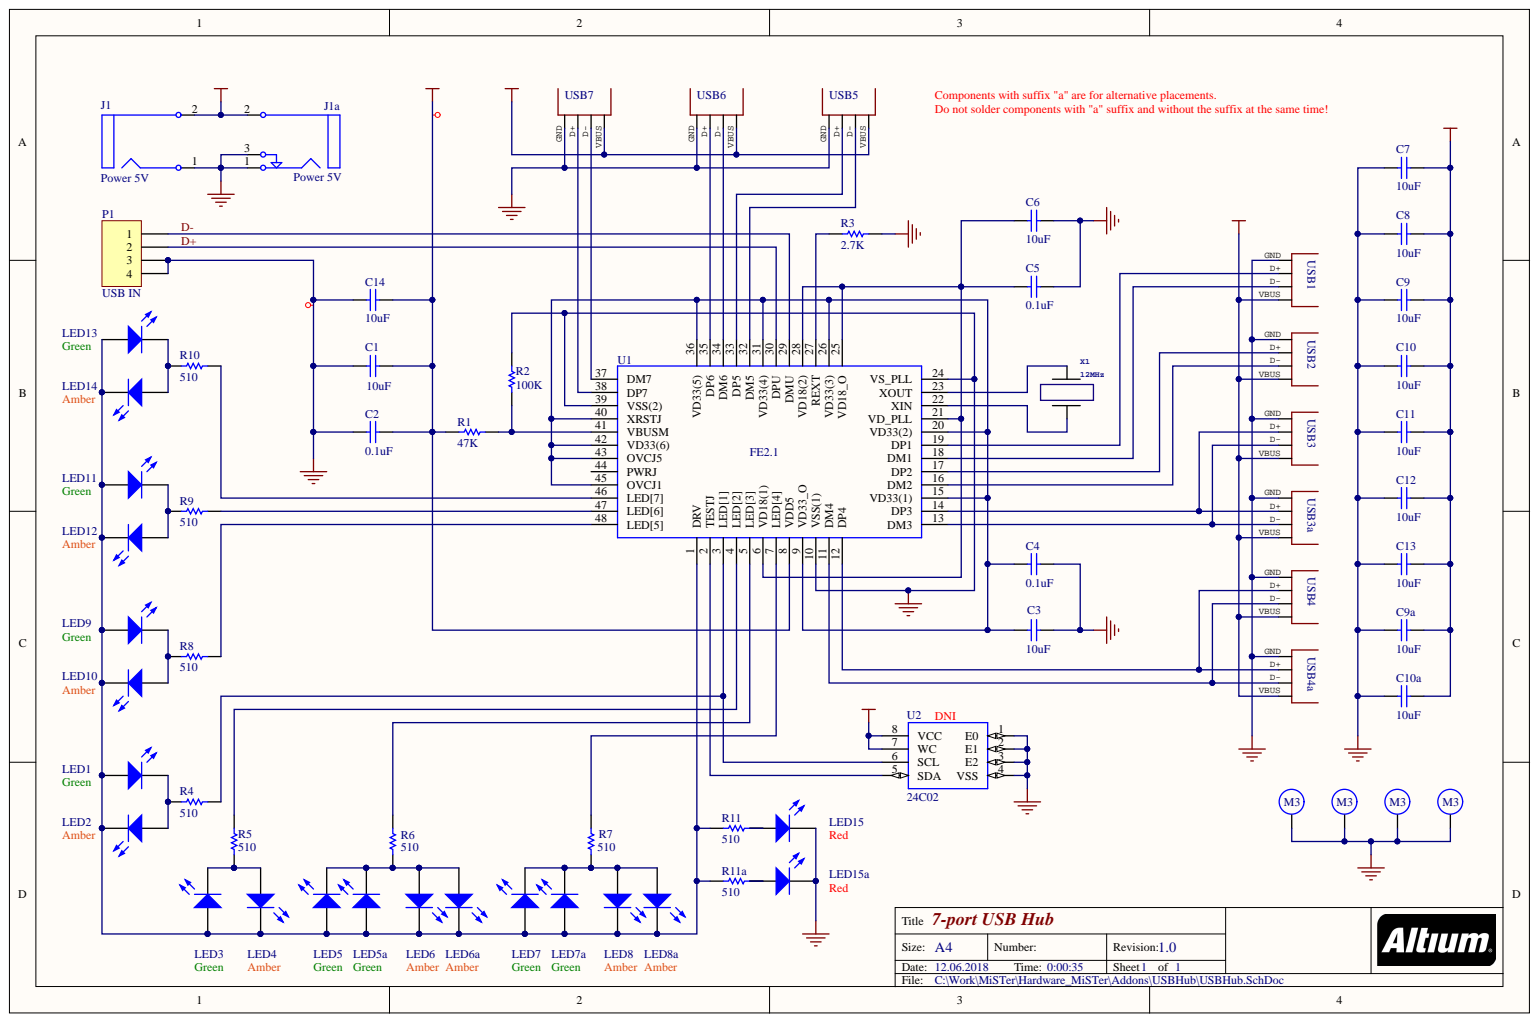
[picture p94: page 1]

Components with suffix "a" are for alternative placements.
Do not solder components with "a" suffix and without the suffix at the same time!

D+
D-
VBUS

C4 | VBUS

U2 DNI | VBUS

7-port USB Hub Title

A4 Size: | Number: | 1.0 Revision:
Date: 12.06.2018 Time: 0:00:35 | | Sheet 1 of 1

C:\Work\MiSTer\Hardware_MiSTer\Addons\USBHub\USBHub.SchDoc

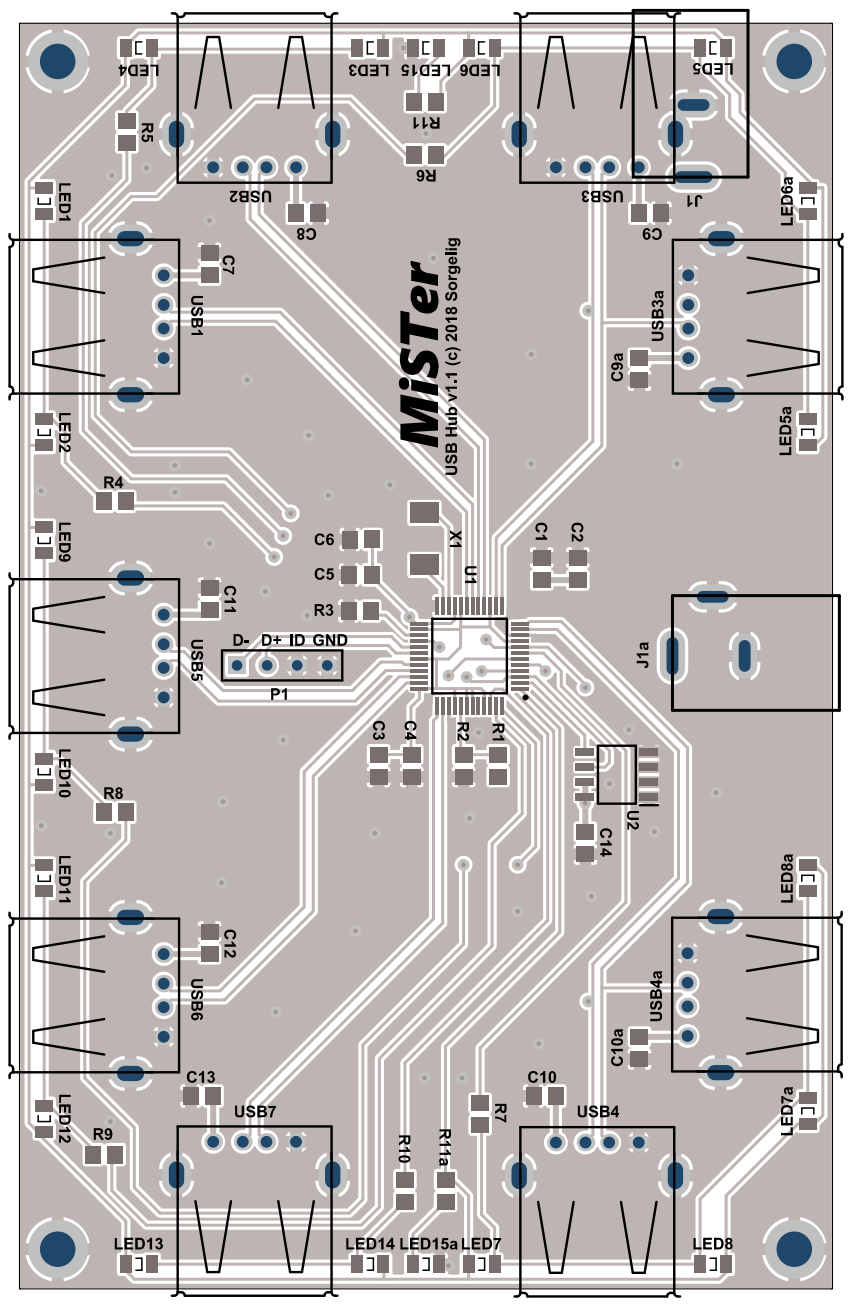
[picture p95: page 2]

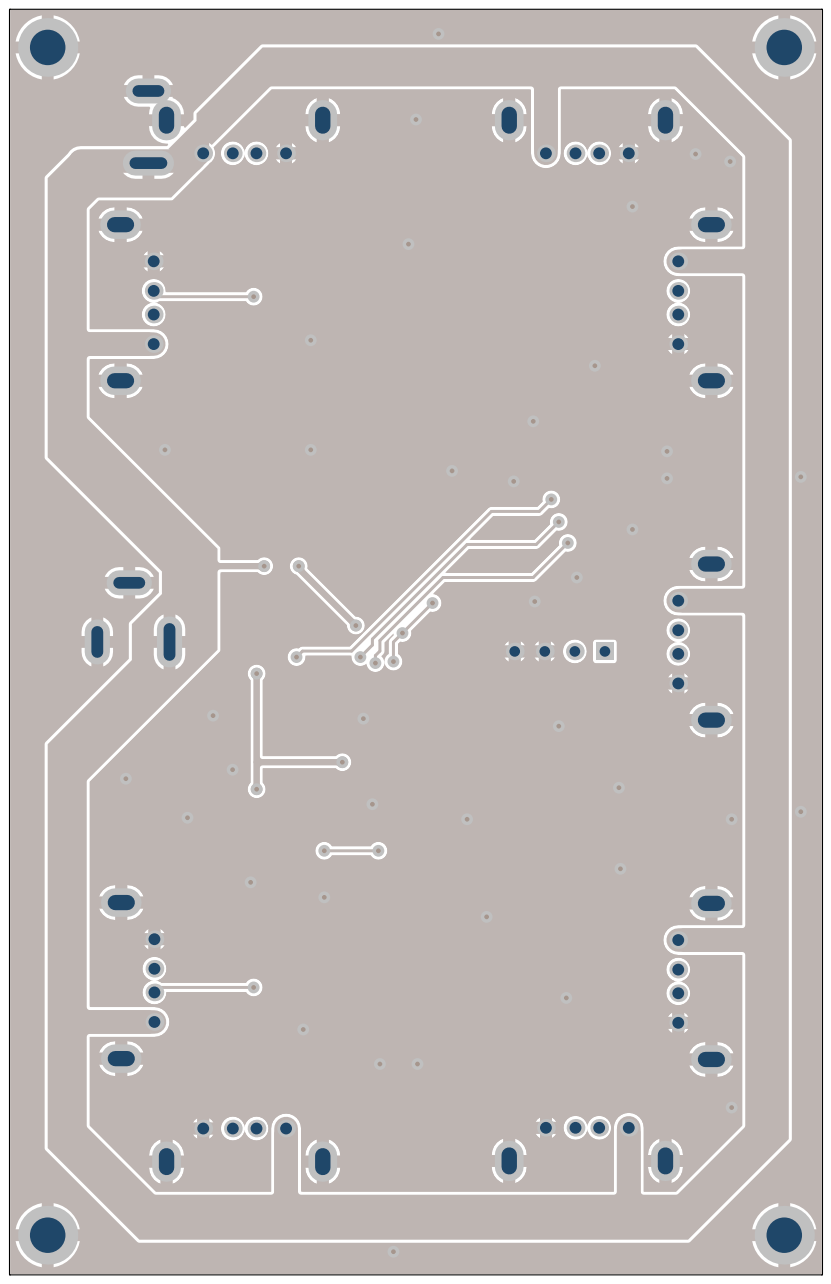
[picture p96: page 3]
