MiSTer-devel/Hardware_MiSTer/releases/PiTopUSBHub_2.0.pdf

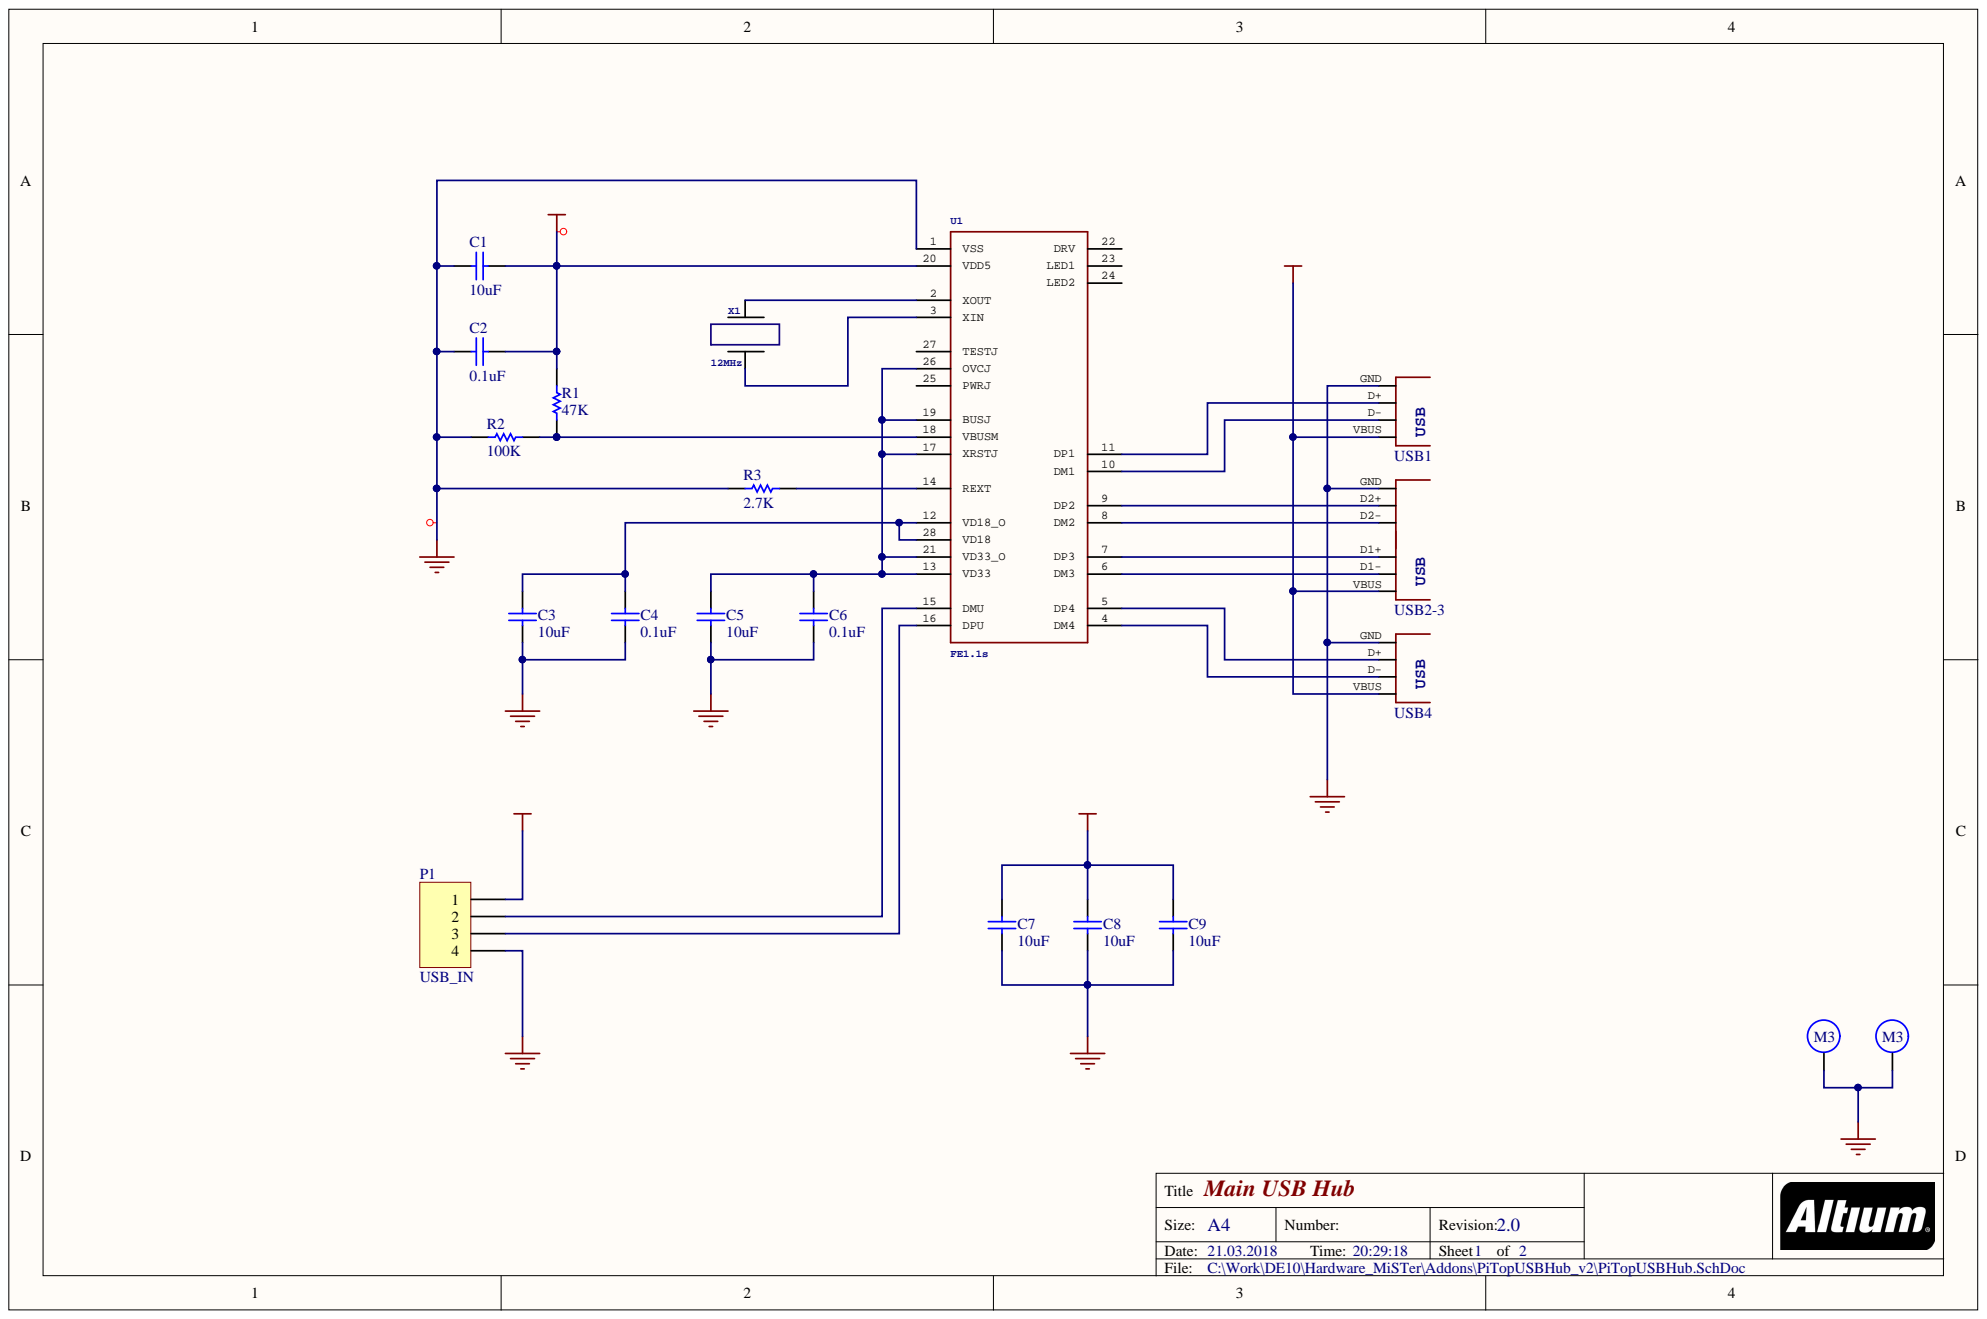
[picture p97: page 1]

PWRJ 25

VD33 13 | | D1-
DMU 15 | | VBUS

10uF | | 10uF | GND

D+
D-
VBUS

Main USB Hub Title

A4 Size: | Number: | 2.0 Revision:
Date: 21.03.2018 Time: 20:29:18 | | Sheet 1 of 2

C:\Work\DE10\Hardware_MiSTer\Addons\PiTopUSBHub_v2\PiTopUSBHub.SchDoc

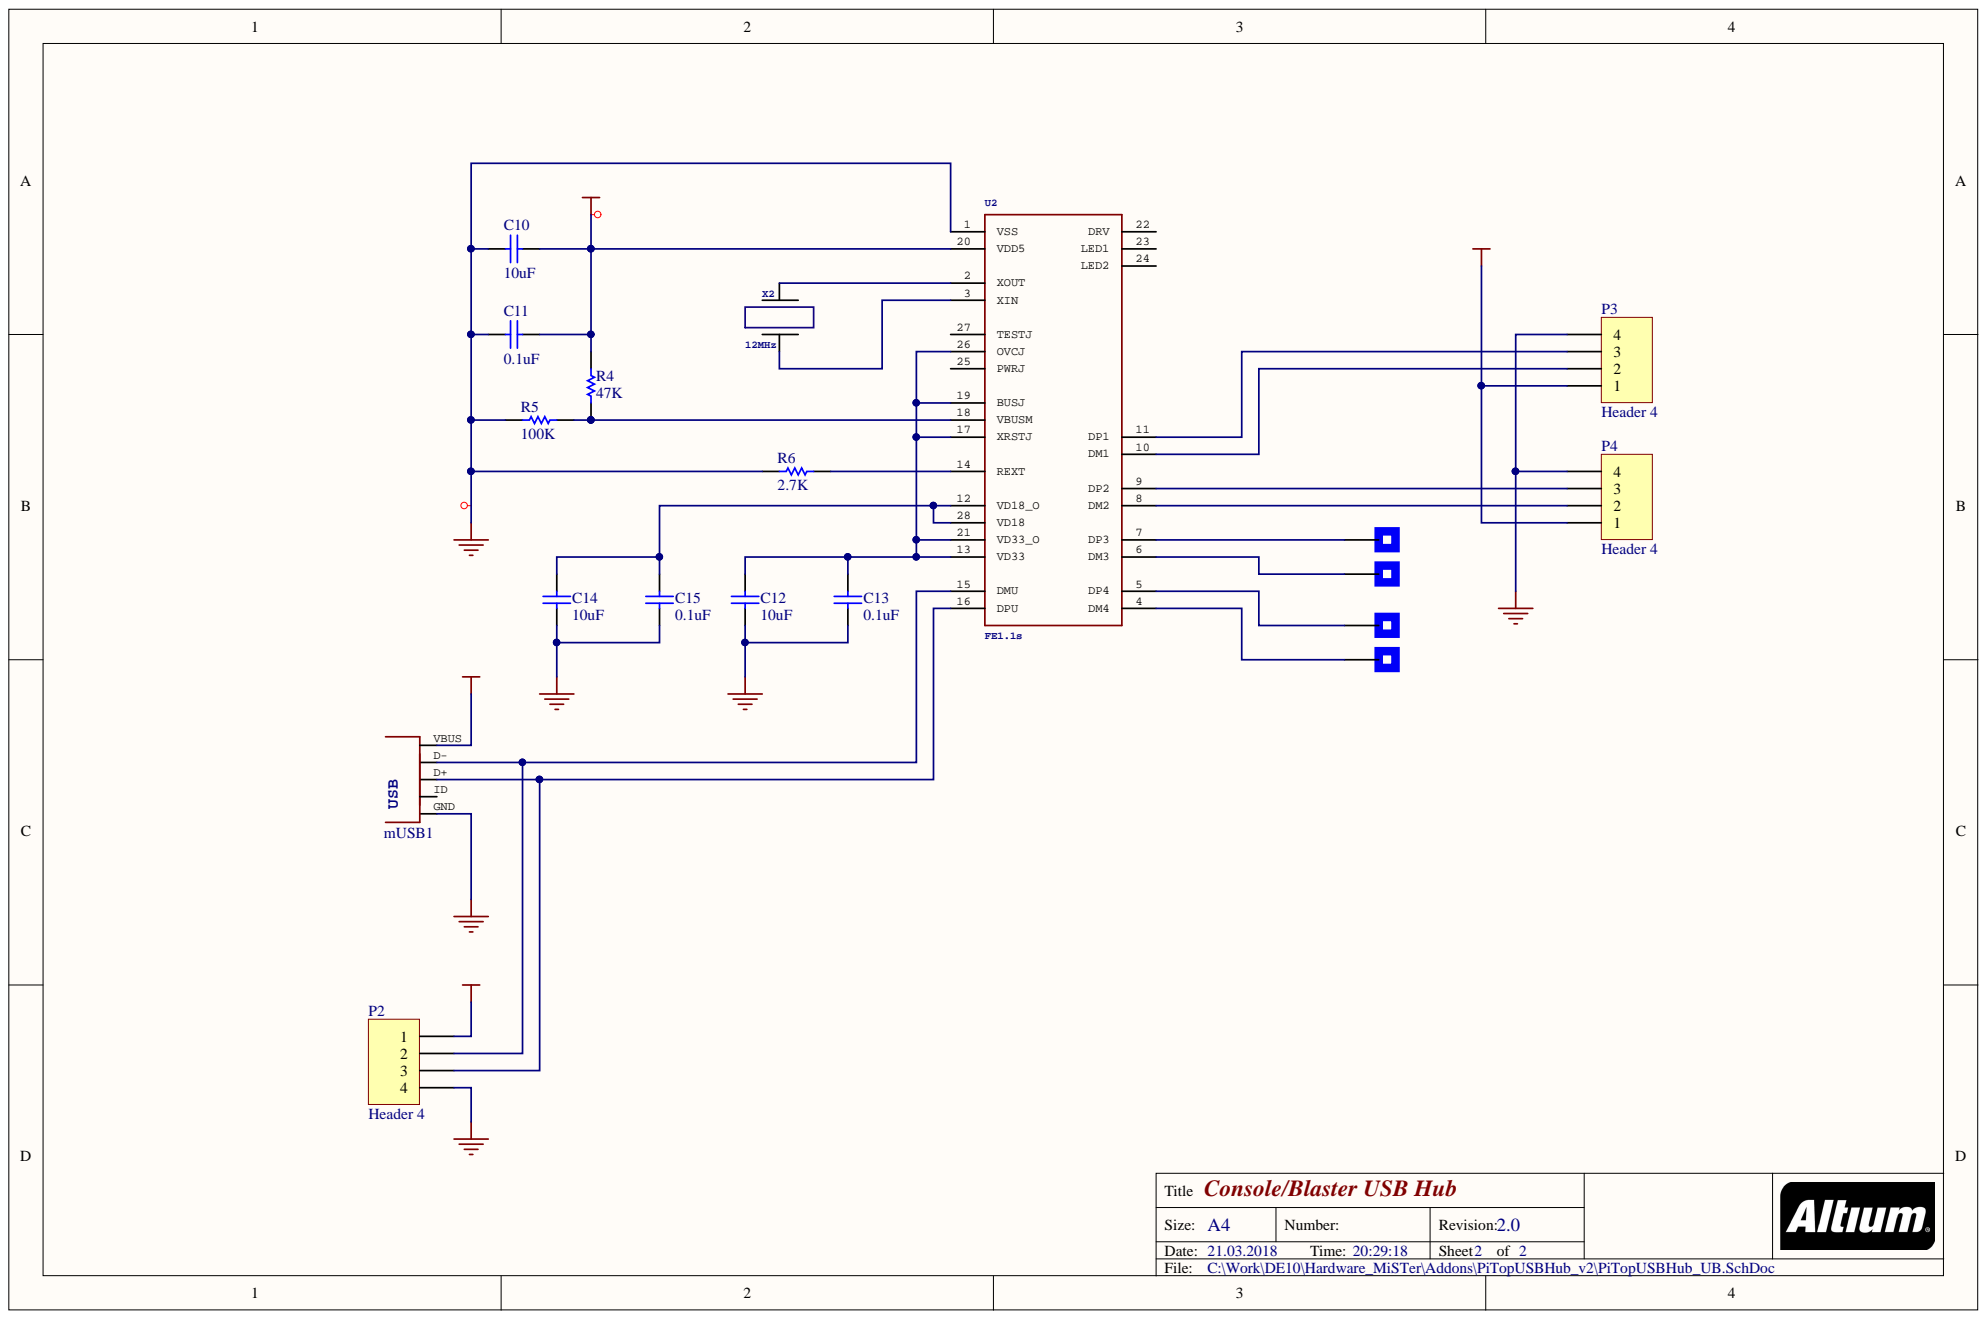
[picture p98: page 2]

PWRJ 25

BUSJ 19
VBUSM 18

DMU 15

C14 C15 C12 C13
10uF | 10uF

D+
ID

Console/Blaster USB Hub Title

A4 Size: | Number: | 2.0 Revision:
Date: 21.03.2018 Time: 20:29:18 | | Sheet 2 of 2

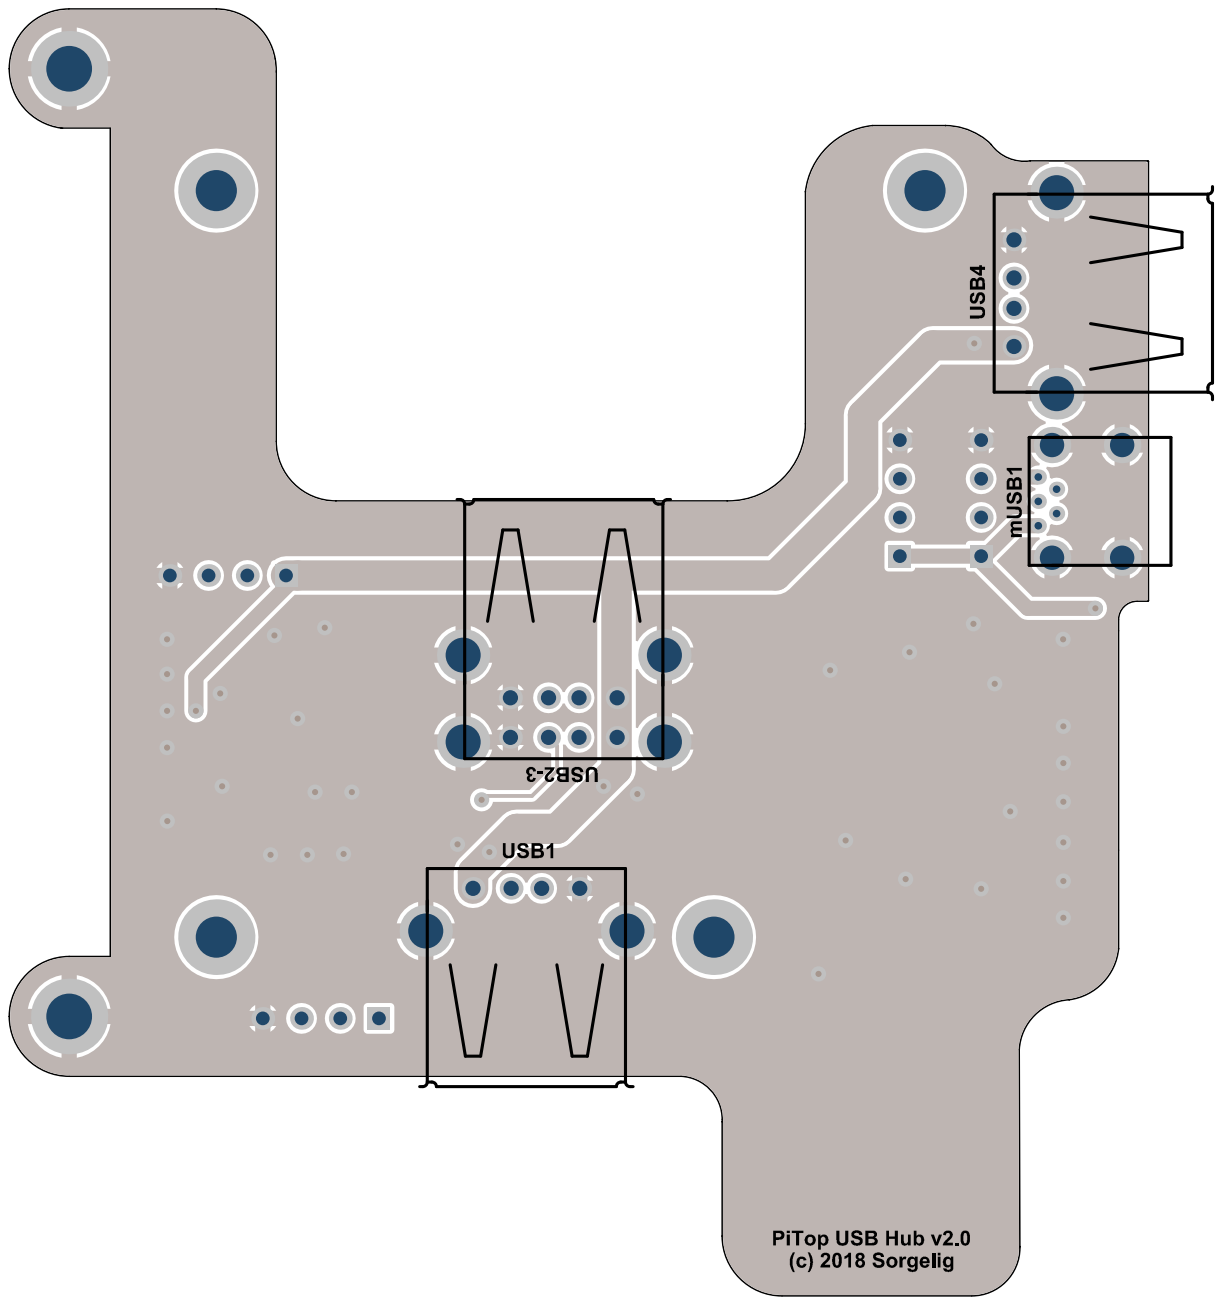
[picture p99: page 3]

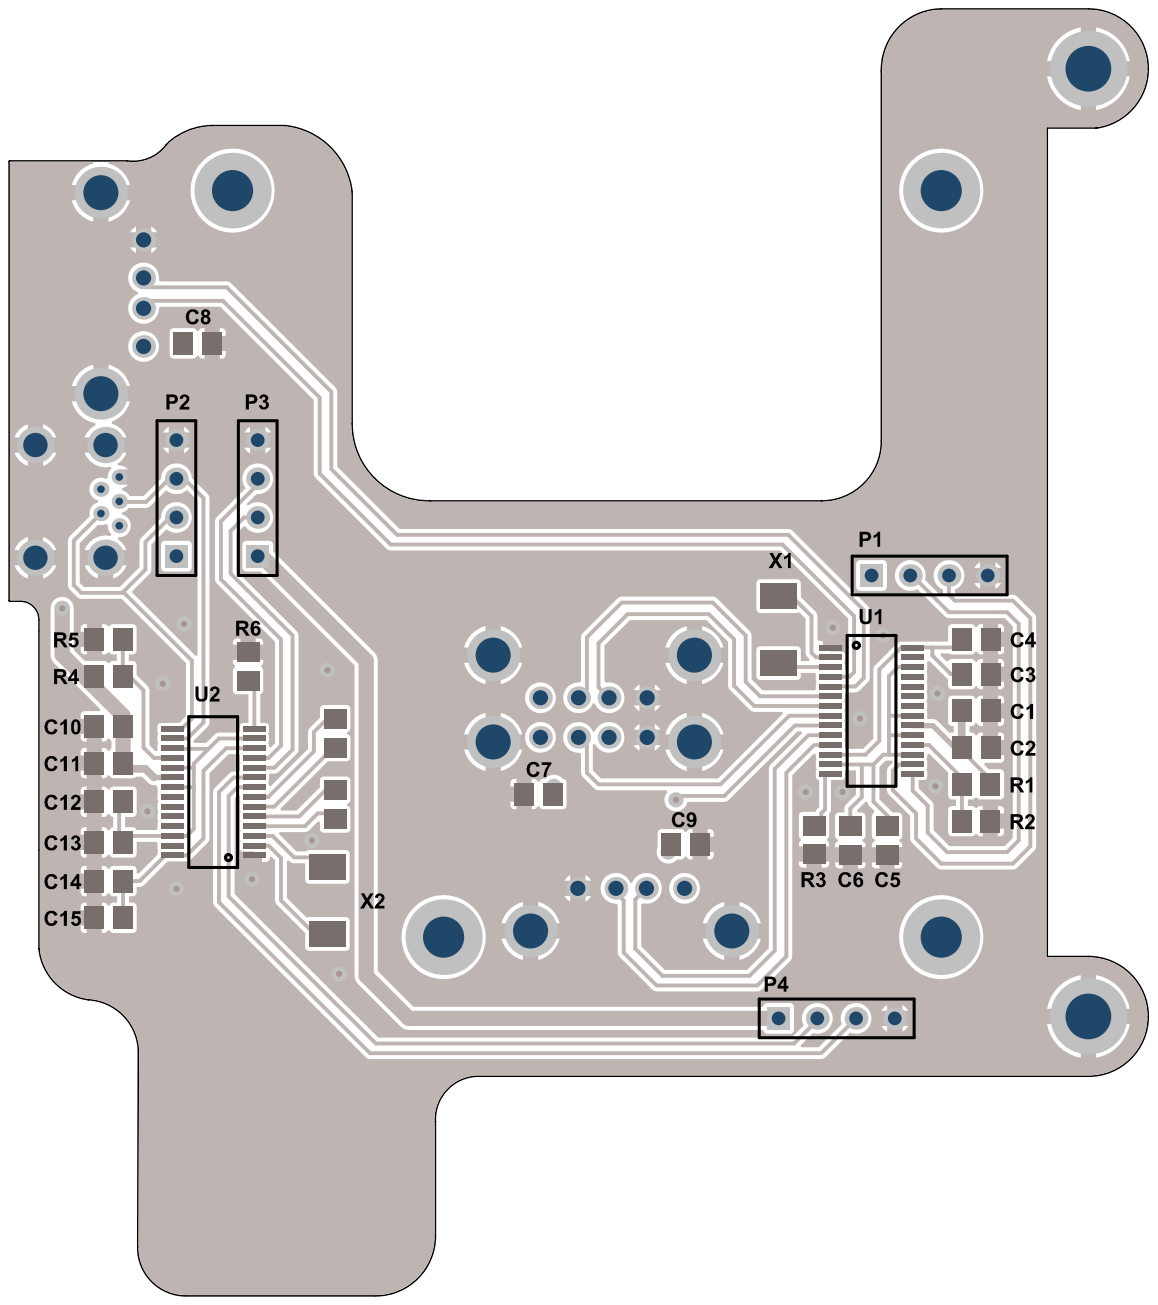
[picture p100: page 4]
