MiSTer-devel/Hardware_MiSTer/releases/PiTopUSBHub_3.0.pdf

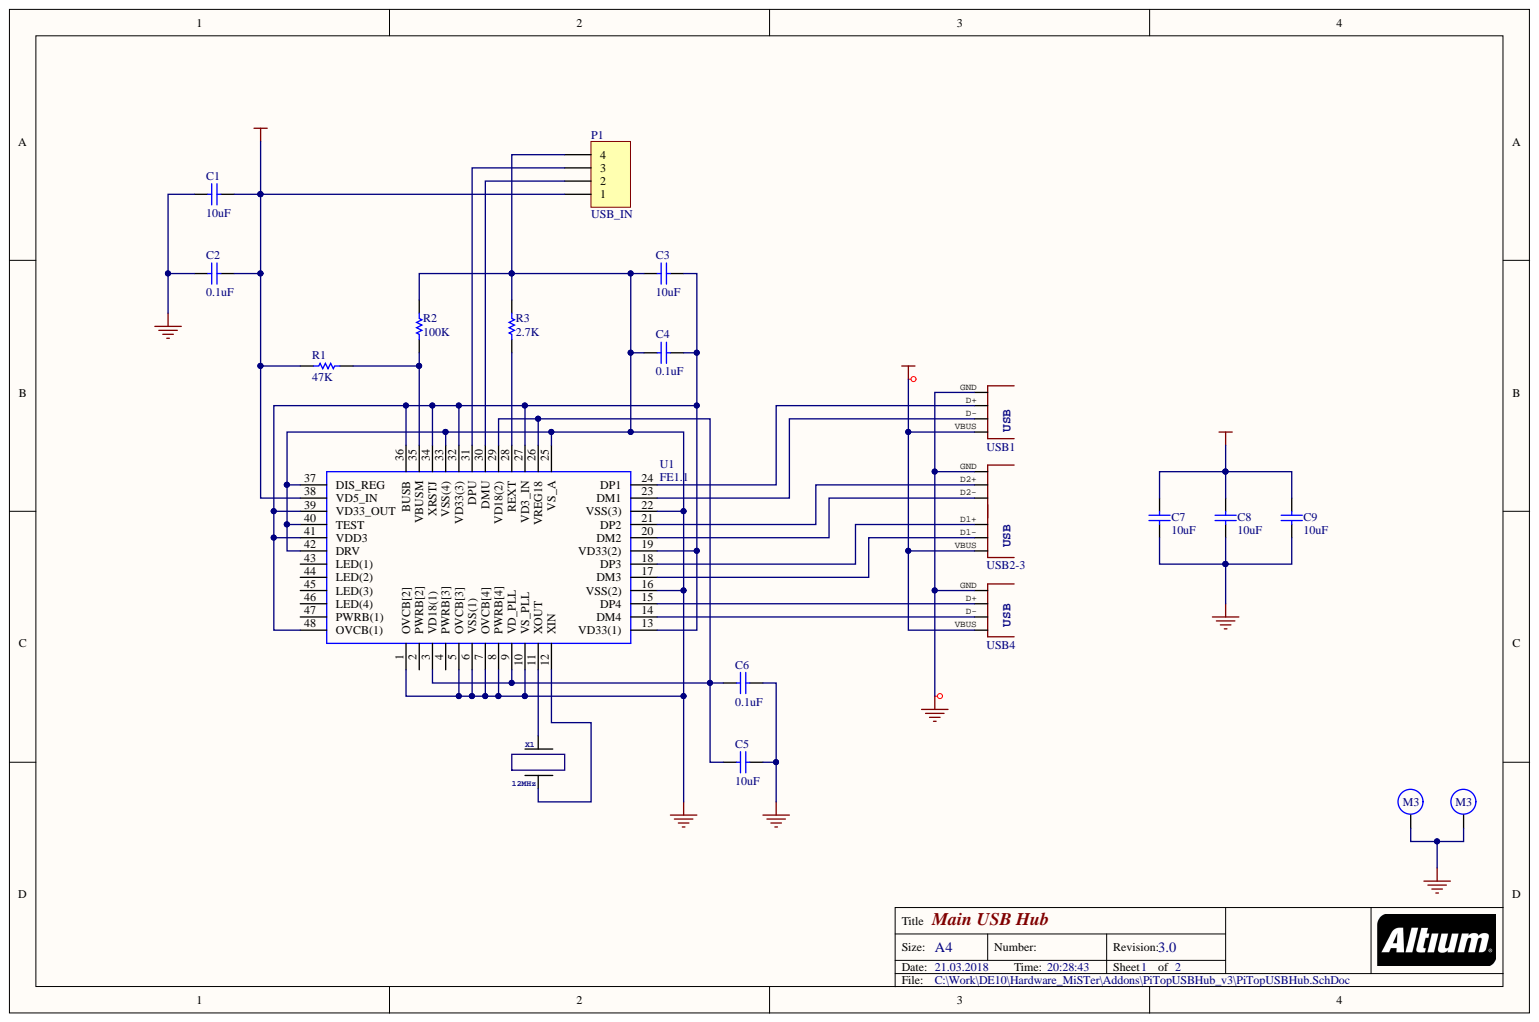
[picture p101: page 1]

D+
D-
VBUS

D2+
D2-

GND

Main USB Hub Title

A4 Size: | Number: | 3.0 Revision:
Date: 21.03.2018 Time: 20:28:43 | | Sheet 1 of 2

C:\Work\DE10\Hardware_MiSTer\Addons\PiTopUSBHub_v3\PiTopUSBHub.SchDoc

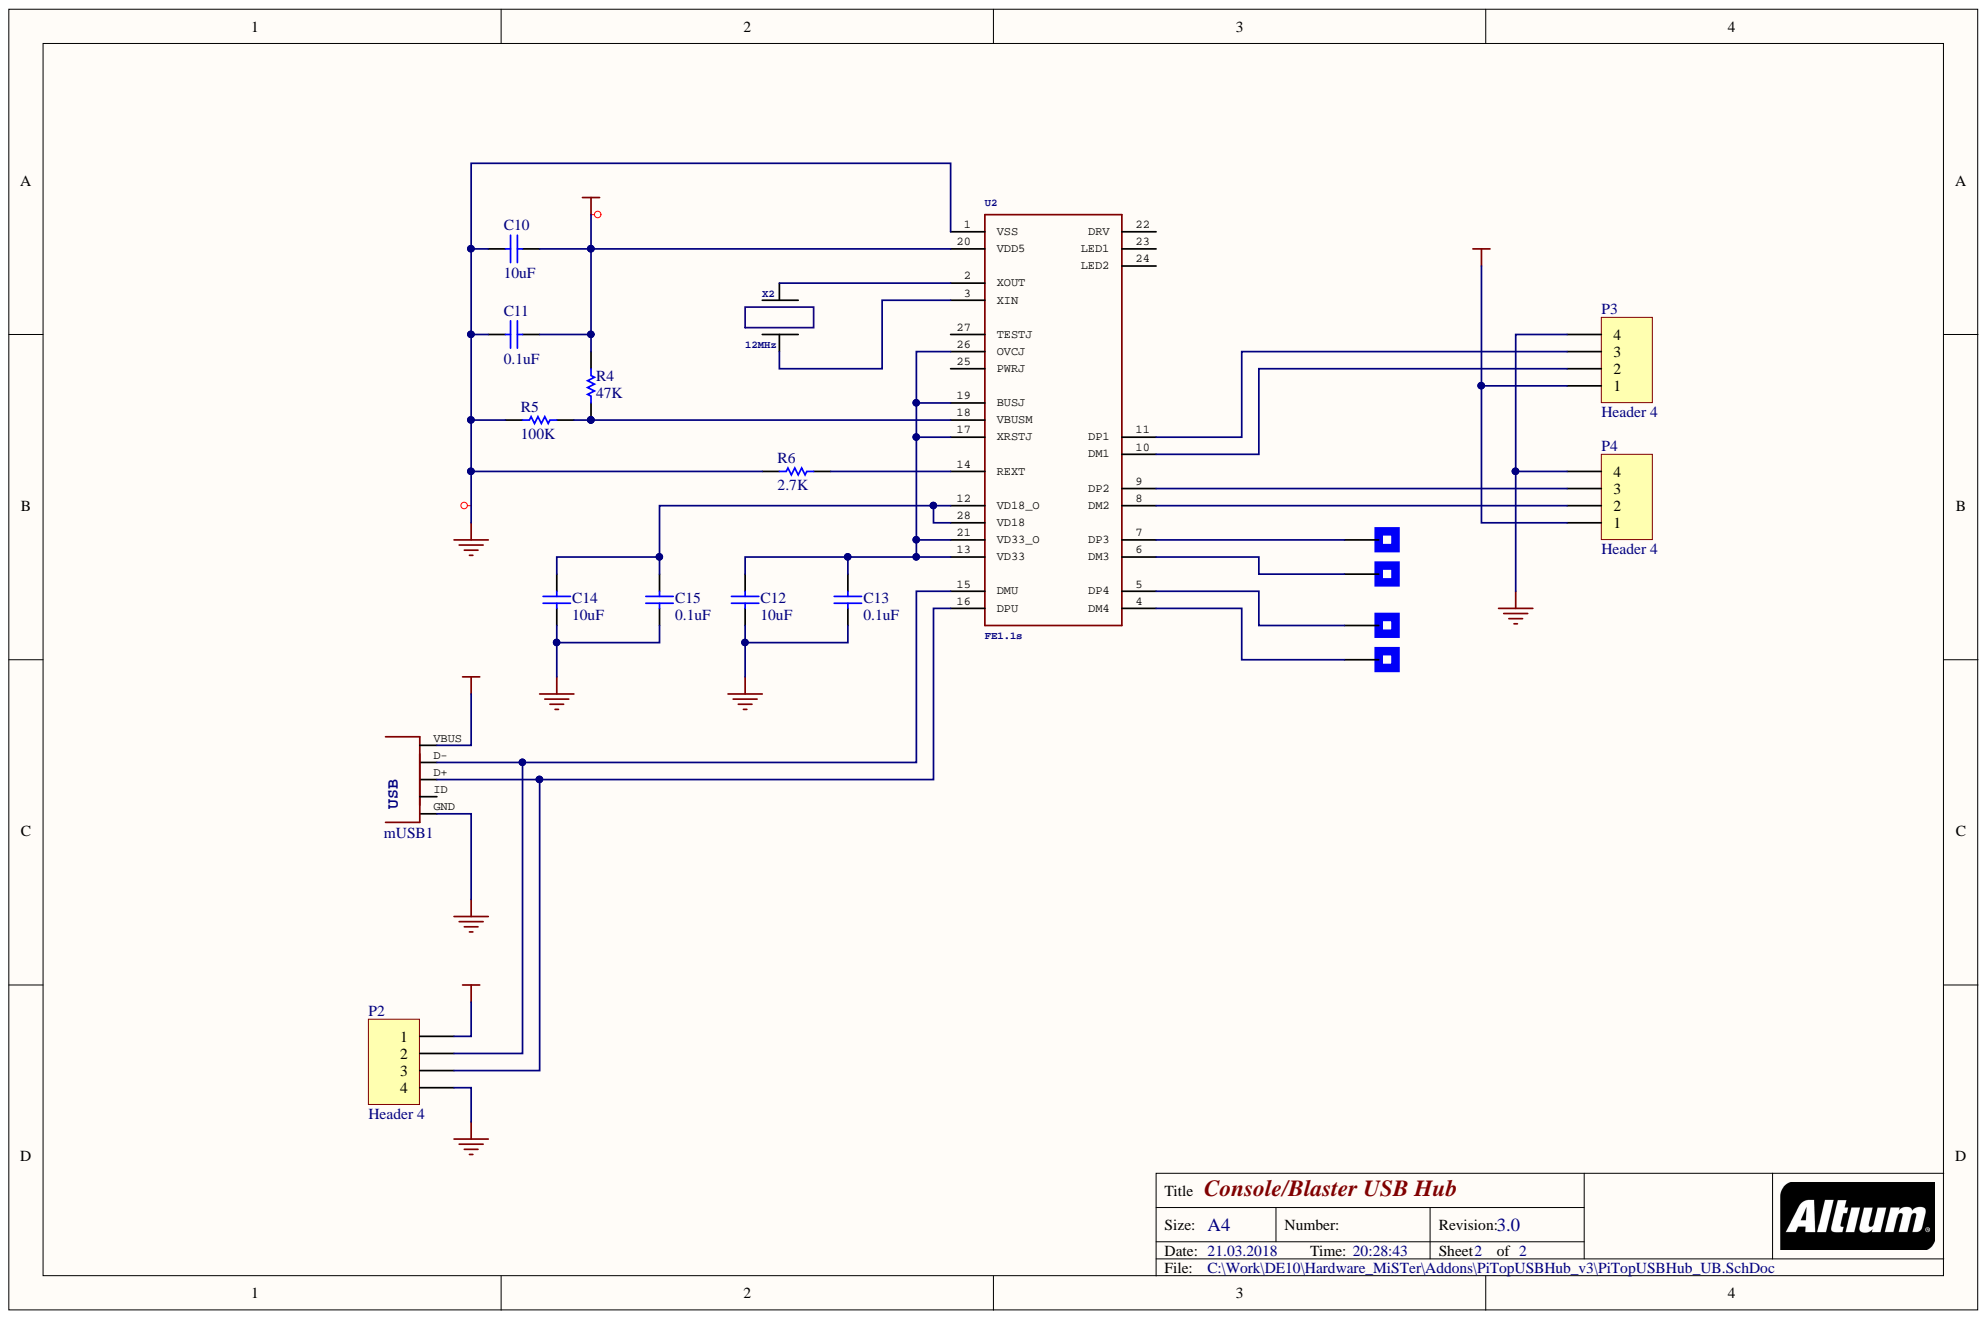
[picture p102: page 2]

PWRJ 25

BUSJ 19
VBUSM 18

DMU 15

C14 C15 C12 C13
10uF | 10uF

D+
ID

Console/Blaster USB Hub Title

A4 Size: | Number: | 3.0 Revision:
Date: 21.03.2018 Time: 20:28:43 | | Sheet 2 of 2

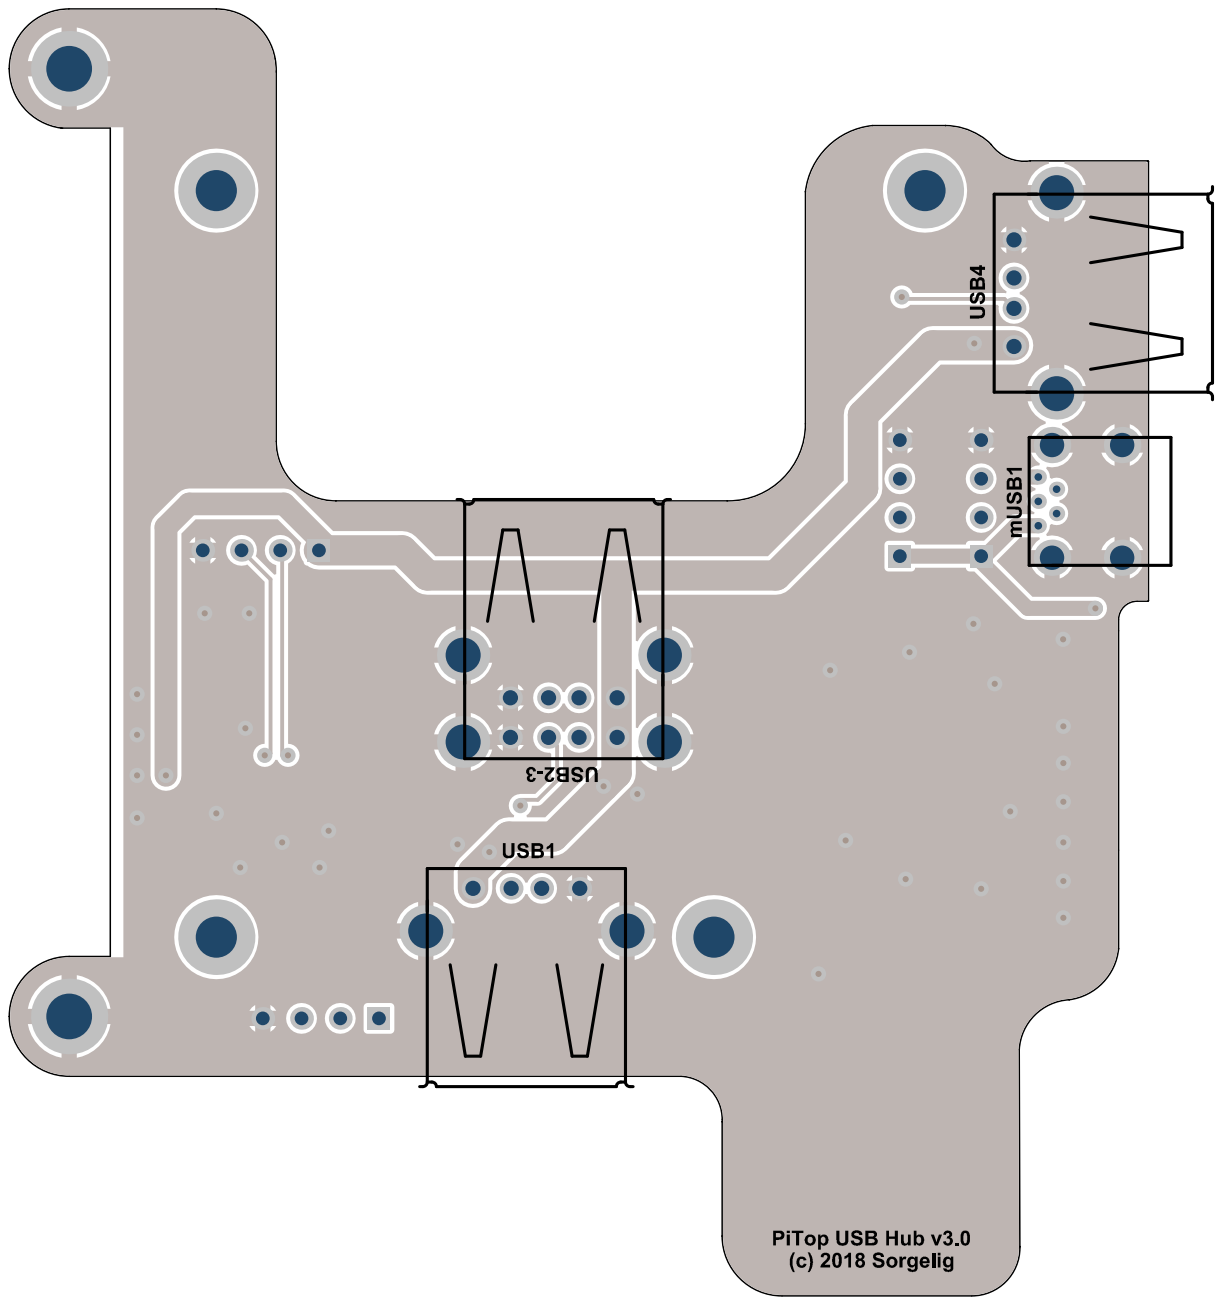
[picture p103: page 3]

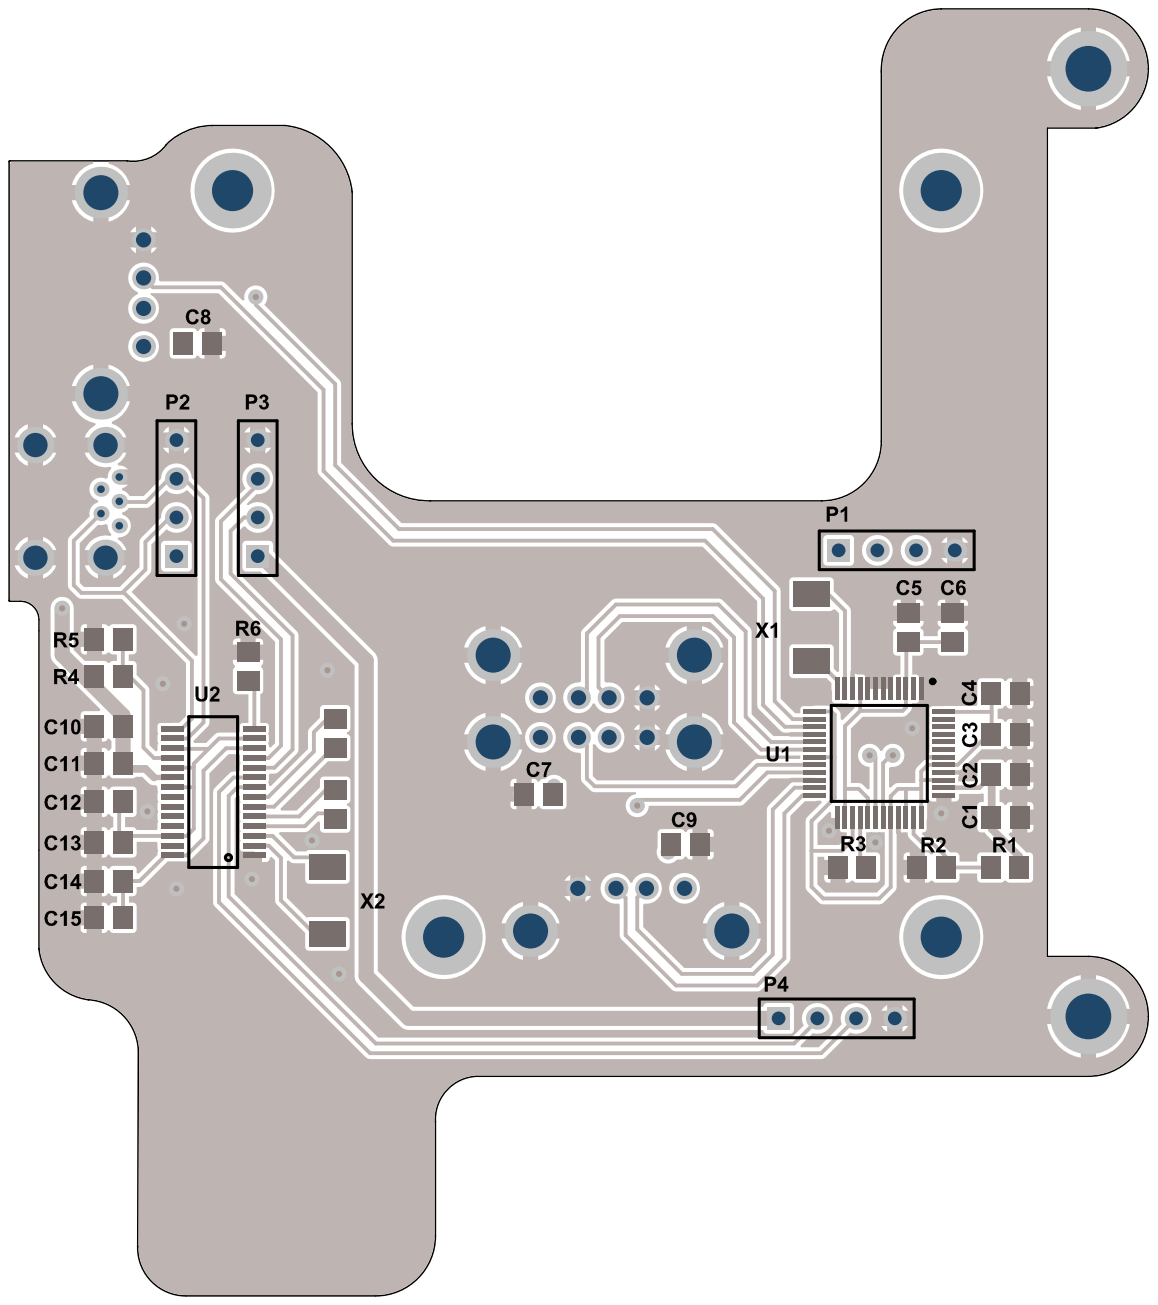
[picture p104: page 4]
